iandchasse/silkscreen-pcb/docs/audit-2026-09-30/reports/04_docs_sweep_1.01.md

# Docs staleness check (rev 1.01 x3 3V3 fix)

> Run on 2026-09-30, before commit `3edd0c8` existed: **HEAD / OLD / CONTROL = `6871962`** (design and production files
> identical to `aeb5b39`, the Rev 1.0 order) and **working copy / NEW / FIX = the change later committed as `3edd0c8`** (1.01).
> Evidence paths (`A_trim/`, `C_fab/`, `layout/` ...) are under [`../evidence/`](../evidence/), a local-only pack (git-ignored).

Status: complete -- see end of file

## Findings

### A1. x3 / trimmed-build charging statements (tracked files)
- INFO: No tracked doc ever stated that a trimmed board loses charging / Q2 / R81 / CE 3V3, and no tracked doc mentions a bodge wire. The issue lived only in untracked NOTICE.md. Nothing tracked becomes false.
- README.md:375-393 "Cutting the board down for a smaller display" lists what you lose (J6, U8, CR2, CR3, F2, SW10, H1, D3/D8). Still accurate after the fix (D3/D8 loss = owner's accepted risk).
- docs/HARDWARE.md:1570 cut-line row: "y = 61.86, x 84.42 ... 104.24 -- cutting here removes J6 with its protection parts (U8, CR2, CR3, D3, D8, F2), SW10 and mounting hole H1". Still accurate. Optional wording (info): append "3V3 to the Fix 4 charge-enable gate (Q2/R81) is fed from below the line, so a shortened board still charges."
  (Note: HARDWARE.md says cut line y = 61.86 while NOTICE.md/x3 trim uses y 62.00 -- pre-existing, not changed by this commit.)

### A2. Revision naming
- WARN: README.md:456 "| **Revision** | **Rev 1.0.** The revision label on both title blocks and in the name of the release zip changes only when a new board is fabricated; until then every change is folded into Rev 1.0. The design content is current to **2026-09-21** ..."
- WARN: docs/HARDWARE.md:37 same statement: "The design content is current to **2026-09-21**".
  Rev 1.0 WAS fabricated (ordered 2026-09-21, README.md:87-88). This commit changes copper + silk after that order, but keeps the "1.0" label, the same zip name and the "current to 2026-09-21" date. After push, "design content is current to 2026-09-21" is false, and the repo files no longer match the Rev 1.0 boards that were ordered.
  Minimal wording (keeping the owner's convention, not inventing one): change the date to the commit date and add one sentence, e.g.
  "The design content is current to **2026-09-30**. Changes since the 2026-09-21 order: one added 3V3 trace below the cut line so a shortened (x3) board still charges, and one silkscreen word. Boards from the 2026-09-21 order lack that trace."
  If the owner prefers a label bump, the stated rule ("changes only when a new board is fabricated") would make this Rev 1.01 at the next order; title block and zip name would then change together.
- INFO: Existing history-like sections: docs/HARDWARE.md:1429 "## 15. What changed from de-link" (a de-link -> Silkscreen summary, explicitly "rather than a commit-level changelog"). No per-revision changelog / revision history section exists in README.md, HARDWARE.md or fabrication/*.md. There is no conventional home for a Rev 1.01 entry; the Revision row (README.md:456 / HARDWARE.md:37) is the only place revision state is described.
- INFO: zip name Silkscreen_Reader_PCB_1.0.zip referenced at README.md:141, :151, :467 (still correct - file name unchanged).

### A3. Welcome silkscreen text
- INFO (image, public): docs/images/board-top.png (README.md:20 hero render, last changed 92b3e74 2026-09-21) visibly prints "All components will be on the back of this board, maximizing cost and / simplicity for DIY." After this commit the board says "cost-savings". Cosmetic mismatch only; re-render board-top.png (and board-bottom.png for the new B.Cu trace) at the next render pass, or accept.
- INFO (dated review archive, leave as-is): docs/final-review-2026-09-19/sections/11_mechanical_enclosure_assembly.md:655 quotes "All components will be on the back of this board, maximizing cost and simplicity for DIY"; docs/final-review-2026-09-19/sections/13_docs_end_user_readability.md:95-96 quotes the same text. These are dated snapshots of the 2026-09-19 review; they describe the board as it was. No edit needed (optionally a one-line "text since changed to 'cost-savings'" note, not recommended).

### A2b. Release-record dates made stale by the regenerated zip (fabrication/README.md)
- WARN: fabrication/README.md:32 (Release records table, Gerbers/drills row): "Toolkit output, regenerated 2026-09-21 after the slot, QR code, `U14`, `F2`, `R83`, `C34`, `H6` and the `H5` move. Checked against the saved PCB the same day: identical coordinate operations on `B.Cu`, `F.Cu`, ... `F.Silkscreen` ..." -- the zip being committed was regenerated ~2026-09-30 and now carries the new 3V3 trace, the PWR_BUTTON/LED_SW reroutes, the moved GND via and the silk word. The row's date and change list become false; the "checked the same day" claim no longer covers the file in the repo.
  Minimal wording: "Toolkit output, regenerated 2026-09-30 after one added 3V3 trace below the cut line (a shortened board still charges) and a one-word silkscreen edit; before that, 2026-09-21 after the slot, QR code, ... Re-verify after any board change." Drop or re-date the "Checked against the saved PCB the same day" sentence unless the gerber comparison is repeated for this zip.
- WARN (minor): fabrication/README.md:11 "The files in `production/` were regenerated on 2026-09-21 after those changes (see the table below)". After this commit the zip and netlist.ipc are from ~2026-09-30 (positions/bom/designators/jlc_bom are byte-identical to the 2026-09-21 set). Minimal wording: "... were regenerated on 2026-09-21 after those changes, and the Gerber zip and `netlist.ipc` again on 2026-09-30 after the 3V3 trace fix (see the table below) ..."
- INFO: fabrication/README.md:20 "production/other_fabs/ (last regenerated 2026-09-21, 165 placed parts)" -- still true: other_fabs holds BOM/centroid/assembly-drawing files, and no footprint/placement changed. README.md:295-299 says other fabs "use the same Gerber zip as the JLCPCB order" -- still true.
- INFO: fabrication/README.md:10 "184 references = 165 fitted + 11 DNP + 8 bare-copper ... as of 2026-09-21" -- still true (no reference change).

### A2c. Plots / renders that this change makes non-current
- WARN: docs/HARDWARE.md:39-41 "> **Current full plots (2026-09-21):** [`silkscreen_pcb_schematic.pdf`] ... and [`silkscreen_pcb_layout.pdf`] (PCB layout: front view, then the back as you see it) are ... plotted from the current source." docs/silkscreen_pcb_layout.pdf was last committed in aeb5b39 (2026-09-21 02:42), the same commit as the last committed board, so it is current at HEAD and becomes stale with THIS commit (no new 3V3 trace/reroutes, old Welcome wording). README.md:525 links the same "PCB layout PDF". Minimal fix: re-plot docs/silkscreen_pcb_layout.pdf in this commit, or reword to "Current full plots (schematic 2026-09-21; layout 2026-09-21, before the 2026-09-30 3V3 trace below the cut line)". The schematic PDF is unaffected (no schematic change).
- INFO: docs/images/board-top.png / board-bottom.png (README.md:20) predate the change (see A3). No text claims they are current; cosmetic.
- INFO: docs/mechanical/silkscreen_pcb.step (README.md:429, HARDWARE.md:1547 "authoritative source is the 3D model") contains only the board body and components (no track or silkscreen solids; grep finds only PRODUCT 'silkscreen_pcb_PCB'). No outline/footprint change in this commit, so it stays valid.
- INFO: production/other_fabs/assembly_drawing_bottom.pdf -- assembly drawing; no footprint change, stays valid.

## Scope B -- sibling repos (report only; not changed in this commit)

### silkscreen-light-strip (tracked files, HEAD b44f225 2026-09-30)
- WARN: docs/DESIGN.md:34 "**The trim also cuts 3V3 to Q2/R81**, so the charger's enable stays low and the x3 board will not charge. ... the next silkscreen-pcb revision fixes it with one trace (see that repo's `NOTICE.md`)." -- after this push the fix exists and NOTICE.md is gone (dangling pointer).
  Minimal wording: "**On boards from the 2026-09-21 order, the trim also cuts 3V3 to Q2/R81**, so the charger's enable stays low and the x3 board will not charge. One wire from a retained 3V3 point to Q2 pad 2 / R81 pad 2 fixes a built board. silkscreen-pcb fixed it on <date/commit> with a 3V3 trace below the cut; boards made from those files charge after the trim."
- WARN: docs/DESIGN.md:331 "5. **Board issues on the x3 build** (§1): no D3/D8, and the trim cuts 3V3 to the charger enable. Both are to be fixed in the next silkscreen-pcb revision (one trace for the charger enable), and are tracked in `NOTICE.md` in the silkscreen-pcb repo. Boards already built need the bodge wire described there." -- now false on three counts: D3/D8 will NOT be fixed (owner's decision), the charge-enable fix is done, and NOTICE.md (which held the bodge-wire description) is deleted.
  Minimal wording: "5. **Board issues on the x3 build** (§1): no D3/D8 (accepted; handle the strip ESD-safe). The trim cut 3V3 to the charger enable on boards from the 2026-09-21 order; those need one wire from a retained 3V3 point to Q2 pad 2 / R81 pad 2 (e.g. bridge the two cut 3V3 stubs at the edge). silkscreen-pcb fixed it with one trace below the cut on <date>."
  Note: because NOTICE.md is being deleted, the bodge-wire instructions (bridge the stubs at x 87.53 and 100.60 at y 62, or R40 pad 2 -> R81 pad 2) will survive only if copied into light-strip / case-368 docs or the silkscreen-pcb commit message.
- WARN: enclosures/case-368/README.md:833-838 "**The trim cuts 3V3 to Q2 and R81 (charge enable).** Their only 3V3 feed ran above the cut (KiCad y 60.3-60.8). ... so **the x3 board will not charge.** ... Suggested fix: one wire ..." under heading (826) "Board notes (x3 board with the strip): flagged, not fixed". Now fixed upstream for new boards.
  Minimal wording: prefix "On boards from the 2026-09-21 order, ..." and add "Fixed in silkscreen-pcb on <date> (a 3V3 trace below the cut); boards from those files need no wire." Heading could become "flagged; charge enable fixed upstream".
- WARN: enclosures/case-368/README.md:985-986 "**The Q2/R81 3V3 feed** on the x3 board: as trimmed, the board will not charge. A bodge wire fixes built boards; the next silkscreen-pcb revision fixes it with one trace (its `NOTICE.md`)." -- dangling NOTICE.md reference; fix now done.
  Minimal wording: "... A bodge wire fixes boards from the 2026-09-21 order; silkscreen-pcb fixed it with one trace on <date>."
- INFO: docs/DESIGN.md:33 and :98 (D3/D8 removed by the trim; "the trimmed 3.68" board has neither") -- still true, consistent with the owner's decision. No change.
- INFO: enclosures/case-368/hardware/reference/board-trim.md:152 "3V3 crosses the edge twice and GND uses pours; pad membership alone is not a full connectivity or physical damage analysis." -- still true (the two 3V3 crossings of y 62 remain; the fix adds a path below the cut). Optional add: "Since <date> silkscreen-pcb also joins those two 3V3 feeds below the cut, so Q2/R81 keep 3V3 after the trim."
- INFO: enclosures/case-*/hardware/board-2026-09-21/silkscreen_pcb.kicad_pcb are dated snapshots of the pre-fix board. Correct as snapshots; any future trimmed-board check run from them will still show the two unconnected 3V3 items.

### A1b. Deleting NOTICE.md drops the only in-repo record of the fix for boards already ordered
- WARN: The boards from the 2026-09-21 order (README.md:87-88) were made from the pre-fix files, so a trimmed one still will not charge without a wire. NOTICE.md is the only place in silkscreen-pcb that says so and gives the bodge ("bridge the two cut 3V3 stubs at the edge (x 87.53 and 100.60 at y 62)" or "R40 pad 2 to R81 pad 2"), plus the post-fix check ("DRC on a copy trimmed at y 62 ... no unconnected 3V3 items"; bench "CE reads 3V3 with a correctly oriented cell"). Once it is deleted, README.md:375-393 (public "Cutting the board down" section) lists what a cut loses but never says that Rev 1.0 boards from the first order also lose charging. The light-strip docs point readers to NOTICE.md for the wire (see Scope B).
  Minimal wording, one bullet added to README.md "Cutting the board down for a smaller display": "- **Boards from the 2026-09-21 order: add one wire after cutting**, or the board will not charge. The cut removes the only 3V3 feed to the charge-enable gate (`Q2`/`R81`). Bridge the two cut 3V3 stubs at the edge, or run a wire from `R40` pad 2 to `R81` pad 2. Boards made from the files after <date> have this trace built in." (Alternatively put the same text in the commit message, but a commit message is not where a builder will look.)

### A4. Routing descriptions
- INFO: No tracked doc describes the 3V3 crossings of y 62, PWR_BUTTON routing near y 64-66, LED_SW routing near (98.65, 64.8-65.15) or the moved GND via. README.md:383 "with live copper crossing it" and the dated review FINAL_REVIEW.md:54 / FINDINGS_TABLE.md:86 ("12 live nets ... cross it") stay true: the new trace and all reroutes are below the cut, and both 3V3 crossings remain.
- INFO: D3/D8 wording is consistent with the owner's decision: README.md:385-388 ("A cut board therefore runs its frontlight without those two clamps"), docs/HARDWARE.md:1200-1202, :1570. No doc presents D3/D8 as protecting a trimmed build. (README.md:248 "Don't leave D3 off instead: it protects the light connectors (J3, J6)" is about the full-size board; still true.)

### A5. References to NOTICE.md
- INFO: No tracked file in silkscreen-pcb references NOTICE.md (checked every tracked file, .gitignore included). All tracked "NOTICE" references mean the licence file `NOTICE` (README.md:541, final-review archive DOCS-08/DOCS-15 rows), which stays. Deleting NOTICE.md leaves no dangling link inside this repo.

### A6. Other checks
- INFO: Title block unchanged in both copies: (date "2026-09-12") (rev "1.0"). README.md:456 / HARDWARE.md:37 "the title-block date (2026-09-12) is when Rev 1.0 was opened" stays true.
- INFO: DESIGN_REVIEW.md:9 "the saved manufacturing files match the current board" stays true, given that the owner regenerated the zip after the save.
- INFO (dated audit, leave as-is): docs/audit-2026-09-18/checkpoint-2/status_table.md:85 "welcome-text-missing-noun | low | OPEN | welcome text unchanged ('12-pin accessory connected on the top...')" -- this commit edits the same text box but leaves that wording ("... via 12 pin accessory connected on the top of the other side", visible in docs/images/board-top.png). Optional: while the box is open, "connected" -> "connector". Not required.

### Scope B (continued)
- WARN: silkscreen-site/silkscreen-main/public/order/Silkscreen_Reader_PCB_1.0.zip (tracked in the site repo; dist/order/ has a copy) is byte-identical to the silkscreen-pcb HEAD zip (md5 e138ff6a...). The regenerated working zip is d22ae633..., so after this push the site holds the pre-fix Gerbers under the same file name. scripts/pricing/order_files.py:23-25 copies it from ../../de-link_pcb/production ("the unchanged Gerber zip"). ORDER_FILES_OPEN is false (src/lib/config-data.ts:70), so the builder does not offer it now, but files in public/ are normally deployed as-is. Follow-up in the site repo: rerun `python scripts/pricing/order_files.py` (and rebuild) after the push.
- INFO: silkscreen-site otherwise has no text about the charge-enable island, bodge wire, trim 3V3 crossings or the Welcome wording. Its "Rev 1.0" copy (src/components/build-availability.tsx:216 "the first Rev 1.0 boards were ordered on September 21, 2026", configurator.tsx:1355/1408 "These are the Rev 1.0 files", CLAUDE.md:459 "The board is **Rev 1.0** until another board is fabricated") mirrors the pcb repo's label rule. If the owner keeps "Rev 1.0" (A2), the site's "Rev 1.0 files" will be the post-fix files while "Rev 1.0 boards" are the pre-fix ones -- same naming ambiguity as A2.
- INFO: silkscreen-enclosure-codex-x3 (not a git repo) hardware/reference/board-trim-codex-x3.md:152 "3V3 crosses the edge twice and GND uses pours; pad membership alone is not a full connectivity or physical damage analysis." -- same text as the light-strip copy; still true. Its board copies (hardware/board-2026-09-21/, hardware/frozen/, hardware/silkscreen_pcb-portable.kicad_pcb) are pre-fix snapshots. No charge-enable/bodge/NOTICE.md/Welcome text found in its md/txt/py files (.venv excluded).
- INFO: silkscreen-light-attachment design/final-audit.md:57 (untracked) mentions "untracked `NOTICE.md` (15:13; content "Charge enable loses 3V3 when the board is trimmed (x3 build)" ...)" -- a dated audit observation; no change needed.

Status: complete (22 tool calls). No blocker found.
