iandchasse/silkscreen-pcb/docs/final-review-2026-09-19/FINDINGS_TABLE.md

# All findings — final review 2026-09-19

Generated from the structured results of the 13 auditors and 12 verifiers (`findings.json`). *Severity* is the severity **after** verification; *was* shows the auditor’s original grade where the verifier changed it. 
Verdicts: `confirmed`, `confirmed-with-corrections` (the section file carries the corrected numbers), `refuted`, `unverifiable`, `added-by-verifier`, `not-verified` (section 13, documentation, had no verifier — it is editorial judgement).
Full evidence, calculations and sources for every ID are in the section file named in the last column.

## BLOCKER (1)

| ID | Finding | Verdict | Recommendation | Section |
|---|---|---|---|---|
| LED-01 | J3 (and J2/J4) signal pads have no solder-paste apertures - connectors will not be soldered in a fab-assembled build | confirmed | Add B.Paste to pads 1-N of all three HRS_FH34SRJ-* footprints (or override per-pad on the board), re-export the paste gerber, and re-verify by counting flashes on the connector rows before placing any assembly order. Costs nothing; without it the board returns with no display, no front light and no touch. | [07](sections/07_led_frontlight_driver.md) |

## HIGH (16)

| ID | Finding | Verdict | Recommendation | Section |
|---|---|---|---|---|
| BOM-01 | R14 ordering code has 12 pieces in stock; a fee-free Basic alternative the docs say does not exist *(was BLOCKER)* | confirmed-with-corrections | Change R14's LCSC field to C22939. It is in stock, it is JLC Basic (saves a ~$1.50 Extended loading fee) and it is half the price. The only spec difference is tempco, +/-400 ppm/C vs Yageo's +/-200 ppm/C, which over a 60 C rise is 2.4 % on a current-sense value and immaterial here. Keep Yageo RC0603FR-072R2L as the DigiKey-prim… | [12](sections/12_bom_function_and_cost.md) |
| DOCS-01 | No firmware exists or is linked, and no document says so | not-verified | Add a Software section to the README stating plainly what exists today, where it lives, and the literal first-power-up command. If no firmware is released, say so in the first 20 lines — it changes who should attempt this build. | [13](sections/13_docs_end_user_readability.md) |
| DOCS-02 | The README's recommended ordering route is a configurator that does not exist | not-verified | Demote to a one-line "a configurator is planned at silkscreenreader.com" note and make the manual path in steps 1-7 the primary, unqualified instruction. Remove or re-source the $29.55 figure. Do not describe an unavailable tool as the recommended route. | [13](sections/13_docs_end_user_readability.md) |
| DOCS-03 | Three BOM files offered as interchangeable; two contain duplicate LCSC codes that break the JLCPCB match | not-verified | Name exactly one file in the ordering step: "Upload production/bom_JLC_upload_v4_optimized.csv." Move bom.csv and v3 to a reference note, and state the duplicate-code failure mode in the README where the reader meets it, not only in the NextPCB notes. | [13](sections/13_docs_end_user_readability.md) |
| DOCS-04 | No shopping list for anything that is not on the PCB | not-verified | Add a "What else you must buy" table to the README: panel variant mapped to which optional blocks to fit, with vendor link and price; battery (single-cell 4.2 V, capacity, JST-PH 2.0 connector, pin 1 = B-); microSD; USB-C cable; M2 screws and standoffs; case. | [13](sections/13_docs_end_user_readability.md) |
| DOCS-05 | No safety warning of any kind on a board that charges a lithium cell | not-verified | Add a boxed safety block near the top of the README: LiPo pigtail polarity is not standardised; J5 pin 1 (marked -) is battery negative; meter the cell's leads before plugging in; use a cell with its own protection board; do not charge unattended; do not use a puffed cell. Repeat it in the first-power-up section. | [13](sections/13_docs_end_user_readability.md) |
| DOCS-06 | README's first instruction sends a newcomer into a 100 KB engineering review | not-verified | Re-order the README per the outline in the section file. Keep the DESIGN_REVIEW pointer but place it under "For engineers / before you modify this design", not as step 0 for a builder. | [13](sections/13_docs_end_user_readability.md) |
| DOCS-07 | "Case agnostic" means no enclosure files and no published mechanics | not-verified | Either publish the reference enclosure, even roughly, or add a Mechanical section: outline 60.05 x 111.30 x 1.6 mm, the five M2 hole coordinates, connector and button edge positions, the battery cut-out, and an exported board STEP. State explicitly that no case is supplied. | [13](sections/13_docs_end_user_readability.md) |
| DOCS-08 | Public URL on the board, in NOTICE and in both title blocks lands on a different project | not-verified | Before any board is handed to anyone: merge 06_2026 into master or change the repository's default branch, add a description and topics, and confirm the README renders on the landing page. No other documentation fix matters until a reader can reach the files. | [13](sections/13_docs_end_user_readability.md) |
| DOCS-09 | README says choose JLCPCB "Standard" without preparing the reader for Standard's size, edge-rail and fiducial requirements | not-verified | Explain why Standard is mandatory (the module is Standard-only), and warn that JLCPCB will add edge rails to reach the Standard minimum — expect a rail on each long edge, a small extra cost, and rails to snap or file off. Ask the reader to confirm in the DFM preview that the rails do not cross the four 0.5 mm perforation slots … | [13](sections/13_docs_end_user_readability.md) |
| HMI-01 | Raw LiPo P+ exposed on J6 pin 12 with no fuse, PTC or any series element | confirmed | Fit a 0.5-1 A PPTC (1206) in series with J6 pin 12 and add a BAT+ warning to the silkscreen. About ten cents, and it turns a smoke failure into a click-off failure. Not called a BLOCKER because the DW01A is present and the owner assembles the boards himself. | [08](sections/08_buttons_rtc_touch_expansion.md) |
| LAY-01 | Four tongue-neck routed slots are 0.50 mm wide, below every common fab's minimum slot width | confirmed | Widen all four neck slots to >= 1.0 mm and redraw all five slot polygons at 0.05 mm line width to match the rest of the outline. Get an explicit DFM answer from the fab before ordering; treat this as a blocker if they cannot cut 0.5 mm, because the likely silent outcomes are that the slots are widened (changing the cut line) or… | [10](sections/10_layout_area_walk.md) |
| MEC-01 | Flex slot is 1.30 mm wide — narrower than the 1.60 mm board — and is the only path for all three display flexes *(was BLOCKER)* | confirmed-with-corrections | Widen the slot to >= 2.5 mm, ideally 3.0 mm, and radius or chamfer both lips. A 3 mm slot still leaves 4.05 mm of the 5.75 mm bezel strip below it. Also confirm the fab will route a 47 mm slot that close to the edge. | [11](sections/11_mechanical_enclosure_assembly.md) |
| MEC-02 | The 'cut for smaller displays' line severs raw battery positive 0.15–0.20 mm from ground pour on both layers | confirmed | Add a bold silkscreen warning 'DISCONNECT BATTERY BEFORE CUTTING' next to the existing note. Better: add a 2 mm-wide copper keep-out band centred on y = 61.86 so no copper at all crosses the cut face, or route P+ to J6 by a path that does not cross the line. | [11](sections/11_mechanical_enclosure_assembly.md) |
| MEC-23 | Top face is not flat: 58 soldered through-hole leads protrude inside the panel's footprint | confirmed-with-corrections | Decide and document the panel seating plane. Preferred: clip and file every through-hole lead flush on the panel side during assembly (add it as an explicit build step, with a straightedge check) so the panel can sit flush and the flex slack is preserved. Alternative: design the case to hold the panel on a >= 1.5 mm standoff, a… | [11](sections/11_mechanical_enclosure_assembly.md) |
| SD-V01 | The microSD card-insertion corridor runs straight through the battery cut-out | added-by-verifier | Settle this before the enclosure and ideally before ordering, since one of the three answers is a respin. (a) Confine the cell to the upper-left of the cut-out so a channel at least ~17.5 mm wide and ~20 mm deep stays clear in front of J7, and record the resulting maximum cell dimensions in HARDWARE.md section 5 and in the encl… | [05](sections/05_sdmmc_microsd.md) |

## MEDIUM (70)

| ID | Finding | Verdict | Recommendation | Section |
|---|---|---|---|---|
| BAT-02 | DW01A reference-design R1 (100 ohm from cell to VCC) is not fitted | confirmed | Insert a 100 ohm 0603 between P+ and U5 pin 5, keeping C7 on the U5 side. Sense error is only 0.6 mV at the DW01A's 6 uA supply current. It also current-limits the reverse-polarity fault into U5 (helps BAT-03). HARDWARE.md section 3.3 already notes the omission, but the board as released still does not have it. | [02](sections/02_battery_charger_protection.md) |
| BAT-03 | With a reversed pack the DW01A's VCC sits below its GND, outside absolute maximums | confirmed-with-corrections | Fit BAT-02's 100 ohm (limits fault current into U5), and/or add a small Schottky from U5 VCC to U5 GND with the cathode on GND to clamp the excursion to -0.3 V. HARDWARE.md section 3.3 already describes this fault path; the datasheet citation and the clamp are the additions. | [02](sections/02_battery_charger_protection.md) |
| BAT-V04 | J5 is wired circuit 1 = B-, circuit 2 = B+; SparkFun's published JST-PH convention is pin 1 = +VBATT - possible mismatch with common hobby packs (unverified) | added-by-verifier | Before ordering, hold the intended pack against a 1:1 print or the 3D view and confirm. Write the convention into README in physical terms and name a known-good pack. If the board turns out opposite to the packs most replicators will buy, swapping the two nets at J5 before fab is a five-minute edit (silk must follow); after fab… | [02](sections/02_battery_charger_protection.md) |
| BOM-02 | C4/C6/C32 DigiKey MPN is obsolete with zero stock, and DigiKey's own suggested substitute is also at zero *(was HIGH)* | confirmed-with-corrections | Change the MPN to Murata GRM21BR61E226ME44L: 22 uF 25 V X5R +/-20 % 0805, 1.45 mm max thickness, 1,751,511 in stock at DigiKey, $0.36/1, $0.216/10, $0.1405/100 (verified live 2026-09-20). Same case size and thickness as the Samsung part, so no footprint or height change. One edit unblocks the hand-build, PCBWay and NextPCB BOMs. | [12](sections/12_bom_function_and_cost.md) |
| BOM-03 | JLC stock on three coded lines has fallen sharply since the 2026-09-18 crawl; two cannot cover a 10-board run *(was HIGH)* | confirmed | Re-crawl every LCSC code immediately before placing the order - the figures in BOM.md are two days old and already wrong by four orders of magnitude on one line. Order U10 spares from DigiKey or consign them. For C4/C6/C32 consider C45783 (= CL21A226MAQNNNE, JLC Basic, 1,734,789 in stock, $0.1185, verified live): about $0.25/bo… | [12](sections/12_bom_function_and_cost.md) |
| BOM-05 | production/bom.csv still regenerates the duplicate-LCSC bug that was fixed by hand in the v4 upload file | confirmed | Normalise the schematic Value fields: set C24 and C31 to '0.1u' (or all six to '100n') and C20 to '1u'. Then every generated BOM merges correctly by itself, production/bom.csv stops disagreeing with the v4 upload file, and a known, already-experienced JLC matching failure cannot recur. | [12](sections/12_bom_function_and_cost.md) |
| BOM-06 | D8 PESD2IVN-UX is Not For New Designs at DigiKey and no project document says so | confirmed | Buy now for the prototype - stock is adequate and the part is right for the job. Before any volume build, qualify an in-production dual bidirectional array with V_RWM >= 26 V and low capacitance, and add an 'NRND' note against D8 in fabrication/BOM.md so it is not forgotten at the next respin. | [12](sections/12_bom_function_and_cost.md) |
| BOM-07 | DS3231MZ RTC is 25 % of the DigiKey BOM cost and is beaten on price, accuracy and standby current at once | confirmed | For the next revision move U13 to RV-3028-C7: 5x better accuracy, ~50x lower standby current (which directly extends shelf life on a reader that spends most of its life asleep), and $11.44/board cheaper. If ppm-level accuracy is not actually needed, NXP PCF85063ATL is ~$0.60. Both need a schematic/footprint change, so this is a… | [12](sections/12_bom_function_and_cost.md) |
| BOM-09 | The lithium charge-and-protect subsystem is entirely untraceable clone-market silicon with no Western distributor source | confirmed | Two options, not mutually exclusive. (a) State explicitly in BOM.md that U11/U5/Q1 are LCSC/Asia-only clone parts with no traceable source, and that the LiPo pack must carry its own protection PCM so this board's protection is a second layer rather than the only one. (b) For a future revision move to traceable silicon: the char… | [12](sections/12_bom_function_and_cost.md) |
| BOM-V01 | The five TPD4E1U06 ESD arrays are the 4th-largest cost line and were never critiqued for necessity | added-by-verifier | Decide per array whether the port is genuinely user-exposed and record the decision. Dropping the two or three internal-only arrays saves roughly $1.76/board at DigiKey with no functional cost on a prototype; keeping all five is also defensible as cheap insurance and is the right answer if FCC/EMC work is planned later. Either … | [12](sections/12_bom_function_and_cost.md) |
| DOCS-10 | No cost or lead-time expectation anywhere in the README | not-verified | Put a two-line expectation at the top of the ordering section: about $260-305 for five assembled boards including shipping, about 2-3 weeks from upload to parcel, panel/battery/case extra. | [13](sections/13_docs_end_user_readability.md) |
| DOCS-11 | Undefined jargon throughout the ordering path | not-verified | Add a short glossary box immediately before the ordering steps defining Gerber, BOM, CPL/centroid, PCBA, DNP, THT/SMD, LCSC and Basic/Extended in one line each. Replace "Fix 4" with what it is (the reverse-battery protection change). | [13](sections/13_docs_end_user_readability.md) |
| DOCS-12 | No first-power-up checklist, no troubleshooting, and no route to get help | not-verified | Add a "First power-up" section (inspect, USB-C only with no battery, check the red LED and USB enumeration, then battery) and an "It doesn't work" section with the five likeliest causes ranked, plus one "Where to get help" line with a real URL. | [13](sections/13_docs_end_user_readability.md) |
| DOCS-13 | The assembly drawing, the one artefact that lets a novice audit the placement preview, is filed under the wrong fab | not-verified | Reference the drawing in the JLCPCB step too: "open production/other_fabs/assembly_drawing_bottom.pdf beside the preview and compare part by part." Consider moving it out of other_fabs/, since it is fab-independent. | [13](sections/13_docs_end_user_readability.md) |
| DOCS-14 | The through-hole decision is presented as a checkbox rather than a costed choice | not-verified | State both options with their numbers: (a) let the factory solder them, adding a one-off hand-soldering fee and about a day; (b) decline and hand-solder 13 parts / 74 joints per board including a 20-pad USB-C. Recommend (a) for a first board. | [13](sections/13_docs_end_user_readability.md) |
| DOCS-15 | Licence section does not answer whether a reader may build or sell one | not-verified | Add three plain sentences: you may build it, use it and sell it; if you modify the design and distribute or sell the result you must publish your modified source under CERN-OHL-S v2; keep the NOTICE with it. Link THIRD_PARTY.md for the vendored symbol/footprint caveat. | [13](sections/13_docs_end_user_readability.md) |
| DOCS-16 | "Minimum quantity is 5" conflates the bare-board MOQ with the assembly quantity | not-verified | Reword: "You must buy at least 5 bare boards, but you can choose to have only 2 of them assembled — the cheapest way to get a working prototype, with three spares for later." | [13](sections/13_docs_end_user_readability.md) |
| DOCS-17 | README never says KiCad is not required, and opens with kicad-cli commands that imply it is | not-verified | Open the ordering section with "You do not need KiCad — everything you upload is already in the production/ folder; download the repository as a ZIP and you are ready." Move the kicad-cli blocks to a maintainers' "Regenerating the files" section near the end. | [13](sections/13_docs_end_user_readability.md) |
| DOCS-18 | The four 0.5 mm perforation slots are raised as a manufacturing risk and left unresolved | not-verified | Resolve it once and document the outcome: either "accepted on two previous orders — proceed and accept the DFM notice", or the exact reply to give if the factory queries them. A nervous reader stops at an unresolved warning. | [13](sections/13_docs_end_user_readability.md) |
| DOCS-24 | README gives the wrong polarity rule for D2 and contradicts the repository's own BOM | not-verified | Correct both README occurrences to "pad 1 is the cathode". The consequence is cosmetic rather than damaging — D2 is only the USB-present indicator, so a reversed part simply never lights — but it is the single concrete polarity rule given to a novice and it is inverted. | [13](sections/13_docs_end_user_readability.md) |
| FAB-01 | Smallest annular ring on the board is 0.150 mm, below JLCPCB's stated absolute minimum of 0.18 mm; J1's pad hole-to-hole is exactly at JLC's 0.45 mm limit | confirmed | Accept knowingly. Growing J1's pads to reach 0.18 mm would cut the pad-to-pad copper gap from 0.15 mm to 0.09 mm, trading one marginal number for a worse one. For a JLCPCB order expect a DFM query on J1 and be ready to approve as drawn; PCBWay meets 0.15 mm exactly and NextPCB has 60% margin. | [09](sections/09_erc_drc_fab_outputs.md) |
| FAB-02 | Silkscreen lettering is about half the minimum legible size at every fab, and both DRC checks that would catch it are switched off | confirmed | Either raise all reference designators to >=0.8 mm height / >=0.15 mm stroke and accept some new silk-over-pad overlap, or knowingly treat the printed legend as decorative and rely on assembly_drawing_bottom.pdf plus InteractiveHtmlBom. Either way re-enable text_height and text_thickness so the decision is recorded rather than … | [09](sections/09_erc_drc_fab_outputs.md) |
| FAB-03 | No solder-mask dam between the 0.5 mm-pitch FPC pads of J2/J3/J4; the DRC check that reports it is switched off | confirmed | Set the local solder-mask expansion on J2, J3 and J4 to 0.000 mm, which restores the full 0.200 mm dam (2x JLC's minimum), then re-enable solder_mask_bridge and re-run DRC. | [09](sections/09_erc_drc_fab_outputs.md) |
| FAB-06 | 25 starved thermal reliefs, two of which connect only to an isolated island of the ground pour | confirmed | Add a stitching via immediately beside U11 pad 1, J7 pads 6 and 9, U2 pad 1 and the two isolated-island button pads (SW4, SW9), or set those specific pads to solid zone connection. | [09](sections/09_erc_drc_fab_outputs.md) |
| FAB-10 | bom_JLC_upload_v3.csv is offered as a live alternative but still carries the duplicate-part-number defect that v4 was created to fix | confirmed | Either fix v3's duplicate lines the way v4's were fixed, or retire the file to production/backups/. A documented alternative that is known to mis-match three capacitors is worse than no alternative; at minimum the README should say so. | [09](sections/09_erc_drc_fab_outputs.md) |
| FAB-14 | Two opposite bottom-side rotation conventions in the repo's centroid files, undocumented in the files themselves | confirmed | Put one header line in each centroid file stating the convention (bottom-side angle measured from the top view), and require the assembler to confirm against other_fabs/assembly_drawing_bottom.pdf and the online placement preview before the run. Never mix a JLC CPL with a NextPCB BOM. | [09](sections/09_erc_drc_fab_outputs.md) |
| FAB-16 | No fiducials anywhere on the board, on either side | confirmed | Add two or three 1 mm copper / 2 mm mask-opening fiducials on B.Cu, diagonally opposite, in the free space near H1 and H3 — or explicitly order breakaway rails with fiducials. All three fabs panelise a 60 x 111 mm board with rails and add their own, so this will not stop the order, but board-level fiducials cost nothing and rem… | [09](sections/09_erc_drc_fab_outputs.md) |
| FAB-21 | JLC rotation-correction database has no entry for U2 (SOT-583), U10 (SOT-563), D8 (SOT-323) or any of the diode/LED packages | confirmed | Before confirming a JLC order, set 'Confirm Parts Placement' to Yes and check pin 1 of U2, U10, U11, U13, D8, D2, D3, CR1, CR2, CR3 and D4-D6 against the datasheets in the preview. Add U10 to the documented preview checklist. | [09](sections/09_erc_drc_fab_outputs.md) |
| FAB-22 | production/bom.csv splits two LCSC codes across two lines each — the exact fault that left parts unmatched at JLC before | confirmed | Make the Value strings consistent in the schematic (C24/C31 to '0.1u', C20 to '1u') so every generated BOM merges them automatically; or upload bom_JLC_upload_v4_optimized.csv, which already merges them. | [09](sections/09_erc_drc_fab_outputs.md) |
| FAB-23 | Four interior routed slots are 0.716 mm wide, below JLCPCB's and PCBWay's minimum non-plated slot width | confirmed-with-corrections | If the snap-off feature these slots create must work, widen them to >=1.0 mm before a JLCPCB order. Otherwise expect them to be queried, silently widened to the bit size, or dropped — and correct the '0.5 mm' figure in both READMEs. | [09](sections/09_erc_drc_fab_outputs.md) |
| HMI-02 | Three ESP32-S3 strapping pins on the expansion header behind only 33 ohm resistors *(was HIGH)* | confirmed-with-corrections | Add 4.7-10 kohm pull-downs to GND on GPIO45 and GPIO46 close to U4 so they are robust against a 10 kohm external pull-up. Add a loud 'GPIO45/46 must be low at reset' warning to the header documentation and silkscreen. Longer term, prefer non-strapping pins on the header. | [08](sections/08_buttons_rtc_touch_expansion.md) |
| HMI-03 | DS3231MZ has no backup cell, so the clock does not survive power loss | confirmed | Either (a) accept and document clearly that the RTC gives accuracy while powered only, or (b) next spin move 3V3 to VCC and put a CR1225 or supercap on VBAT, which is what the part is designed for. Firmware must in any case check the oscillator-stop flag rather than assume valid time at first power-up. | [08](sections/08_buttons_rtc_touch_expansion.md) |
| HMI-04 | RTC INT/SQW is unrouted, so the DS3231's alarms cannot wake the MCU | confirmed | Route INT/SQW to a free RTC-capable GPIO (IO0-IO21) with a 10-100 kohm pull-up to 3V3, or state plainly in the firmware-interface docs that RTC alarms are unavailable. | [08](sections/08_buttons_rtc_touch_expansion.md) |
| HMI-07 | Mutually exclusive 0 ohm option pairs are unmarked; R73+R74 both fitted shorts 3V3 to GND | confirmed-with-corrections | Make R74 100 ohm instead of 0 ohm: a both-fitted mistake then draws 33 mA instead of shorting the rail, and the power-button divider still reads 2.99 V. For the touch pairs make the TP_INT-side jumpers R43 and R44 100 ohm - NOT R42/R66, which carry the panel's VDD and must stay 0 ohm (100 ohm against a ~20 mA touch controller w… | [08](sections/08_buttons_rtc_touch_expansion.md) |
| HMI-10 | Bottom-edge buttons sit ~1.0 mm closer to the board edge than the side buttons | confirmed | Confirm against a physical MJTP1117 before cutting an enclosure. If the difference is not deliberate, move the bottom row about 0.96 mm inboard (pads y 146.45 -> 145.49) so all eight actuators share one standoff and the case can use a single bezel depth. | [08](sections/08_buttons_rtc_touch_expansion.md) |
| HMI-V01 | R72/R74 are flagged dnp but not exclude_from_bom, so the rail-shorting jumper survives into BOM exports | added-by-verifier | Set exclude_from_bom on R72 and R74 so all six DNP jumpers are handled identically and no exporter can leak them. That moves the mitigation out of one fab's hand-edited BOM and into the schematic itself. Combine with HMI-07's suggestion to make R74 100 ohm rather than 0 ohm, so that even a both-fitted board draws 33 mA instead … | [08](sections/08_buttons_rtc_touch_expansion.md) |
| HMI-V02 | The silkscreened "cut the long end" option has a ~1.9 mm cut window bounded by the battery connector, and no cut line is drawn | added-by-verifier | Draw a dashed cut line on the silkscreen at y = 62.0 mm with a 'cut here' label - it costs nothing before ordering and turns a guess into an instruction. Add a note that the cut also removes mounting hole H1, so the enclosure must not depend on it. The existing R36/R73-out, R72/R74-in electrical instruction is correct and needs… | [08](sections/08_buttons_rtc_touch_expansion.md) |
| HMI-V03 | MJTP1117 is APEM's grounding variant, yet every switch cover is left floating - and the I2C bus passes 0.151 mm from two of those floating rings | added-by-verifier | Net pads 3 and 4 to GND on the four side switches (SW1, SW4, SW5, SW7) - they carry no front-mount tabs, so nothing breaks and finger ESD gets a drain path. Leave the bottom four netless for the front-mount option, but move I2C_SCL and I2C_SDA further from SW1's and SW4's rings on the next spin. This is a damage-in-normal-use i… | [08](sections/08_buttons_rtc_touch_expansion.md) |
| LAY-02 | The documented tongue cut line leaves 12.3 mm of solid 1.6 mm FR-4 and cannot be snapped by hand | confirmed | Either commit to a real break-away (a mouse-bite drill row on ~1 mm pitch, or a V-score) or relabel the dashed line as 'cut with a saw'. Add a printable warning that the cut severs P+, 3V3 and GND and must be deburred, and note that the power button SW10 at (101.8,54.8) goes with the tongue. | [10](sections/10_layout_area_walk.md) |
| LAY-04 | Essentially all silkscreen on the board is below the fab's minimum printable size, including the battery polarity mark *(was HIGH)* | confirmed-with-corrections | Raise all reference designators to >= 0.8 mm height / 0.15 mm stroke (1.0 mm / 0.15 mm to be safe) and every board note to >= 1.0 mm / 0.15 mm. Prioritise two items: the J5 polarity mark (a LiPo safety marking that currently may not print at all) and the tongue-cut instructions, which are the board's key user procedure and exis… | [10](sections/10_layout_area_walk.md) |
| LAY-05 | B.Cu ground is fragmented into 50 fill areas, 14 of them with no via to the F.Cu plane *(was HIGH)* | confirmed-with-corrections | Add GND stitching vias so every B.Cu island above ~20 mm2 has at least one tie to F.Cu -- at minimum in the bottom button strip, the SD area and around both converters. A dozen extra vias cost nothing and halve the return-path length for most of the 175 bottom-side parts. | [10](sections/10_layout_area_walk.md) |
| LED-02 | External LED strings with low forward voltage are driven uncontrolled through L2 and U10's high-side body diode *(was HIGH)* | confirmed-with-corrections | Add a minimum string voltage to the silkscreen text box and to docs/HARDWARE.md section 7 - e.g. 'at least 3 LEDs in series (Vf > 6 V)' - next to the existing 22 V maximum. No board change is needed; this is a guidance gap with a real component-damage consequence. | [07](sections/07_led_frontlight_driver.md) |
| LED-12 | J3 pin mapping to the Good Display front-light flex is unverified from any primary source | confirmed-with-corrections | Make this a bring-up gate rather than a board change: before first power-on with any new panel lot, diode-test the flex or the J3 mating pads with a meter (or probe TP3/TP4/TP5) and confirm pins 1 and 5 are the anodes. Record the FPC revision with the result. I could not verify this myself and am reporting it at low confidence. | [07](sections/07_led_frontlight_driver.md) |
| LED-14 | The on-board dimming note (10-25 kHz) cannot enable the driver: ADIM doubles as the enable and needs a >40 us first pulse | confirmed | Firmware must emit an explicit enable pulse (>=100 us HIGH for margin) before applying the dimming carrier. Add that one sentence to the schematic design-note text box, since that box is the first thing someone replicating the board reads. Symptom if missed is 'the front light never comes on', which is an expensive way to lose … | [07](sections/07_led_frontlight_driver.md) |
| LED-V02 | Open-load OVP latches after three trips - re-applying the PWM carrier will not restart the driver, and nothing on the board or in the docs says so | added-by-verifier | Make the firmware's front-light enable a fixed three-step sequence and put it in the schematic design-note text box and docs/HARDWARE.md: (1) PWM_LED LOW for >=3 ms to clear any latched OVP; (2) a single HIGH pulse >=100 us to satisfy tADIM_EN = 40 us with margin; (3) start the 10-25 kHz dimming carrier. No board change. | [07](sections/07_led_frontlight_driver.md) |
| MCU-01 | BOOT button SW6 is DNP — no fitted way into download mode when USB-Serial/JTAG is unavailable *(was HIGH)* | confirmed-with-corrections | Fit SW6 (APEM MJTP1243 or equivalent 6 x 3.5 x 4.3 mm THT tactile) on every prototype. The land is already on the board and the part costs cents. Until then, note that recovery means shorting SW6 pad 2 to GND with tweezers while pressing SW11. | [04](sections/04_esp32_core_gpio_map.md) |
| MCU-13 | Sibling firmware's DE_LINK profile and delink build env do not match this PCB at all *(was HIGH)* | confirmed-with-corrections | Do not flash the stock 'delink' build onto this board. Create a new BoardProfile with this board's pin map and a new PlatformIO env with board_build.arduino.memory_type = qio_opi (quad flash + octal PSRAM). The existing 33 ohm series resistors are what would keep a mis-flash from destroying pins — keep them. | [04](sections/04_esp32_core_gpio_map.md) |
| MCU-14 | Metal and copper within ~1 mm of the module's PCB antenna on both flanks | confirmed-with-corrections | Accept for this prototype but MEASURE RSSI and throughput before blaming firmware. If range disappoints, move SW5 a few mm toward the SD socket and R4 out of the antenna's flank in the next spin, and move L2 (a switching node) further from the antenna. | [04](sections/04_esp32_core_gpio_map.md) |
| MEC-03 | The cut line cannot be snapped: 57% of the tab width is solid FR4, 12 live nets and two pours cross it, and 0.516 mm slots are below common fab minimums *(was HIGH)* | confirmed-with-corrections | Decide which it is. If the intent is 'saw and file', say so on the silkscreen so nobody tries to snap it. If the intent is a break-off, add a genuine V-score or a mouse-bite line leaving 20–30% web and keep copper off it. Either way confirm with the fab that 0.516 mm internal slots are acceptable before paying. | [11](sections/11_mechanical_enclosure_assembly.md) |
| MEC-04 | J5's mouth faces +x, away from the battery bay — the cell leads must U-turn 180° and run ~18 mm back across the tab | confirmed | Rotate J5 180° so the mouth faces −x, into the bay. If that cannot be done this spin, the case must mould a wire channel that carries the 180° loop around the plug and past SW4, plus a strain-relief post near (84, 65) — J5 is a friction fit with no lock — and a chamfer over the diagonal board edge the leads cross. Document the … | [11](sections/11_mechanical_enclosure_assembly.md) |
| MEC-05 | Touch-flex connector spacing is 0.79 mm wider on the board than on the panel | confirmed-with-corrections | Measure a physical panel before ordering. If the 0.79 mm is real, shift J4 about 0.8 mm toward J2 — there is room, since J4's courtyard ends at x 96.005 and the nearest part, R52, is at x 97.00. | [11](sections/11_mechanical_enclosure_assembly.md) |
| MEC-06 | Flex bend radius at the slot lips is effectively a crease, against a ~1.8 mm guideline | confirmed | Radius or chamfer the slot lips in the board (this pairs naturally with widening the slot per MEC-01), and mould a radiused flex saddle into the case along the full 47 mm of slot so the tails wrap rather than fold. | [11](sections/11_mechanical_enclosure_assembly.md) |
| MEC-07 | Only about +/-0.25 mm of plan-view daylight between the panel's side edges and the side-button plungers | confirmed-with-corrections | Use a two-part case: a front bezel that laps over the panel from above, and a back shell whose side walls sit outside the plunger tips with the button apertures in them. Inner wall >= x 105.6 on the right, <= x 43.1 on the left. | [11](sections/11_mechanical_enclosure_assembly.md) |
| MEC-09 | SW11 (RESET) stops 3.54 mm short of the board edge and D2 sits in its plunger path | confirmed | Move SW11 out to x ≈ 101.4 to match SW1/SW4 and relocate D2, or accept RESET as an internal-only, case-open control and write that down alongside the existing BOOT rationale in README.md. | [11](sections/11_mechanical_enclosure_assembly.md) |
| MEC-V01 | J4's footprint origin sits 0.730 mm away from its own pad centroid, so every position-derived document mislocates it | added-by-verifier | Re-anchor J4 to its pads next spin (select the footprint, set the anchor to pad 1 or the body centre). Before ordering: regenerate the pick-and-place file and check J4's row against x 93.23 before sending it to any assembly service, and correct board_extract.json-derived figures anywhere they are quoted. Hand-soldering directly… | [11](sections/11_mechanical_enclosure_assembly.md) |
| MEC-V02 | Cutting the board on the "cut for smaller displays" line also amputates the PWR button (SW10), not just the expansion header | added-by-verifier | State on the B.Silkscreen next to the existing cut note, and in README.md, that the cut removes the expansion header AND the PWR button. Note the firmware consequence too: SW10 sits on the resistor-ladder branch through R62, so after the cut that branch is left dangling and the ADC codes the firmware matches against will shift.… | [11](sections/11_mechanical_enclosure_assembly.md) |
| PWR-01 | LDO is thermally limited to ~240-280 mA continuous on USB, not its rated 500 mA | confirmed-with-corrections | Document the real ceiling (~250 mA continuous on USB). Pour copper onto U3's IN, OUT and GND pads - the leads are the only heat path on a DBV. Fix PWR-05 (single GND thermal spoke) at the same time. Keep U3 away from the enclosure's hottest corner: the TP4056 next door is dissipating (5 - Vbat) x 255 mA simultaneously. Have fir… | [03](sections/03_ldo_power_tree_sleep_budget.md) |
| PWR-07 | Touch panel and e-paper panel are permanently powered from 3V3 with no load switch and no measured standby current | confirmed | Measure both on the first prototype: cut/lift R42 and measure the touch branch, and measure the J2 3V3 branch with the panel attached and asleep. If either exceeds ~20 uA, add a P-FET load switch modelled on Q7/R40/R78 (the touch one is trivial - R42 is already a jumper position). | [03](sections/03_ldo_power_tree_sleep_budget.md) |
| SD-01 | SD_VDD is back-fed to 3.24 V through the five 10k pull-ups whenever the bus is driven high with the gate off | confirmed | Keep the schematic note but make it exact and testable: before raising SD_ACTIVATE, drive GPIO5/6/7/15/16/17 LOW as outputs - including CLK, which has no external pull-up but still injects current into the unpowered card's input clamp - and explicitly disable the internal pull-ups; hold >= 20 ms. Add the same rule to docs/HARDW… | [05](sections/05_sdmmc_microsd.md) |
| SD-02 | ESD clamps are 11-23 mm from the socket contacts they protect | confirmed-with-corrections | Accept for the prototype - the 33 Ohm series resistors still protect the MCU itself, and a microSD socket is not a certification item yet. On any respin move U1 (and ideally a second array for DAT0/DAT1) to within ~3 mm of J7's contact row, on the socket side of R21-R26, and tighten J7's shield-to-ground connection (SD-09), sin… | [05](sections/05_sdmmc_microsd.md) |
| SD-04 | The J7 BOM row names three different manufacturers' parts | confirmed | Pick one primary: put the GCT MPN plus its DigiKey part number in the primary fields and move C393941 into an explicit "Alt MPN / LCSC" field with a note that the land accepts both. Replace the Wuerth datasheet URL with the GCT MEM2075 drawing. An amateur replicating this board from the BOM as it stands will order the wrong soc… | [05](sections/05_sdmmc_microsd.md) |
| SD-05 | Socket mouth sits 1.78 mm inside the board edge; an ejected card may not protrude enough to grip through an enclosure wall | confirmed-with-corrections | Measure the actual pop-out stroke on a real socket before cutting an enclosure. If it is <= 4 mm, put a finger notch or a flared slot in the enclosure wall at that edge. On a respin, shifting J7 ~1.8 mm toward y = 67.5 makes the mouth flush; the pegs (y = 73.4) and C36/C37 would move with it and nothing collides. Remember the s… | [05](sections/05_sdmmc_microsd.md) |
| USB-01 | "Charger idle" window (> 3.10 V) is outside the ESP32-S3 ADC's specified range and can never be reported *(was HIGH)* | confirmed-with-corrections | Change the schematic note and the firmware threshold from "> 3.10 V" to "> 2.6 V". Nothing physically sits between 2.07 V (top of the battery state including ADC error) and 3.27 V, so there is a 1.2 V gap to land in. No board change needed. HARDWARE.md §3.7 already carries this caution; only the schematic was not updated (USB-1… | [01](sections/01_usb_input_power_path.md) |
| USB-02 | Three different physical states collapse into the single 0.50-0.70 V "fully charged" window | confirmed | Re-plan the windows with explicit guard bands (proposed table in the section file), or change R17 from 150k to 1 MΩ so the ST states stop colliding with the charger states (ST-low states then become 2.91 / 1.16 / 0.59 V). Decide whether this pin reports charge state or power source and measure one of them well. HARDWARE.md §3.7… | [01](sections/01_usb_input_power_path.md) |
| USB-03 | TPS2116 PR1 comparator has no hysteresis, allowing switchover chatter on a weak supply | confirmed-with-corrections | Add a ~1 MΩ resistor from ST (open drain) to /PR1. When ST pulls low, the PR1 divider becomes 300k against 100k||1M = 90.9 kΩ, so the VBUS needed to bring PR1 back to 1.00 V rises from 4.00 V to 1.00 x (300+90.9)/90.9 = 4.30 V - about 300 mV of clean hysteresis. Add the footprint now even if fitted DNP. | [01](sections/01_usb_input_power_path.md) |
| USB-04 | CR1 clamp voltage is above the absolute maximum of the parts it protects | confirmed-with-corrections | Substitute a 5.0 V-class TVS such as SMF5.0A (V_RWM 5.0 V, V_BR min 6.4 V - still never conducts at USB's 5.25 V maximum, but clamps roughly 2 V lower). Identical SOD-123FL footprint, no layout change, similar price. Fit it while ordering anyway. | [01](sections/01_usb_input_power_path.md) |
| USB-05 | F1 1.00 A hold current has little margin over the ~0.86 A worst-case load and derates hard with temperature | confirmed | Either fit a 1.5 A part (0805L150, same footprint) or have firmware suspend charging while Wi-Fi TX and the front light are both active. Measure the real front-light current first - if it is near 100 mA, treat this as HIGH. | [01](sections/01_usb_input_power_path.md) |
| USB-06 | Entire USB input path is 0.25 mm wide while the battery path was widened to 0.40 mm | confirmed | Widen VBUS_PRE_FUSE and USB_VBUS to 0.5 mm, matching or exceeding P+. Copper is free and there is room in this region. | [01](sections/01_usb_input_power_path.md) |
| USB-V01 | Only 0.5 V separates the highest legal USB-C rail voltage from three downstream absolute maxima, so no TVS can protect this rail | added-by-verifier | Stop treating this as a TVS-selection problem. Keep CR1 as the fault clamp it is good at, and add a damping element for the hot-plug transient: 1-1.5 Ohm in series with C2 (the resistor is in series with the capacitor, not the load, so it costs no rail drop at 0.86 A), or an equivalent 1 Ohm + 1 uF RC snubber from USB_VBUS to G… | [01](sections/01_usb_input_power_path.md) |
| USB-V02 | "Fully charged" and the high half of the no-battery oscillation are the same USB_STAT voltage by construction, not merely overlapping | added-by-verifier | Record on the schematic, next to state 3, that 'fully charged' can only be distinguished from 'no battery fitted' by observing the reading over time: require the level to be stable for several seconds (or at least two 1-4 s windows) before declaring charge complete, and treat any alternation between the 0.59 V and 0.45 V levels… | [01](sections/01_usb_input_power_path.md) |

## LOW (150)

| ID | Finding | Verdict | Recommendation | Section |
|---|---|---|---|---|
| BAT-01 | No capacitor from DW01A CS to its GND pin - first-connection inrush can latch the protection off *(was MEDIUM)* | confirmed-with-corrections | Add a 1-10 nF 0603 from U5 pin 2 (CS) to U5 pin 6 (B-). R16 = 1 k is already fitted and forms the RC. One part, lowest-cost insurance in this block; it also stops false … | [02](sections/02_battery_charger_protection.md) |
| BAT-04 | R82 = 1 MOhm is the only default-off pull-down on CE, and CE-low is the sole barrier to reverse-charging a backwards cell *(was MEDIUM)* | confirmed-with-corrections | Lower R82 to 100-220 kOhm (costs 15-33 uA from 3V3 only while a cell is detected) and/or add 100 nF from CE to GND. Leave R81 at 1 M - it is only loaded when Q9 is on. D… | [02](sections/02_battery_charger_protection.md) |
| BAT-05 | No cell-temperature protection during charge: TP4056 TEMP grounded and J5 is a 2-pin connector *(was MEDIUM)* | confirmed | Acceptable for a prototype (it is the same posture as every TP4056 module sold), but state the limitation in the docs, specify a cell that carries its own PCM/NTC, and d… | [02](sections/02_battery_charger_protection.md) |
| BAT-06 | DW01A/FS8205A over-current trip computes to 2.0-4.6 A - a short-circuit protection, not an overload protection *(was MEDIUM)* | confirmed-with-corrections | Inherent to the DW01A + 8205A pair; the fix is cell selection, not a component value. Specify a cell of at least 1000 mAh, or one with its own protection module. If a re… | [02](sections/02_battery_charger_protection.md) |
| BAT-07 | Battery path narrows to 0.25 mm either side of R27 while the rest of it is 0.40 mm | confirmed | Widen Net-(Q3-D) and Net-(Q8-D) to 0.40 mm so the whole battery path is consistent - the traces are short and there is room. Worth doing because P+ is exposed on J6 pin … | [02](sections/02_battery_charger_protection.md) |
| BAT-08 | DW01A GND reference taps the B- run ~8 mm upstream of Q1's S1 pad, putting trace resistance inside the current-sense loop | confirmed | Harmless direction - it trips earlier, not later - but it makes the trip point depend on copper geometry. If the routing can be rearranged, Kelvin the U5 pin 6 connectio… | [02](sections/02_battery_charger_protection.md) |
| BAT-10 | On a battery-only cold start the DW01A measures the cell through Q8's body diode and reads it ~0.4 V low | confirmed-with-corrections | No hardware change needed for a prototype - the lost window is below the useful cut-off anyway. Document it: 'if a freshly connected pack does not bring the board up, pl… | [02](sections/02_battery_charger_protection.md) |
| BAT-11 | J5 polarity silkscreen is correct but sits ~7 mm from the pin row, at the far end of the connector body | confirmed-with-corrections | Keep it - the marking plus the 'CHECK' warning is better than most boards. For a respin, repeat a small '+' immediately beside pad 2. Independently, warn builders in the… | [02](sections/02_battery_charger_protection.md) |
| BAT-V01 | Fix-4 cell detector is self-latching once the charger runs: unplugging the cell with USB present leaves the charger running into an empty connector and BAT_MONIT reading a full battery | added-by-verifier | No hardware change for the prototype. Document it in HARDWARE.md s3.3/3.7; in firmware treat a toggling CHRG (USB_STAT bouncing between charging and no-battery levels) a… | [02](sections/02_battery_charger_protection.md) |
| BAT-V02 | Q3 provides no reverse-polarity blocking as oriented; Q8 alone does the job | added-by-verifier | Leave for this spin (harmless). At a respin either replace Q3 with 0 ohm and rely on Q8 + CE gate + the DW01A 100 ohm R1 (BAT-02), or use a purpose-built reverse-protect… | [02](sections/02_battery_charger_protection.md) |
| BOM-04 | C2 USB VBUS bulk capacitor is 10 V rated on a 5 V hot-pluggable rail and loses ~65 % to DC bias *(was MEDIUM)* | confirmed-with-corrections | Change C2 to a 16 V or 25 V 10 uF 0603 - the same footprint, so no layout change. Candidates to check for stock: Murata GRM188R61E106MA73D (25 V) or GRM188R61C106MA73D (… | [12](sections/12_bom_function_and_cost.md) |
| BOM-08 | The hand-build DigiKey BOM understates parts cost by about 38 %, mostly on two lines *(was MEDIUM)* | confirmed-with-corrections | Replace the 'est' prices with the live figures and restate the hand-build total as approximately $66/board at strict qty 1, or approximately $55/board when buying parts … | [12](sections/12_bom_function_and_cost.md) |
| BOM-10 | D3 SMAJ26A clamps above the TPS923610's absolute maximum, so it cannot protect the driver it sits beside *(was MEDIUM)* | confirmed | Accept for the prototype - the TVS still protects the connector and cable, and U10 has its own internal OVP - but record that U10 itself is not surge-protected. On a res… | [12](sections/12_bom_function_and_cost.md) |
| BOM-11 | R14 is a 100 mW 0603 carrying the EPD boost's switched inductor current; wattage unverified | confirmed | If R14 is being edited anyway for BOM-01, specify a >= 0.25 W part in the same land (e.g. Panasonic ERJ-PA3F2R20V, 0603 0.25 W) or widen the footprint to 0805. Otherwise… | [12](sections/12_bom_function_and_cost.md) |
| BOM-12 | R15 is a 10 k GDR pull-down where the SSD1677 reference specifies 1 M - a 100x heavier load on the panel's gate driver | confirmed | Electrically harmless - with an active push-pull GDR driver the gate edge is set by the driver, not by this resistor - but it is an undocumented deviation from a referen… | [12](sections/12_bom_function_and_cost.md) |
| BOM-13 | The three documented build routes give three different button feels spanning 2.5:1, and half the cycle life on one | confirmed | Decide which feel is the target and make that part the primary MPN rather than letting each fab's stock decide. If the APEM 1.77 N is the intent, note in BOM.md that the… | [12](sections/12_bom_function_and_cost.md) |
| BOM-14 | The L1 substitute is materially worse than the prime part and the substitutes file justifies it only on case size | confirmed | Add the Isat and DCR delta to the Reason column of nextpcb_substitutes.csv so a future reader knows what the substitution costs. Separately, re-check the Sunltech part's… | [12](sections/12_bom_function_and_cost.md) |
| BOM-15 | Four of nine capacitor part numbers are unbuyable at DigiKey today and the BOM gives no specification to substitute against | confirmed | Add a specification column to fabrication/BOM_handbuild_digikey.csv beside the preferred MPN - e.g. '10 uF +/-10 % X5R 0603 >= 16 V', '100 nF +/-10 % X7R 0603 50 V', '22… | [12](sections/12_bom_function_and_cost.md) |
| BOM-16 | The public JLC search API never reports the fee-free Preferred class, so any re-crawl over-counts Extended parts and over-states fees | confirmed | Note in fabrication/BOM.md that jlcsearch.tscircuit.com does not expose the Preferred flag and that library class must be confirmed on jlcpcb.com/partdetail/<code>. This… | [12](sections/12_bom_function_and_cost.md) |
| BOM-V02 | ESP32 module variant, Hirose FH34 connectors and the expansion socket were priced but not cost-critiqued | added-by-verifier | Check what the firmware actually needs: if 16 MB flash / 8 MB PSRAM is not used, N8R2 or N4R2 saves several dollars per board on the second-largest line. Keep the Hirose… | [12](sections/12_bom_function_and_cost.md) |
| DOCS-19 | The project is named five different ways across repo, files, title block and board | not-verified | Pick one public name ("Silkscreen"), state the relationship to de-link once, and add a one-line note that the KiCad files are named silkscreen_pcb for historical reasons. | [13](sections/13_docs_end_user_readability.md) |
| DOCS-23 | No table of contents and no quick-path / deep-dive split in the README | not-verified | Add a table of contents, and put a three-line "I just want one -> jump to Order an assembled board" signpost above it. | [13](sections/13_docs_end_user_readability.md) |
| EPD-01 | No mechanical definition of the panel or its FPC path; reach budget has only ~5 mm slack *(was MEDIUM)* | confirmed-with-corrections | Before ordering panels, lay a 12.5 x 25 mm paper mock-up of the tail over a 1:1 printout and confirm it reaches. Add a panel outline plus a 'fold here' note on User.Draw… | [06](sections/06_eink_driver_connector.md) |
| EPD-03 | Q4 sits at 20.9 V of a 30 V rating with no snubber and unmeasured switch-node ringing *(was MEDIUM)* | confirmed-with-corrections | On bring-up, scope EINK_SW at Q4's drain through a full refresh. If peaks exceed ~26 V, fit a 40 V or 60 V logic-level SOT-23 N-FET (same G/S/D pinout, drop-in) or add a… | [06](sections/06_eink_driver_connector.md) |
| EPD-04 | Panel decoupling and rail-stabilising capacitors are 13-20 mm from the pins they serve *(was MEDIUM)* | confirmed-with-corrections | Accept for this prototype - e-paper logic is slow (SPI <= 20 MHz) - but scope VCI and VDD at J2 during a refresh. On a respin move at least C22 (VDDIO/VCI) and C18 (VDD)… | [06](sections/06_eink_driver_connector.md) |
| EPD-05 | R15 = 10 kohm on GDR where the panel maker's reference circuit specifies 1 Mohm *(was MEDIUM)* | confirmed-with-corrections | If GDR is a normal push-pull CMOS output (overwhelmingly likely) this is harmless and even turns Q4 off faster. But matching the reference is free. If VGH comes up low, … | [06](sections/06_eink_driver_connector.md) |
| EPD-06 | No pull on EPD_CS (floats during ESP32 boot with the panel powered) and none on EPD_BUSY | confirmed | One line of firmware: enable the ESP32-S3 internal pull-up on IO14 (CS) and internal pull-down on IO48 (BUSY) at the very start of app_main. Optionally fit a 10k pull-up… | [06](sections/06_eink_driver_connector.md) |
| EPD-07 | The +/-20 V reservoir caps are 8-9 mm and 2 vias from their rectifiers, so the diodes have no local capacitor | confirmed | Add a 1 uF/50 V 0603 directly at D5's cathode and another at D4's anode on the next spin (two parts, negligible cost). It will work as-is; this is a ripple and radiated-… | [06](sections/06_eink_driver_connector.md) |
| EPD-08 | J2 pins 6/7 labelled TSCL/TSDA and left open; touch is assumed to be on a separate 6-pin tail | confirmed | Confirm with the vendor that the exact touch module ordered brings touch I2C out on a separate 6-pin tail and not on pins 6/7 of the 24-way. If it is on the 24-way, touc… | [06](sections/06_eink_driver_connector.md) |
| EPD-09 | D4/D5/D6 use 1N5819HW, whose reverse leakage is several times the reference MBR0530's | confirmed | Accept for a prototype - the rails are only live during a refresh, so leakage costs energy, not function. If refresh current measures higher than expected, substitute MB… | [06](sections/06_eink_driver_connector.md) |
| EPD-10 | Seven vias sit under J2's body or in the corridor the FPC lies on | confirmed-with-corrections | Confirm in the released gerbers that these vias are solder-mask tented. Zero cost if the fab default is tented; check rather than assume. | [06](sections/06_eink_driver_connector.md) |
| EPD-11 | J2 pad 17 (VSS) reaches the GND pour through a single thermal spoke | confirmed | Set J2's GND pads to a solid zone connection. Current is only a few mA, so this is about inductance in the HV return path rather than heating. | [06](sections/06_eink_driver_connector.md) |
| EPD-V01 | Panel tail flares to 31.3 mm; C17, C22 and through-hole pads TP3/TP4/TP5 sit under it - the 'clear corridor' only covers the 12.5 mm neck | added-by-verifier | No board change needed for the prototype. Allow ~1.5 mm for the flex riding over C17 (1.25 mm tall) in the rear enclosure and do not let the case clamp the tail onto it;… | [06](sections/06_eink_driver_connector.md) |
| FAB-04 | 12 live DRC clearance errors, all inside J1's own USB-C footprint | confirmed | Mark the 12 individually excluded, or add a custom DRC rule scoped to J1, so the report reaches zero errors and a genuinely new error cannot hide in the pile. | [09](sections/09_erc_drc_fab_outputs.md) |
| FAB-05 | The SW netclass imposes 0.250 mm clearance on J3, a connector whose pads are inherently 0.200 mm apart | confirmed | Keep the exclusions, but a netclass exception scoped to connector pads is cleaner than three per-item exclusions. The adjacency of the switching node to the two output p… | [09](sections/09_erc_drc_fab_outputs.md) |
| FAB-07 | Four dangling top-layer track stubs at the bottom button row | confirmed | Delete the four stubs and clear their exclusions, unless they are a deliberate alternate-footprint option. Electrically harmless either way; the cost is only that the ex… | [09](sections/09_erc_drc_fab_outputs.md) |
| FAB-08 | One empty, mirrored text box on the front silkscreen | confirmed | Delete the empty text object so the DRC report is clean. | [09](sections/09_erc_drc_fab_outputs.md) |
| FAB-09 | 49 silkscreen DRC items: 32 clipped by the board edge, 12 printed over exposed copper, 5 overlapping each other | confirmed | Nudge the reference designators of R8, R27, R77 and R78 off their pads and pull the two F.Silkscreen text boxes inside the board outline. The remaining edge-clipping on … | [09](sections/09_erc_drc_fab_outputs.md) |
| FAB-11 | production/bom.csv contains a BOM line with no part number (TP1, TP2) | confirmed | Tick 'Exclude from bill of materials' on TP1 and TP2 in the schematic and re-export, so the warning in the README becomes unnecessary. | [09](sections/09_erc_drc_fab_outputs.md) |
| FAB-12 | 25 footprints differ from their library copy, and the check that reports this is switched off | confirmed | No change needed for this spin. Record it in the build documentation so nobody runs 'Update Footprints from Library' before ordering — that would silently revert the edi… | [09](sections/09_erc_drc_fab_outputs.md) |
| FAB-13 | One wire carries two names (PIN_3 and TP_RST on J4 pin 3) | confirmed | Delete the redundant local PIN_3 label. | [09](sections/09_erc_drc_fab_outputs.md) |
| FAB-15 | The Toolkit and the NextPCB/PCBWay centroids place the 13 through-hole parts up to 6.5 mm apart, by design | confirmed | No change needed — the two files answer different questions and each is right for its fab. Just never mix a JLC CPL with a NextPCB BOM. | [09](sections/09_erc_drc_fab_outputs.md) |
| FAB-17 | Both hand-made JLC BOMs list the 10 DNP parts as rows with a blank part number | confirmed | Keep them if the explicit population tracking is wanted, but budget for the manual unselect step; make the Footprint column consistent with the rest of the file. | [09](sections/09_erc_drc_fab_outputs.md) |
| FAB-18 | placement/silkscreen_pcb-top-pos.csv is a header-only file, and the whole placement/ folder is untracked in git | confirmed | Delete the top-side file or add a '# no top-side parts' note, and decide whether placement/ belongs in git or in .gitignore — untracked ordering files are not reproducib… | [09](sections/09_erc_drc_fab_outputs.md) |
| FAB-19 | PCBWay's BOM and PCBWay's placement file do not cover the same parts (162 vs 149) | confirmed | Say it explicitly in the PCBWay order notes and attach the assembly drawing, so the quote does not stall on a missing-placement query. | [09](sections/09_erc_drc_fab_outputs.md) |
| FAB-20 | The board's minimum-track-width constraint is set to 0.000 mm, so KiCad never checks track width | confirmed | Set the minimum track width to 0.15 mm in Board Setup so the check does something on the next edit. | [09](sections/09_erc_drc_fab_outputs.md) |
| FAB-V01 | 18 unfilled via-in-pad holes inside the exposed thermal pads of U4 and U11, with no plugged-via request anywhere in the ordering files | added-by-verifier | Accept for this prototype spin - the far-side tenting is the standard mitigation and neither part (ESP32-S3 module ground/thermal pad, TP4056 charger EP) depends on a pe… | [09](sections/09_erc_drc_fab_outputs.md) |
| HMI-05 | Two-button chords on ladder 1 are only 24-41 mV apart worst case | confirmed | Keep the single-press rule and make it explicit in the firmware-interface docs. Oversample at least 16 reads and use the eFuse ADC calibration. Only if chords are ever w… | [08](sections/08_buttons_rtc_touch_expansion.md) |
| HMI-06 | Only two of eight buttons produce a valid logic level for deep-sleep wake *(was MEDIUM)* | confirmed-with-corrections | Document that the ext1 deep-sleep wake list can only be IO1/IO4 low = RIGHT/DWN1, with SW10 on IO18 as the intended wake source. Configure IO1/IO4 as analogue (or apply … | [08](sections/08_buttons_rtc_touch_expansion.md) |
| HMI-08 | ESD/TVS ground pads connect to the pour through a single thermal spoke, two to isolated islands *(was MEDIUM)* | confirmed-with-corrections | Set the GND pads of U7/U8/U9/CR2/CR3/D3/D8 to solid zone connection (no thermal relief) and drop a stitching via within about 1 mm of each. Investigate the two 'isolated… | [08](sections/08_buttons_rtc_touch_expansion.md) |
| HMI-09 | GPIO46's ESD clamp is 25 mm away at the SD card, behind 93 mm of routed track *(was MEDIUM)* | confirmed-with-corrections | Accept for a prototype and note it. Next spin, put GPIO46's channel in a protector next to J6 - U9 pin 4 is already an unused channel, so a second small array near the h… | [08](sections/08_buttons_rtc_touch_expansion.md) |
| HMI-11 | D8 uses a project-local D_TVS_Dual_ACA whose pin 3 is common, unlike the stock KiCad symbol | confirmed | Rename the local symbol (e.g. to PESD2IVN-UX) so it can never be updated onto the wrong stock part, or switch D8 to Device:D_TVS_Dual_AAC which already has pin 3 = commo… | [08](sections/08_buttons_rtc_touch_expansion.md) |
| HMI-12 | J4 pin 2 has neither an ESD clamp nor any local decoupling capacitor | confirmed | Add 0.1 uF (and ideally 1 uF) from J4 pin 2 to GND within a few mm of the connector, and add a fifth ESD channel - a TPD1E10B06-class single would do - on pin 2. | [08](sections/08_buttons_rtc_touch_expansion.md) |
| HMI-13 | Front-mount solder-bridge tabs clear their rings by 0.152-0.195 mm against a 0.15 mm rule *(was MEDIUM)* | confirmed-with-corrections | Widen the gap to at least 0.25 mm and raise the tab-tip mask windows to 0.8 mm diameter so the dam stays at or above 0.2 mm; ask the fab to confirm it can hold a 0.26 mm… | [08](sections/08_buttons_rtc_touch_expansion.md) |
| HMI-14 | Front silkscreen names the wrong switches for the front-mount tabs *(was MEDIUM)* | confirmed-with-corrections | Reword to 'the four bottom-edge switches SW2, SW3, SW8 and SW9' and say what the tabs are actually for (bridging for a front-mounted APEM MJTP1243), since the present wo… | [08](sections/08_buttons_rtc_touch_expansion.md) |
| HMI-15 | Released-state ladder voltage saturates the ADC, so it cannot be used as a rail reference | confirmed | Accept for a prototype, but size the firmware's decision windows for +/-3% of full scale rather than for the nominal gaps, and do not attempt ratiometric self-calibratio… | [08](sections/08_buttons_rtc_touch_expansion.md) |
| HMI-16 | D3's clamping voltage exceeds the TPS923610's VOUT absolute maximum | confirmed | Accept for a prototype - for slow overvoltage the TVS holds 29-32 V, which is at the limit, and only a multi-amp strike reaches 42 V. For belt-and-braces, an SMAJ26CA-cl… | [08](sections/08_buttons_rtc_touch_expansion.md) |
| HMI-17 | MJTP1117 BOM rows pair an APEM MPN with a SHOU HAN LCSC code without saying so | confirmed | Add a Substitute/Notes BOM column naming TS365ZJ and SKHLLAA010 and marking them as alternates, so the row is self-explanatory without the prose. Confirm the TS365ZJ's a… | [08](sections/08_buttons_rtc_touch_expansion.md) |
| HMI-19 | DS3231M powers up with EN32KHZ set, above the quoted timekeeping current | confirmed | One line in the driver init: clear bit 3 of register 0x0F. Worth stating in the firmware-interface documentation since the sleep budget assumes 2-3 uA. | [08](sections/08_buttons_rtc_touch_expansion.md) |
| HMI-21 | J6 is a right-angle socket overhanging the top edge, with pin labels only on the opposite face | confirmed-with-corrections | Mirror a compact copy of the label onto B.Silkscreen, at minimum BAT+ at pin 12 plus the pin-1 marker, since that is the face you look at while plugging in. Tell the enc… | [08](sections/08_buttons_rtc_touch_expansion.md) |
| HMI-22 | README's optional expansion-header block omits the protection parts that exist only for J6 | confirmed-with-corrections | Change the row to 'J6, U8, CR2, CR3, D3, D8 (keep U9 - it also protects the SD card)' so a build-one configurator does not leave five orphan parts fitted. | [08](sections/08_buttons_rtc_touch_expansion.md) |
| HMI-23 | NextPCB substitute for J6 may be a male wafer, not a female socket | unverifiable | Verify the CJT part's gender before ordering from NextPCB. If it is male, either drop J6 from that build and hand-fit the Sullins part, or choose a right-angle 2x6 femal… | [08](sections/08_buttons_rtc_touch_expansion.md) |
| HMI-24 | DS3231MZ is the most expensive IC here but is wired to deliver only accuracy | confirmed | If +/-5 ppm is genuinely wanted, keep it and fix HMI-03/HMI-04 so the part earns its price. If the clock only has to be good between syncs, an RV-3028-C7 is cheaper, far… | [08](sections/08_buttons_rtc_touch_expansion.md) |
| HMI-V04 | J6 exposes 3V3 and the I2C bus with no series resistance or current limit, unlike the three GPIOs | added-by-verifier | Accept for this prototype. If the area is ever revised, put 33 ohm in series with SDA and SCL at the header to match what the GPIOs already get - it costs two 0603 parts… | [08](sections/08_buttons_rtc_touch_expansion.md) |
| HMI-V05 | The top three ladder-2 codes sit above 2.5 V, in the ESP32-S3 SAR's compressed region | added-by-verifier | Use the eFuse ADC calibration (esp_adc_cal / adc_cali on ESP-IDF) rather than raw codes, and oversample at least 16 reads, which HMI-05 already recommends for a differen… | [08](sections/08_buttons_rtc_touch_expansion.md) |
| HMI-V06 | The front silkscreen's actuator marks on the four bottom switches sit outside the switch body | added-by-verifier | Put the '^' on the actuator centreline (midway between the two contact pads) on all eight switches, or drop it and keep only the 'G' ground-pin marker, which is correctl… | [08](sections/08_buttons_rtc_touch_expansion.md) |
| LAY-03 | Metal screw/washer at H1 or H5 can short the LiPo rail to the GND mounting annulus *(was HIGH)* | confirmed-with-corrections | Move P+ away from H1 and B+ away from H5 to >= 3.5 mm, or place a 3.5 mm-radius copper keepout around every mounting hole. Until that is done, HARDWARE.md must state M2 … | [10](sections/10_layout_area_walk.md) |
| LAY-06 | 25 GND pads are starved thermals, including the USB-C ground pad, the charger, the LDO and the power-path mux *(was MEDIUM)* | confirmed-with-corrections | Set the pad-to-zone connection to solid for the power and thermal cases -- U11, U2, U3, U6, J1.A1, the three J7 ground pads, J2.17 and R37 at the boost -- and leave ther… | [10](sections/10_layout_area_walk.md) |
| LAY-07 | Front-button solder-bridge tabs sit 0.151-0.188 mm from their rings, not the documented 0.3 mm *(was MEDIUM)* | confirmed-with-corrections | Open the gaps to >= 0.30 mm of copper as the documentation already claims, keeping >= 0.25 mm of mask dam. Until then, inspect all eight tab gaps under magnification on … | [10](sections/10_layout_area_walk.md) |
| LAY-08 | LDO_IN reaches the front-light boost through 125.5 mOhm of 0.25 mm track, 56 mm of it on the top layer *(was MEDIUM)* | confirmed-with-corrections | Confirm with the LED reviewer that C12 (4.7 uF) is genuinely adjacent to U10 pin 1 rather than just nearby. Widening LDO_IN to 0.40 mm costs nothing and halves the drop … | [10](sections/10_layout_area_walk.md) |
| LAY-09 | One via on the board has no net assigned *(was MEDIUM)* | confirmed | Delete it, or assign it to GND if it was meant as a stitching via. It sits inside the pour so it is electrically harmless, but it is unexplained copper in an otherwise c… | [10](sections/10_layout_area_walk.md) |
| LAY-10 | Power rails are 0.25 mm where a 1 A charge current gives a 13.5 C rise; P+ has a 0.25 mm neck and B- has no vias *(was MEDIUM)* | confirmed-with-corrections | Widen VBUS_PRE_FUSE and USB_VBUS between J1, F1, U2 and U11 to 0.50 mm and the 3V3 trunk out of U3 to 0.40 mm. Remove the 0.78 mm 0.25 mm neck in P+. Add two vias on B- … | [10](sections/10_layout_area_walk.md) |
| LAY-11 | The small GND pour at the front-light boost has zero vias to the F.Cu plane *(was MEDIUM)* | confirmed | Put 2-3 GND vias inside that pour, immediately beside U10's GND pad and C9's ground pad, and make those two pad connections solid rather than thermal relief. | [10](sections/10_layout_area_walk.md) |
| LAY-12 | Silkscreen collisions: references printed over each other and over exposed pads, which mask-clipping will erase | confirmed | Nudge the R8/R27/R77/R78 references off their pads and separate R77 from C21. Combined with LAY-04 this is what decides whether an amateur can hand-populate 175 bottom-s… | [10](sections/10_layout_area_walk.md) |
| LAY-13 | The dashed cut-line textbox is mirrored on the front silk layer and overhangs the board edge by 3 mm | confirmed | Un-mirror the front-layer box and clip it and the J6 label table to the board outline. Purely cosmetic, but 32 of 94 DRC items are this class and they bury real warnings. | [10](sections/10_layout_area_walk.md) |
| LAY-14 | J6 pin-label table uses a 2.77 mm column pitch against the header's 2.54 mm pitch | confirmed | Re-space the table to 2.54 mm columns so each label centres over its own hole. Also consider a mirrored copy on B.Silkscreen, since J6 is a bottom-side socket and the on… | [10](sections/10_layout_area_walk.md) |
| LAY-15 | Eighteen footprint thermal vias use a 0.20 mm drill, the smallest holes on the board | confirmed | Confirm with the fab that 0.20 mm drills are included in the quoted price; if not, enlarge them to 0.30 mm -- there is room in both pads. | [10](sections/10_layout_area_walk.md) |
| LAY-16 | All 15 DRC clearance errors are inside the fixed USB-C footprint and are netclass noise | confirmed | Add a custom DRC rule scoped to J1 so the report goes to zero errors. With these removed the board has no clearance errors at all, which makes the next review far easier. | [10](sections/10_layout_area_walk.md) |
| LAY-17 | Four mechanical overhangs and one recess the enclosure must accommodate | confirmed | Check all four against the enclosure CAD before cutting a case. The U4 overhang in particular needs a pocket in any wall that follows the board outline, and the recessed… | [10](sections/10_layout_area_walk.md) |
| LAY-V01 | The tongue's 120.2 mm2 B.Cu ground island has zero stitching vias - it is the worst case, not the button strip | added-by-verifier | When adding the LAY-05 stitching vias, put one or two on the tongue as well - e.g. beside J6 pins 1 and 4 - and one in the 21 mm2 island near SW10. If the tongue is ever… | [10](sections/10_layout_area_walk.md) |
| LAY-V02 | The charger is programmed for about 255 mA, not the 1 A the layout analysis assumed throughout | added-by-verifier | Confirm 255 mA is intentional - it is a sensible choice for a small cell and keeps TP4056 self-heating low - and note it in HARDWARE.md, because it also sets the charge … | [10](sections/10_layout_area_walk.md) |
| LED-03 | LED+ on expansion header J6 is a low-impedance path to the battery rail; a short to ground destroys L2 *(was MEDIUM)* | confirmed-with-corrections | Accept for the prototype but document that LED+ is not a safe-to-probe logic pin (it reads ~3-4.5 V when the light is off, which invites exactly that mistake). On a resp… | [07](sections/07_led_frontlight_driver.md) |
| LED-04 | 24.5 V driver leaves only ~2 V of OVP headroom for the 22 V string the silkscreen invites *(was MEDIUM)* | confirmed-with-corrections | Lower the silkscreen and documentation ceiling to 20 V, which still covers a 7-die white string with margin. Note that fitting the pin-identical TPS923611DRLR (30 V, sam… | [07](sections/07_led_frontlight_driver.md) |
| LED-05 | C9 effective capacitance at operating bias sits close to TI's 1 uF minimum for loop stability | confirmed | Pull the Samsung DC-bias curve for CL21A475KBQNNNE, or measure C9 in circuit at operating bias. If it comes out below ~1.2 uF, move to a 1206 4.7 uF/50 V or add a second… | [07](sections/07_led_frontlight_driver.md) |
| LED-06 | LED_MONIT presents 107 kOhm to the ESP32 SAR ADC, ~10x the recommended source impedance | confirmed | It works as drawn. Firmware must wait >=50 ms after any brightness or colour change before trusting a LED_MONIT reading, and should expect a small DC offset. If monitor … | [07](sections/07_led_frontlight_driver.md) |
| LED-08 | Three KiCad DRC clearance errors at J3 are netclass artefacts, not real spacing problems | confirmed | Add a DRC rule exception for the connector's own pads, or take J3's pads out of the 'SW' netclass, so the released design has a genuinely empty error list. No copper cha… | [07](sections/07_led_frontlight_driver.md) |
| LED-09 | lib_symbol_mismatch ERC warnings on U10 and J3 - cached schematic symbols differ from their libraries | confirmed | Re-sync or update the library symbols so the cached and library copies match, before anyone runs an update-from-library on this schematic. | [07](sections/07_led_frontlight_driver.md) |
| LED-10 | Starved thermal relief on the GND pads of R37, R41 and R50 (one spoke instead of two) | confirmed | Negligible electrically; fix on R37 alone if you touch the layout, purely for mechanical and thermal robustness of the sense return. Leave R41/R50 as-is. | [07](sections/07_led_frontlight_driver.md) |
| LED-13 | TP3 puts up to 25 V on an exposed top-side pad in the visible decorative area | confirmed | 25 V is harmless to touch (SELV), so this is only about accidental shorts. Confirm that nothing conductive in the display stack-up or the enclosure lands on TP3. If in d… | [07](sections/07_led_frontlight_driver.md) |
| LED-V01 | D3 (SMAJ26A) clamps at 42.1 V, above U10's 32 V VOUT absolute maximum - the TVS guarding the exposed LED+ pin cannot keep the driver inside its ratings during a real surge | added-by-verifier | Accept for the prototype - the series trace resistance is doing real work here. If J6 is ever exposed in a finished product, put a few ohms or a ferrite in the LED+ tap … | [07](sections/07_led_frontlight_driver.md) |
| LED-V03 | The 13.33 mA set point holds only at 100 % duty - reference tolerance widens to -28 %/+26 % at 10 % duty, so dim settings are far less accurate than the headline number | added-by-verifier | Write the current as '13.3 mA at 100 % duty' wherever it appears. Expect a non-linear, unit-to-unit-varying brightness curve at the bottom of the dimming range and calib… | [07](sections/07_led_frontlight_driver.md) |
| LED-V04 | COLOR_SEL and PWM_LED occupy two of the four ESP32-S3 JTAG pins, so an external JTAG probe and a working front light are mutually exclusive | added-by-verifier | Document 'no external JTAG probe while the front light is connected - use the built-in USB-Serial-JTAG' in docs/HARDWARE.md. Nothing to change on the board. | [07](sections/07_led_frontlight_driver.md) |
| LED-V05 | The two most likely accidental shorts on J6 destroy R37 (the current-sense resistor), not L2 - and both fault pins are nearest neighbours of LED+ | added-by-verifier | Same control as LED-03: document J6 as unfused and not probe-safe, and note specifically that LED+ sits next to both cathode pins. On a respin, a few ohms in series with… | [07](sections/07_led_frontlight_driver.md) |
| MCU-03 | DS3231 INT/SQW is a no-connect — the external RTC cannot wake the MCU | confirmed | Accept — the designer has documented this as a knowing trade-off. If a scheduled wake from the precision RTC is ever wanted, route INT/SQW to a free RTC-capable GPIO (GP… | [04](sections/04_esp32_core_gpio_map.md) |
| MCU-04 | All three spare GPIOs on the expansion header are strapping pins; GPIO3 has no pull at all *(was MEDIUM)* | confirmed-with-corrections | Fit a 100 kOhm pull-down on GPIO3 (or enable an internal pull-down in firmware at start-up), and label J6 pins 2/3/9 as strapping pins in the documentation — 'must be lo… | [04](sections/04_esp32_core_gpio_map.md) |
| MCU-05 | Touch interrupt is on GPIO41, which is not RTC-capable, so touch cannot wake from deep sleep | confirmed | Accept — the power button on GPIO18 is the wake source and it is correctly RTC-capable. A future spin could swap TP_INT (GPIO41) and TP_RST (GPIO11) at zero cost, since … | [04](sections/04_esp32_core_gpio_map.md) |
| MCU-06 | SD power gate gets a 60 us on-pulse at power-up, and the net name implies the wrong polarity | confirmed-with-corrections | Accept the glitch — 60 us is far too short for a card to start, and inrush is limited by C36 0.1 uF / C37 1 uF. Consider renaming the net SD_PWR_N so nobody drives it th… | [04](sections/04_esp32_core_gpio_map.md) |
| MCU-07 | All four JTAG pins reused for board functions — no hardware JTAG probe possible | confirmed | Accept. The USB-Serial/JTAG controller on GPIO19/20 gives JTAG debugging over the USB-C connector instead, which is why the datasheet calls GPIO19/20 the way to 'free th… | [04](sections/04_esp32_core_gpio_map.md) |
| MCU-08 | Front-light enable/PWM line is held off only by the driver's 600 kOhm internal pull-down while the MCU is in reset | confirmed | Optional robustness add: a 100 kOhm 0603 pull-down on PWM_LED placed near U10 gives a hard-defined off state at negligible cost in drive current. | [04](sections/04_esp32_core_gpio_map.md) |
| MCU-09 | I2C bus is 184 mm / 179 mm of 0.2 mm track with 5-6 vias each | confirmed | Keep for this spin — it works electrically. Treat as CERT-LATER if EMC certification is later pursued. | [04](sections/04_esp32_core_gpio_map.md) |
| MCU-10 | UART test points TP1/TP2 have no ground pad next to them | confirmed | Add a third 1 mm GND pad beside TP1/TP2 in a future spin so a 3-wire USB-serial lead can be clipped on in one go. | [04](sections/04_esp32_core_gpio_map.md) |
| MCU-11 | U4 silkscreen outline is clipped by the antenna notch | confirmed | Cosmetic. Trim U4's silkscreen rectangle to the board outline so the fab does not clip it arbitrarily. | [04](sections/04_esp32_core_gpio_map.md) |
| MCU-15 | No ground stitching vias anywhere near the antenna cut-out or around the module *(was MEDIUM)* | confirmed-with-corrections | Add a row of GND stitching vias at roughly 2-3 mm pitch along the notch edge at x ~51-52 mm (y 93-112), plus a ring around the module's three pad rows. It costs nothing … | [04](sections/04_esp32_core_gpio_map.md) |
| MCU-16 | The 0.1 uF decoupling cap is farther from the module supply pin than the 22 uF bulk cap | confirmed | Swap the C32 and C33 positions in a future spin. Low impact: the WROOM-1 carries its own on-module decoupling, and 6.3 mm of 0.25 mm track is only a few nH. | [04](sections/04_esp32_core_gpio_map.md) |
| MCU-17 | 3V3 feed to the module is 0.25 mm wide, well under Espressif's 25 mil guidance | confirmed-with-corrections | Accept for the prototype — the numbers say it is fine. Widen to 0.5 mm or more in a future spin, which also helps EMC. | [04](sections/04_esp32_core_gpio_map.md) |
| MCU-18 | Unused octal-PSRAM pads sit directly between GPIO0 and I2C_SDA on the same pad row | confirmed | Inspect those five joints under magnification after reflow or hand-soldering. Worth one line in the assembly notes. (Note also that docs/HARDWARE.md's phrasing 'IO35-37 … | [04](sections/04_esp32_core_gpio_map.md) |
| MCU-V01 | Nothing tells a hand-assembler that the module's centre ground pad (EPAD, pin 41) is optional to solder | added-by-verifier | Add one line to the assembly notes: U4 centre pad is optional - edge pads only is fine for hand assembly; if pasting it, use a sparse paste pattern. No board change. | [04](sections/04_esp32_core_gpio_map.md) |
| MEC-08 | Button plunger protrusion is inconsistent between groups — bottom row +1.95 mm, side buttons +0.95 to +1.21 mm *(was MEDIUM)* | confirmed | Re-centre the four bottom switches about 0.95 mm inboard so all ten MJTP1117s protrude by the same amount; also level SW10 with SW1/SW4. Otherwise the case needs two or … | [11](sections/11_mechanical_enclosure_assembly.md) |
| MEC-10 | The bottom bezel is a 5.75 mm wide, 47 mm long bridge carrying four through-hole buttons *(was MEDIUM)* | confirmed-with-corrections | Keep H3/H4 where they are — they brace both ends and are symmetric about the board centre to 0.000 mm. Add a build-guide warning not to flex this strip. If the slot is w… | [11](sections/11_mechanical_enclosure_assembly.md) |
| MEC-11 | Optional front-mounted MJTP1243 buttons overlap the panel's footprint by 0.30 mm and need 4.3 mm of front cavity *(was MEDIUM)* | confirmed-with-corrections | Add the 0.30 mm interference and the 4.3 mm front-cavity requirement to HARDWARE.md §9.1.1. A 0.5 mm relief in the case's bottom bezel edge, or shifting the panel 0.5 mm… | [11](sections/11_mechanical_enclosure_assembly.md) |
| MEC-12 | J6 is a right-angle socket whose mouth faces out of the top edge and whose body overhangs it by 1.69 mm — undocumented | confirmed | State the orientation and the 1.69 mm overhang in HARDWARE.md §11 and in the enclosure section. The case needs an aperture in its top wall, roughly x 87.2…103.0, or the … | [11](sections/11_mechanical_enclosure_assembly.md) |
| MEC-13 | No mechanical bootloader entry and no reachable reset with the case closed; only the BOOT half is documented | confirmed | Either fix MEC-09 so RESET is reachable, or add one sentence to README.md applying the same USB-Serial-JTAG argument to reset, so a user who bricks firmware knows what t… | [11](sections/11_mechanical_enclosure_assembly.md) |
| MEC-14 | The right board edge is unsupported for 73.25 mm between H5 and H4 while carrying four buttons, the USB port and the status LED | confirmed | Add a sixth M2 hole near (x 101, y 96–100) if a clear spot exists, or have the case press a rib on the board's top face there. At minimum, make the case's USB aperture b… | [11](sections/11_mechanical_enclosure_assembly.md) |
| MEC-15 | microSD card exits toward the left wall from a mouth 11.89 mm inside the edge; socket fit is still an open item | confirmed | Settle the TF-PUSH vs MEM2075 question first, then dimension the case aperture and a finger relief at x = 44.24, y ≈ 84.6 from whichever part is chosen. Do not freeze th… | [11](sections/11_mechanical_enclosure_assembly.md) |
| MEC-16 | The spare front-light output pads TP3/TP4/TP5 are through-holes sitting under the display panel *(was MEDIUM)* | confirmed | Move these three pads into the 5.75 mm bezel strip (y > 142.5) or onto the back face next spin, since their whole purpose is post-cut rework. For this build, document th… | [11](sections/11_mechanical_enclosure_assembly.md) |
| MEC-17 | Flex tail slack is only 2.5–4.1 mm and the panel tail length could not be verified from a printed dimension | unverifiable | Measure a physical panel's tail before the case's slot position is frozen, and record the measurement in HARDWARE.md. State explicitly that the panel's glass edge must s… | [11](sections/11_mechanical_enclosure_assembly.md) |
| MEC-18 | Four different corner radii on the outline | confirmed-with-corrections | Harmonise to a single radius, 1.5 mm or 2.0 mm, next spin. Purely cosmetic and ergonomic; no electrical effect. | [11](sections/11_mechanical_enclosure_assembly.md) |
| MEC-19 | Status LED D2 is on the back face 0.59 mm from the right edge — it lights the inside of the case and will glow through the seam | confirmed | Provide a light pipe or window at (102.80, 118.34) in the back wall plus a light-block skirt around it. If MEC-09 is fixed by moving SW11 outward, move D2 at the same ti… | [11](sections/11_mechanical_enclosure_assembly.md) |
| MEC-20 | H2 and H5 are 1.500 mm out of level, so the upper boss pair is skewed | confirmed | Level H2 and H5 to a common y next spin. It costs nothing in layout and makes a moulded or 3D-printed boss pattern simpler and easier to get square. | [11](sections/11_mechanical_enclosure_assembly.md) |
| PWR-02 | Coincident Wi-Fi TX + SD write + e-paper refresh (~515 mA) sits only ~8% under the LDO's 560 mA minimum, foldback current limit *(was MEDIUM)* | confirmed-with-corrections | Serialise in firmware: never transmit during an SD write or an e-paper refresh; stagger them. Write that as an explicit hardware constraint into HARDWARE.md section 3.5 … | [03](sections/03_ldo_power_tree_sleep_budget.md) |
| PWR-03 | Deep-sleep budget is ~73 uA typical; ~21 uA is recoverable with four resistor value changes *(was MEDIUM)* | confirmed-with-corrections | Scale R70/R17 by x10 (1M/1.5M, same ratio and same ADC reading, 13.2 -> 1.3 uA) and raise C23 from 2.2 nF to ~22 nF to keep the node stiff for the ADC sampling cap; scal… | [03](sections/03_ldo_power_tree_sleep_budget.md) |
| PWR-04 | Wi-Fi TX drops 3V3 below the ESP32-S3's 3.0 V minimum at ~3.2-3.3 V of cell; the default brown-out detector can never fire *(was MEDIUM)* | confirmed-with-corrections | Raise CONFIG_ESP_BROWNOUT_DET_LVL_SEL to level 3 (2.98 V) or level 4 (2.84 V) so the chip shuts down cleanly instead of being cut off abruptly. Gate Wi-Fi on BAT_MONIT >… | [03](sections/03_ldo_power_tree_sleep_budget.md) |
| PWR-05 | U3's GND pad (and C21's) reaches the ground pour through a single thermal spoke *(was MEDIUM)* | confirmed-with-corrections | Set the pad-to-zone connection for U3 pin 2 and C21 pin 2 to solid fill, or move the neighbouring tracks so the pour can form all four spokes. Costs nothing and fixes an… | [03](sections/03_ldo_power_tree_sleep_budget.md) |
| PWR-06 | USB_VBUS has no bleeder and can be floated up by leakage into the unpowered TP4056 status pins, and it drives the mux's MODE pin *(was MEDIUM)* | confirmed-with-corrections | Add a 100 kOhm bleeder from USB_VBUS to GND - a fraction of a cent removes the whole question. On the prototype, measure USB_VBUS and USB_STAT on battery with no cable a… | [03](sections/03_ldo_power_tree_sleep_budget.md) |
| PWR-09 | The 0.1 uF module decoupling cap is further from the ESP32's 3V3 pad than the 22 uF bulk cap | confirmed | Swap the positions of C32 and C33 in the next revision so C33 (0.1 uF) is nearest U4 pin 2. No effect on this prototype's function - fix it opportunistically. | [03](sections/03_ldo_power_tree_sleep_budget.md) |
| PWR-10 | 3V3 is 0.25 mm everywhere including the long trunk from the LDO to the module, costing ~40 mV at peak load | confirmed | Widen the U3 -> module segment of 3V3 to 0.5 mm in the next revision. Purely a voltage-drop improvement, worth ~20 mV of extra battery window at high load. I estimated t… | [03](sections/03_ldo_power_tree_sleep_budget.md) |
| PWR-11 | USB_VBUS is narrower (0.25 mm) than the battery path it parallels (0.4 mm) despite carrying charger plus system current | confirmed | Widen USB_VBUS and VBUS_PRE_FUSE to 0.4 mm to match the battery path. Not a functional problem for the prototype. | [03](sections/03_ldo_power_tree_sleep_budget.md) |
| PWR-18 | HARDWARE.md's USB_STAT ladder assumes the TP4056 status pins are true high-Z with VCC at 0 V - unverified *(was DOC)* | unverifiable | Before fixing the firmware's ADC thresholds, measure USB_STAT and USB_VBUS on battery with no cable attached. Adding the 100 kOhm bleeder of PWR-06 makes the documented … | [03](sections/03_ldo_power_tree_sleep_budget.md) |
| PWR-V01 | The Q3 -> R27 -> Q8 link in the battery path was left at 0.25 mm when the rest of the path was widened to 0.4 mm | added-by-verifier | Widen both nets to >=0.4 mm (they are 3-7 mm long, 0.6-0.8 mm costs nothing) next time the board is open. Not worth a re-spin on its own. | [03](sections/03_ldo_power_tree_sleep_budget.md) |
| PWR-V02 | TP4056 CE pin is driven hard to 3V3 (no series resistor) while the charger's VCC is 0 V on battery - the stiff, unexamined back-feed path in the sleep budget | added-by-verifier | Bring-up check, battery only, no cable: USB_VBUS must read ~0 V and D2 must be dark; then measure total cell current in deep sleep against the ~73 uA budget. This single… | [03](sections/03_ldo_power_tree_sleep_budget.md) |
| SD-03 | Dual-source footprint leaves four unused shell ground lands with solder-paste apertures whichever socket is fitted *(was MEDIUM)* | confirmed-with-corrections | For reflow assembly, have the stencil house delete the paste apertures belonging to the socket you are NOT fitting, or hand-solder J7 after reflow. At minimum add an ass… | [05](sections/05_sdmmc_microsd.md) |
| SD-06 | Card-detect is discarded: the socket's detect terminal is tied to GND with the shell *(was MEDIUM)* | confirmed-with-corrections | Accept for the prototype and poll by attempting to mount. On a respin, use a 10-pin socket symbol, route the Cd land to a spare GPIO with a 10k pull-up to 3V3 (not to SD… | [05](sections/05_sdmmc_microsd.md) |
| SD-07 | The tight locating slot is only 0.05 mm wider than the TF PUSH's recommended peg hole and sits at the minimum routed-slot width | confirmed | Widen slot B to about 1.25 x 1.6 mm and push slot A's high-x edge out by 0.1 mm. Costs nothing, keeps both parts seating, and removes the fab-tolerance risk. Nothing ele… | [05](sections/05_sdmmc_microsd.md) |
| SD-08 | The GCT body keep-out is drawn as a rule area on the F.SilkS layer, so it enforces nothing | confirmed | Redraw the rule area on B.Cu (or both copper layers) if you want DRC to police it. As routed today nothing violates it, so this is cleanup rather than a risk - but it al… | [05](sections/05_sdmmc_microsd.md) |
| SD-09 | J7's ground and shield pads reach the GND zone through a single thermal spoke | confirmed-with-corrections | Set the zone connection for J7's GND/shield pads and C37.1 to solid fill. Cheap, silences four DRC warnings, and lowers the inductance of the shield's ESD return path, w… | [05](sections/05_sdmmc_microsd.md) |
| SD-10 | A clean SD power-cycle needs about 0.4 s if the bus is left high-impedance | confirmed-with-corrections | Document the required off-time: >= 500 ms if the pins are parked high-impedance, or >= 20 ms using the drive-low approach the schematic already mandates. If you want har… | [05](sections/05_sdmmc_microsd.md) |
| SD-11 | Local SD_VDD bulk is 1.1 uF, below the ~10 uF typically shown in SD host reference designs | confirmed | Leave as is. If card writes prove flaky on the prototype, change C37 from 1 uF to 10 uF - same 0603 land, zero layout change. Listed only so the option is on record with… | [05](sections/05_sdmmc_microsd.md) |
| SD-12 | Q7's symbol, description and datasheet field are the IRLML6402's, not the AO3401A's | confirmed-with-corrections | Correct the Description and Datasheet fields to the AO3401A. Both parts would work in this circuit, so nothing is at risk now - but the wrong abs-max numbers will mislea… | [05](sections/05_sdmmc_microsd.md) |
| SD-13 | The SDMMC schematic block shows ESD protection for only four of the six bus lines | confirmed | Add a text note in the SDMMC block along the lines of "DAT0/DAT1 clamped by U9, see <block name>", or move U9's two SD channels onto this sheet. Purely a readability fix. | [05](sections/05_sdmmc_microsd.md) |
| SD-15 | IO10 has a documented 60 us low-level power-up glitch that briefly switches the card on at every cold boot, contradicting HARDWARE.md | confirmed-with-corrections | Harmless in itself, but firmware must not assume the card was continuously unpowered after a cold boot: perform one deliberate power-cycle with the off-time from SD-10 b… | [05](sections/05_sdmmc_microsd.md) |
| SD-16 | SD_CMD and SD_DAT3 occupy GPIO15/GPIO16, the ESP32-S3's only 32.768 kHz crystal pins | confirmed | Informational - the board already has an I2C RTC, so this is probably a non-issue. But record it: this board can never gain an external 32 kHz crystal for accurate deep-… | [05](sections/05_sdmmc_microsd.md) |
| SD-V04 | U9's ground pad reaches the GND zone through a single thermal spoke - the ESD array's own discharge return | added-by-verifier | Set the zone connection for U9 pad 2 (and J7 pads 6/9 and C37 pad 1) to solid fill rather than thermal relief. Costs nothing, silences five DRC warnings, and is the chea… | [05](sections/05_sdmmc_microsd.md) |
| USB-07 | U6 ESD array hangs off a ~9.6 mm stub from the connector instead of sitting on the data line | confirmed | Move U6 so D+/D- pass through it on the way from J1 to the ESP32. Purely an ESD-robustness improvement - it cannot affect USB full-speed signalling. | [01](sections/01_usb_input_power_path.md) |
| USB-08 | Status ladder draws 13.2 uA continuously from 3V3 on battery, comparable to the MCU's whole deep-sleep budget | confirmed-with-corrections | Scale the whole network up 4x (R70 470k, R17 680k, R67 240k, R71 100k) for about 3 uA, keeping all the ratios and therefore all the state voltages identical. Pair this w… | [01](sections/01_usb_input_power_path.md) |
| USB-09 | CR1 sits on the cable side of F1, so a shorted TVS is not current-limited by the fuse | confirmed | Move CR1 to the USB_VBUS side of F1 if the layout is touched anyway. Cleanup only - a shorted TVS would simply trip the host port. | [01](sections/01_usb_input_power_path.md) |
| USB-10 | Sixteen J1 DRC clearance errors are footprint-inherent 0.15 mm pad gaps flagged against a 0.20 mm netclass rule | confirmed | Add a DRC exclusion or a custom rule scoped to J1 so that the real DRC output stays readable. The board is manufacturable exactly as released. | [01](sections/01_usb_input_power_path.md) |
| USB-11 | J1 silkscreen is clipped by the board edge and the connector body overhangs the outline by 1.72 mm | confirmed | The silk clipping is cosmetic. The 1.72 mm overhang is correct for an edge-mount receptacle but the enclosure aperture must be dimensioned for it - pass to whoever does … | [01](sections/01_usb_input_power_path.md) |
| USB-20 | C23 is 2.2 nF but the ESP32-S3's published ADC accuracy is specified with 100 nF on the input *(was MEDIUM)* | confirmed-with-corrections | Change C23 from 2.2 nF to 100 nF. Same 0603 footprint, same placement, about one cent. RC rises from 132 us to 6 ms, which is irrelevant for a status read. This is the p… | [01](sections/01_usb_input_power_path.md) |
| USB-V03 | F1's MPN and LCSC fields name two different manufacturers' parts | added-by-verifier | Decide which part is actually being ordered and make the two fields agree. Per this repo's convention the DigiKey/MPN side is primary, so correct the LCSC field to C8027… | [01](sections/01_usb_input_power_path.md) |
| USB-V04 | TPS2116 recommends ~100 uF on VOUT where reverse-current blocking is expected; the board has 26.7 uF and enters RCB on every unplug | added-by-verifier | No change for the prototype - the quantitative margin is large. Add it to the first-article scope list: watch LDO_IN at U2's VOUT pin during unplug and on the USB->batte… | [01](sections/01_usb_input_power_path.md) |

## DOC (37)

| ID | Finding | Verdict | Recommendation | Section |
|---|---|---|---|---|
| BAT-12 | Schematic note on D2 contradicts its own arithmetic, and D2 is a USB indicator inside a block titled 'Battery Charger' | confirmed | Change the note to '~1.6 mA, USB-present indicator'. Consider moving D2/R59 into the USB block or silkscreening it 'PWR' so nobody expects it to blink while charging. | [02](sections/02_battery_charger_protection.md) |
| BAT-13 | HARDWARE.md documents a 'No battery fitted (blinks)' USB_STAT state that the Fix-4 CE gate makes unreachable | confirmed-with-corrections | Delete or re-label that ladder row: with Fix 4, 'no battery' is indistinguishable from 'idle' on USB_STAT. Firmware must detect a missing cell from BAT_MONIT instead (it… | [02](sections/02_battery_charger_protection.md) |
| BAT-14 | HARDWARE.md says over-current opens both protection FETs; the DW01A opens only the discharge FET | confirmed | Correct the row to 'over-current -> discharge FET only (OD)' and add a separate row for the short-circuit threshold with its own delay. | [02](sections/02_battery_charger_protection.md) |
| BAT-15 | HARDWARE.md understates the residual drain that survives an over-discharge cutoff (~4 uA quoted, ~8 uA of resistors actual) | confirmed | Update the figure to '~8 uA of divider current, ~10 uA total, from R56/R57 and R79/R80' so the storage-life claim rests on the right number. | [02](sections/02_battery_charger_protection.md) |
| BAT-V03 | Manufacturer/datasheet fields for U5 and Q1 do not match the parts their LCSC codes deliver | added-by-verifier | Make Manufacturer and Datasheet fields agree with the LCSC code actually ordered (or change the code). Keep the TECH PUBLIC datasheet as the pinout reference for Q1 - Fo… | [02](sections/02_battery_charger_protection.md) |
| DOCS-20 | The board silkscreen documents a board-shortening modification that no document mentions and that contradicts the BOM's DNP guidance | not-verified | Either document the short-board variant properly in the configurations table (cut line, which displays it suits, the full population delta), or remove the instruction fr… | [13](sections/13_docs_end_user_readability.md) |
| DOCS-21 | The display part number is written three different ways across the repo and the board | not-verified | Normalise every occurrence to GDEQ0426T82 and to the exact suffixes -T01C / -FL01C / -FT01C. A reader searching the wrong string finds no product page. | [13](sections/13_docs_end_user_readability.md) |
| DOCS-22 | fabrication/README.md's release-record table cites dates and a file that do not match the repository | not-verified | Refresh the dates to the current commit, and mark the .xls row "local only, not in the repository" to match README.md:125. | [13](sections/13_docs_end_user_readability.md) |
| EPD-12 | Silkscreen clipped on J2's outline, and the key build warning sits where the FPC will cover it | confirmed | Cosmetic only. If the silk is revised, move the warning text outside the FPC corridor (x < 60 or x > 82) so it stays readable after assembly, and trim the J2 outline seg… | [06](sections/06_eink_driver_connector.md) |
| EPD-V02 | Q4 and D4-D6 still carry the library symbols' Description/Datasheet fields, which describe different parts (BSS138 50 V; MBR0520 30 V/0.5 A) | added-by-verifier | Overwrite the Description and Datasheet fields on Q4, D4, D5, D6 with the fitted parts' data (schematic-only field edit, no netlist change). | [06](sections/06_eink_driver_connector.md) |
| LAY-D1 | HARDWARE.md 9.1.1 states the front-button solder tabs stop 0.3 mm short; the real gap is 0.151-0.188 mm | confirmed | Either open the gaps to 0.30 mm so the design matches the documentation, or correct the figure in HARDWARE.md and add the pre-power-up inspection step. | [10](sections/10_layout_area_walk.md) |
| LAY-D2 | HARDWARE.md 6.2 claims the EPD boost loop is ~33 mm2; every measurement I can make gives 24-27 mm2 | confirmed | I could not verify the 33 mm2 figure and do not know which pads it uses. Either the doc is stale or it measures a polygon I have not guessed -- worth reconciling, since … | [10](sections/10_layout_area_walk.md) |
| LAY-D3 | HARDWARE.md 16 warns about a conductive case bridging HV nets but not about a screw shorting the battery at H1/H5 | confirmed-with-corrections | Add a named screw and washer specification (M2, no washer, nylon preferred) to 16, alongside fixing the layout per LAY-03. | [10](sections/10_layout_area_walk.md) |
| LAY-D4 | HARDWARE.md calls the bottom-centre button CONFIRM; the board silk prints OK | confirmed | Pick one name and use it in both the documentation and the silkscreen. | [10](sections/10_layout_area_walk.md) |
| LAY-D5 | HARDWARE.md never states the board dimensions, stackup or any of the outline features | confirmed | Add a short mechanical section: 60.05 x 111.30 mm, 2 layers, 1.6 mm, 1 oz, 0.15 mm min clearance / 0.20 mm min track, and a dimensioned sketch of the four outline featur… | [10](sections/10_layout_area_walk.md) |
| LAY-D6 | The tongue-removal procedure exists only on unprintable silkscreen, not in HARDWARE.md | confirmed | Move this procedure into HARDWARE.md (a new subsection under 9.2 or 11) and enlarge the silk note to a printable size. | [10](sections/10_layout_area_walk.md) |
| LED-07 | Three different LED currents stated in three places; only docs/HARDWARE.md is correct | confirmed-with-corrections | Change the schematic note and the silkscreen to 13.3 mA. If the silk's '15 mA' was meant as 'your LEDs must be rated for at least 15 mA', say that explicitly - as curren… | [07](sections/07_led_frontlight_driver.md) |
| LED-15 | The LTspice file in simulations/led_driver models a superseded discrete boost, not the TPS923610 as built | confirmed-with-corrections | Either retire the file or add a header comment stating that it models a superseded discrete concept, so nobody validates the shipped driver against it. (Its 'N=7' LED st… | [07](sections/07_led_frontlight_driver.md) |
| MCU-19 | Documentation states three times that IO46 is input-only; on the ESP32-S3 it is a full bidirectional I/O | confirmed | Correct the claim in all three places. It matters practically: a user building an add-on for J6 is being told they cannot drive pin 2 as an output, when they can (subjec… | [04](sections/04_esp32_core_gpio_map.md) |
| MCU-20 | Documentation calls R72 a 0 ohm jumper; it is 10 kOhm | confirmed | Reword to 'R73/R74 are 0 ohm jumpers; R72 is a 10 kOhm link'. | [04](sections/04_esp32_core_gpio_map.md) |
| MCU-21 | Neither document mentions the PCB antenna, the outline notch that serves it, or the keep-out an enclosure must respect | confirmed | Add a short subsection to HARDWARE.md: where the antenna is, that the 6.35 x 18.7 mm notch must stay empty, and Espressif's 15 mm enclosure-clearance recommendation. Thi… | [04](sections/04_esp32_core_gpio_map.md) |
| MCU-22 | README calls SW10 a power switch; HARDWARE.md correctly calls it a wake input | confirmed | Use 'power/wake button' consistently. A reader who believes SW10 is a power switch will expect zero draw when the device is 'off', and will misdiagnose the deep-sleep cu… | [04](sections/04_esp32_core_gpio_map.md) |
| MEC-21 | The enclosure section of HARDWARE.md contains none of the dimensions a case designer needs | confirmed | Paste the 'Enclosure designer's cheat-sheet' table from this section into HARDWARE.md §16, and soften the two overstated claims. A board whose selling point is being cas… | [11](sections/11_mechanical_enclosure_assembly.md) |
| MEC-22 | Nearly all front silkscreen is under the panel, and the J6 pinout label also runs 5.46 mm off the board | confirmed | Move anything meant to be read to the back face or into the 5.75 mm bezel strip. Pull the J6 pinout label fully on-board and put it on B.Silkscreen where it can actually… | [11](sections/11_mechanical_enclosure_assembly.md) |
| PWR-14 | README calls C12 the 'LDO-input capacitor'; it is the LED boost's input capacitor | confirmed-with-corrections | Change the README Core row to 'C4 (LDO-input capacitor)' and either move C12 into the Frontlight group or relabel it 'C12 (LED-boost input capacitor, also bulk on LDO_IN… | [03](sections/03_ldo_power_tree_sleep_budget.md) |
| PWR-15 | HARDWARE.md points the thermal qualification at the battery case; the worst case is USB | confirmed | Re-point that blockquote and the thermocouple plan at the USB case, and state the ~250 mA continuous USB ceiling explicitly next to the part's '500 mA' headline. | [03](sections/03_ldo_power_tree_sleep_budget.md) |
| PWR-16 | HARDWARE.md claims bulk capacitance can ride out a Wi-Fi TX pulse; it holds for microseconds | confirmed | Delete that clause. The other half of the same blockquote - that firmware treats voltages near 3.3 V as 0% and shuts down before this region - is the argument that actua… | [03](sections/03_ldo_power_tree_sleep_budget.md) |
| PWR-17 | HARDWARE.md understates the battery-gauge load offset by roughly 2x | confirmed-with-corrections | Restate as ~140-200 mV at 500 mA, or measure it on the prototype by comparing the ADC reading at idle against the same cell under a known load. The accompanying advice (… | [03](sections/03_ldo_power_tree_sleep_budget.md) |
| PWR-19 | HARDWARE.md's SD rule covers the power-off transition only and does not mention light sleep | confirmed-with-corrections | Extend the rule in section 5 to: 'for the whole time SD_ACTIVATE is de-asserted, SD_CLK/CMD/DAT0-3 must be input-with-no-pull or driven low - and therefore light sleep m… | [03](sections/03_ldo_power_tree_sleep_budget.md) |
| SD-V03 | Neither HARDWARE.md nor README.md connects the battery cut-out to the card slot | added-by-verifier | Add one paragraph to HARDWARE.md section 5 stating the socket's mouth faces the battery cut-out, giving the clear-channel dimensions a cell must respect (x 56.15-73.45 k… | [05](sections/05_sdmmc_microsd.md) |
| USB-14 | Schematic still declares the "> 3.10 V" idle window that HARDWARE.md §3.7 explicitly warns against | confirmed | Update the schematic note to "> 2.6 V" so schematic, documentation and firmware agree. Documentation half of USB-01. | [01](sections/01_usb_input_power_path.md) |
| USB-15 | HARDWARE.md calls J1 a 14-pin receptacle; the ordered GCT USB4085-GF-A has 16 contacts | confirmed | Reword as "16-position connector, 14 nets used (SBU1/SBU2 unconnected)" so nobody counting holes on the fab drawing thinks a part was substituted. | [01](sections/01_usb_input_power_path.md) |
| USB-16 | HARDWARE.md attributes hot-plug damping advice to "TI's own TP4056 datasheet"; the TP4056 is not a TI part | confirmed-with-corrections | Re-attribute the citation. The advice itself is sound and worth acting on; only the source is wrong. | [01](sections/01_usb_input_power_path.md) |
| USB-17 | HARDWARE.md's "~1 nA" TPS2116 reverse leakage is the 25 C figure only | confirmed | Add the temperature qualifier. The conclusion that removing D1 was safe is unaffected: even 0.15 uA is swallowed by the 400 kΩ PR1 divider and the 2 kΩ LED leg on USB_VB… | [01](sections/01_usb_input_power_path.md) |
| USB-18 | HARDWARE.md's "No battery fitted | CHRG + STDBY | ~0.45-0.53 V" row merges two unrelated states | confirmed-with-corrections | Split the row into "no battery / oscillating = 0.45 V alternating with 0.59 V" and a separate labelled entry for ST+STDBY at 0.53 V. | [01](sections/01_usb_input_power_path.md) |
| USB-19 | HARDWARE.md's USB_STAT state table has no named row for ST+STDBY (0.531 V) or all-three-low (0.404 V) | confirmed | Add the two rows and label the 0.53 V reading explicitly as "USB attached, pack full, but the mux has handed over to the battery" - it is the state most likely to be sil… | [01](sections/01_usb_input_power_path.md) |
| USB-V05 | CR1's schematic symbol is out of sync with its library and is named for a different part than the one fitted | added-by-verifier | Give CR1 a symbol named for the part actually fitted and re-sync it with the library, which also clears three of the four ERC warnings on this block. Do this before anyo… | [01](sections/01_usb_input_power_path.md) |

## CERT-LATER (17)

| ID | Finding | Verdict | Recommendation | Section |
|---|---|---|---|---|
| EPD-13 | Minimum 0.201 mm copper gaps between the +/-20 V nets and their neighbours | confirmed-with-corrections | Fine for a prototype. If this ever goes for EMC/safety certification, or if the enclosure will see humidity or condensation, widen the +/-20 V nets' clearance to 0.35-0.… | [06](sections/06_eink_driver_connector.md) |
| EPD-14 | The boost pulls pulsed current from the shared 3V3 rail that also feeds the panel's VCI | confirmed | Measure 3V3 ripple at J2 pins 15/16 during a full refresh. If it exceeds roughly 50 mV, add a small ferrite plus 1 uF between 3V3 and J2 pins 15/16 on a respin. | [06](sections/06_eink_driver_connector.md) |
| HMI-18 | U7 sits 8.3 mm from J4, and open ladder legs leave floating stubs up to 64 mm long | confirmed | Ignore for the prototype, exactly as the owner's standard says. If EMC certification is ever pursued: move U7 to within 2-3 mm of J4, and move each ladder leg resistor n… | [08](sections/08_buttons_rtc_touch_expansion.md) |
| LAY-C1 | Front-light taps to J6 form a ~170 mm out-and-back loop on PWM-switched nets, mostly on the ground-plane layer | confirmed | Ignore for the prototype. For EMC work later, either drop the J6 LED taps or run each go/return pair adjacent. These three nets are also the main reason F.Cu is cut into… | [10](sections/10_layout_area_walk.md) |
| LAY-C2 | I2C runs 179/184 mm with ~110 mm of each on the top-layer ground plane | confirmed | No action now. For EMC, the two long F.Cu runs slot the plane under other signals and radiate the 400 kHz clock and its harmonics. | [10](sections/10_layout_area_walk.md) |
| LAY-C3 | 68 GND stitching vias and no edge via fence on a 60 x 111 mm 2-layer board | confirmed | Ignore for the prototype. A via fence along the board edges and a denser stitch grid are normally needed to pass radiated-emissions limits on a 2-layer design. | [10](sections/10_layout_area_walk.md) |
| LAY-C4 | USB differential pair has asymmetric via counts (DP 3 vias, DN 1 via) | confirmed | Irrelevant at USB Full-Speed (12 Mbit/s, which is what the ESP32-S3 native USB runs). Equalise if the design ever moves to High-Speed. | [10](sections/10_layout_area_walk.md) |
| LAY-C5 | Narrow single-point-connected GND slivers on F.Cu act as resonant stubs | confirmed | Ignore for the prototype. Add a via to each, or let the zone filler drop them, before any emissions testing. | [10](sections/10_layout_area_walk.md) |
| LAY-C6 | The ESP32 antenna sits in a recess with ground pour ~0.5 mm away on three sides | confirmed | Ignore for the prototype -- WiFi will work. If RF certification or range matters, deepen and heighten the recess so the pour is further from the antenna. | [10](sections/10_layout_area_walk.md) |
| LAY-C7 | SD bus length skew of 23.6 mm between SD_CLK and SD_DAT1 | confirmed | No action. Worth remembering only if the SD bus is ever pushed faster. | [10](sections/10_layout_area_walk.md) |
| LED-11 | 25 V, 1.1 MHz-rippled LED nets routed ~180 mm across the board on the outer layer | confirmed | Nothing to do for a prototype - the owner has explicitly deprioritised EMI. For any future EMC work: shrink the LED loop area, add a series ferrite or an RC snubber at L… | [07](sections/07_led_frontlight_driver.md) |
| MCU-12 | No series resistor on U0TXD | confirmed | Ignore for the prototype — the trace is 5.6 mm long and goes to a bare pad. Add a 33 ohm series resistor if EMC certification is later pursued. | [04](sections/04_esp32_core_gpio_map.md) |
| PWR-13 | LDO input/output loops and ground returns are routed for convenience, not for loop area | confirmed | Ignore for this spin. If EMC/FCC work is ever pursued, tighten the C4 -> U3 pin1 -> pin2 and U3 pin5 -> C21 -> pin2 loops onto one layer and give both capacitors solid g… | [03](sections/03_ldo_power_tree_sleep_budget.md) |
| SD-14 | 33 Ohm series resistors are well below the ~138 Ohm trace impedance, so the bus is under-damped - and HARDWARE.md states the opposite | confirmed | Leave the resistors alone for the prototype: the MCU-to-card runs are only 5.95-7.94 mm, so reflections settle in well under a nanosecond and this cannot cause a functio… | [05](sections/05_sdmmc_microsd.md) |
| SD-V02 | The F.Cu ground pour under the socket and the SD bus is cut by several signal traces (the original review's 'continuous return path' is wrong) | added-by-verifier | Accept for the prototype. The crossings are near-perpendicular (minimal crosstalk into the analog BUTTON_ADC_2 net), the MCU-to-card runs are only 6-8 mm, and the extra … | [05](sections/05_sdmmc_microsd.md) |
| USB-12 | D+/D- are not impedance-controlled, via-asymmetric and 46 mm long; U6's CC channels have only 5.5 V standoff | confirmed | Nothing to do for a prototype: USB full speed is 12 Mbps with 4-20 ns edges and is entirely insensitive to this, and the ESP32-S3's native USB bootloader will enumerate.… | [01](sections/01_usb_input_power_path.md) |
| USB-13 | Shield RC network is 20.4 mm of thin trace from the shell pad and the shell is DC-isolated by 1 MΩ | confirmed | Fine for a plastic-enclosure prototype. For ESD/EMC work, place C1 within a few millimetres of the shell pad and consider a direct shell-to-ground tie or a second C1 nex… | [01](sections/01_usb_input_power_path.md) |

## Refuted by verification (6)

| ID | Finding | Verdict | Recommendation | Section |
|---|---|---|---|---|
| BAT-09 | TP4056 exposed pad connects to the GND pour through thermal relief rather than a solid connection *(was LOW)* | refuted | The zone default is indeed thermal relief (pad_connection 1), but pcbnew GetLocalZoneConnection() on the scratch copy returns 2 (FULL/solid) for both U11 EPAD copper pads (2.41x3.3 mm on B.Cu and 1.9x2.9 mm on F.Cu); only the six 0.5 mm via pads inherit. A both_copper_xray crop (scratch: battery_verify/u11_xray.png) shows the F… | [02](sections/02_battery_charger_protection.md) |
| EPD-02 | Pin-1 orientation of the panel tail is unprovable from the design data; a reversed tail back-powers the driver IC *(was MEDIUM)* | refuted | The auditor's key premise is factually wrong: the p.5 drawing DOES carry a view convention ('3rd Angle Projection' symbol in the title block, visible bottom-left of the page). I viewed the front-view tip crop: the view with TFT AA/Border dims and the '4.26" EPD' caption has contacts drawn solid (visible) with '1' at page-top an… | [06](sections/06_eink_driver_connector.md) |
| HMI-20 | Silkscreen recipe for the alternate touch pinout omits R66 - panel VDD left floating *(was HIGH)* | refuted | REFUTED. The B.Silkscreen text actually reads 'some displays are different / they swap INT/VDD and SCL/SDA / if so, unpopulate R42,44,46,52 / then, populate R43,45,58,66' - R66 IS listed. Verified twice and independently: (1) by pcbnew text dump of the scratch copy, and (2) by reading the gr_text at '(at 95.9 137.4 0)', layer B… | [08](sections/08_buttons_rtc_touch_expansion.md) |
| MCU-02 | DS3231MZ VCC tied to GND / VBAT tied to 3V3 — documented as deliberate, but I could not verify the datasheet claim *(was MEDIUM)* | refuted | DS3231M datasheet (Maxim 19-5312 Rev 5, text in scratch) re-read: VCC pin description ends 'Connect to ground if not used'; 'Figure 5 illustrates a single-supply configuration using VBAT only, with the VCC input grounded'; 'the oscillator does not start up until VCC exceeds VPF or until a valid I2C address is written'. Netlist … | [04](sections/04_esp32_core_gpio_map.md) |
| PWR-08 | Light sleep silently back-powers the gated-off microSD card through its pull-ups *(was HIGH)* | refuted | Re-read ESP32-S3-WROOM-1 DS v1.8 Table 6-7 as text: the Light-sleep row itself says 'VDD_SPI and Wi-Fi are powered down, and all GPIOs are high-impedance'; footnote 1 ('all related SPI pins are pulled up', followed by the PSRAM adders) describes the module's internal flash/PSRAM SPI pins under the measurement condition, not use… | [03](sections/03_ldo_power_tree_sleep_budget.md) |
| PWR-12 | DS3231MZ is wired VBAT-as-primary with VCC grounded: legal, but there is no timekeeping backup and the oscillator needs a firmware kick *(was DOC)* | refuted | Wiring is as stated (U13.2 VCC -> GND, U13.6 VBAT -> 3V3, RST/INT/32KHZ unconnected) and is datasheet-legal. But it is NOT a documentation gap: HARDWARE.md section 10 (lines 1002-1013) states VBAT->3V3 / VCC->GND, names it the datasheet's single-supply VBAT-only configuration, and lists the consequences (oscillator does not sta… | [03](sections/03_ldo_power_tree_sleep_budget.md) |

## Recovered from the earlier audits (22)

Items the earlier audit work had raised, that the blind audit did not cover, and that were re-checked and found still true of the current design (commit `c0eccde`). REC-A-02 and REC-B-01 are the same issue found from two corpora.

| ID | Severity | Finding | Recommendation | Earlier source | Comparison report |
|---|---|---|---|---|---|
| REC-A-01 | MEDIUM | No VBUS-sense input: a self-powered USB device with nothing to monitor | Keep the owner's acceptance but state it explicitly in the final report rather than letting it disappear: the board cannot tell firmware, digitally and unambiguously, whether USB is present. For the prototype this is a firmware constraint (tear down USB on a … | DESIGN_REVIEW.md 3, 'Self-powered USB needs a disconnect policy' - raised, then Decision (2026-09-17): accept… | [A](comparison/A_vs_DESIGN_REVIEW.md) |
| REC-A-02 | MEDIUM | Fix 4 cannot start charging a 0 V / protection-latched pack | Worth one sentence in the user-facing docs, because a dead-pack-in / nothing-happens board is indistinguishable from a broken board. The prior review already names the cheap fix: a two-pad manual-override jumper from /DET_NODE to GND. Note the interaction wit… | DESIGN_REVIEW.md 4, 'Known, accepted limitation - not treated as a defect... Judged an unrealistic/insubstant… | [A](comparison/A_vs_DESIGN_REVIEW.md) |
| REC-B-01 | MEDIUM | Fix-4 CE gate cannot revive a 0 V or protection-latched pack | Keep it as an owner-accepted limitation, but carry it into the final report: it is the single most likely 'my board is broken' support question, and it is a behaviour change from the pre-Fix-4 board where CE was tied to VBUS and the charger always tried. The … | all_findings.json key fix4-dead-pack-no-recovery (high); status_table.md WON'T-FIX ('owner accepted 0V pack n… | [B](comparison/B_vs_audit_2026-09-18.md) |
| REC-B-02 | MEDIUM | U11's exposed pad has 4 of 6 via-in-pad vias directly under solder-paste windows; U4's 12 are correctly windowpaned | Publish the per-part split in the final report. For U11 either request JLC's via-in-pad plugging service (it covers 0.15-0.55 mm holes, extra cost) or move the six vias into the paste-window gaps exactly as U4's twelve already sit. State explicitly that U4 ne… | all_findings.json keys tp4056-epad-vias-under-paste (high, verifier downgraded to medium) and esp32-epad-vias… | [B](comparison/B_vs_audit_2026-09-18.md) |
| REC-B-03 | MEDIUM | After any DW01A protection trip the board cannot restart from the cell alone, and nothing documents it | One paragraph in HARDWARE.md section 3: 'after any protection trip - over-discharge, over-current or short - the board will not restart from the battery; plug in USB to re-arm the DW01A.' No hardware change. Worth pairing with REC-B-01 in the same doc edit, s… | all_findings.json keys dw01a-lockout-q8-gate-gnd (low) and dw01a-trip-needs-usb-release (info); status_table.… | [B](comparison/B_vs_audit_2026-09-18.md) |
| REC-A-03 | LOW | U10's current limit and the C9 hot-plug inrush both exceed L2's saturation rating | Fold into the first-article scope check that already exists (DESIGN_REVIEW 13 step 12c). Brief saturation of a 2520 shielded inductor on a hot-plug transient is normally survivable; the point is that it has never been checked against a number, and the applied… | DESIGN_REVIEW.md 8, 'Inductor, protection and layout' plus the C9 output-cap sizing note (applied 2026-09-18). | [A](comparison/A_vs_DESIGN_REVIEW.md) |
| REC-A-04 | LOW | Q7 switches SD_VDD on in microseconds - far faster than the SD spec's suggested VDD ramp | Keep as a conditional, not a change. The prior already names the optional fix (47-100 nF gate-to-3V3, tau 50-100 us with R78) and correctly gates it on first-article card-init behaviour. | DESIGN_REVIEW.md 6, 'Electrical checks' - Q7 (SD VDD switch) has no gate slow-down (added 2026-09-18). | [A](comparison/A_vs_DESIGN_REVIEW.md) |
| REC-B-06 | LOW | Several 0603 passives sit 0.24-0.60 mm from the routed board edge | Accept for a prototype spin - JLC routes rather than V-scores this outline, so the stress is modest. Note it for the next revision so routing vibration and edge chipping do not land on populated pads. | all_findings.json key near-edge-passive-components (medium); status_table.md OPEN | [B](comparison/B_vs_audit_2026-09-18.md) |
| REC-B-07 | LOW | 0.14 mm dangling copper tail on the PREVGH (15-22 V) net | Delete the stubs in the next PCB pass. Cosmetic, but they are on the highest-voltage net on the board, so they are the worst place to leave unterminated copper. | all_findings.json key dangling-stub-prevgh (low); status_table.md OPEN ('PREVGH stubs 0.14 mm @ (82.7,127.2),… | [B](comparison/B_vs_audit_2026-09-18.md) |
| REC-B-08 | LOW | J2's shield/mount pads are 1.5 x 1.5 mm where Hirose's land is 0.4 x 0.9 mm, so pasted copper runs under the housing | Leave it if the prototype boards assembled cleanly; otherwise trim the shield pads to Hirose's land or shrink the paste aperture to the outer 0.5 mm. Worth reviewing in the same pass as LED-01, since both are paste-aperture decisions on the same three connect… | all_findings.json key j2-mount-pads-oversize-vs-hirose (low); status_table.md OPEN ('J2 unchanged (prototype … | [B](comparison/B_vs_audit_2026-09-18.md) |
| REC-B-09 | LOW | U10's custom DRL0006A footprint uses 0.229 mm-wide pads against TI's 0.30 mm example land pattern | Accept for a prototype - the narrower pad also reduces bridging risk on a 0.5 mm pitch. If a joint looks starved on the first article, widen to TI's pattern on the next spin. Worth checking on the first board together with LED-01's FPC pads, since both are so… | all_findings.json key u10-custom-footprint-narrower-than-ti-pattern (info); not tracked in status_table | [B](comparison/B_vs_audit_2026-09-18.md) |
| REC-B-10 | LOW | EPD rail capacitors C11/C13-C17 retain only about 0.7-1.1 uF of their 4.7 uF at 15-22 V | State the effective value in HARDWARE.md next to the nameplate so nobody sizes the rails or estimates refresh droop from 4.7 uF. No change needed for a prototype. | all_findings.json key epd-rail-caps-effective-capacitance (info); not tracked in status_table | [B](comparison/B_vs_audit_2026-09-18.md) |
| REC-B-11 | LOW | L2's saturation current is below the TPS923610's cycle-by-cycle current limit | Scope L2's current at battery hot-plug on the first article, or accept brief saturation - it is self-limiting and the driver recovers. Worth one line in HARDWARE.md because the C9 increase made this worse, not better. | all_findings.json key l2-isat-below-tps923610-ilim (low); status_table.md OPEN; CHECKPOINT_2.md section 3 (ho… | [B](comparison/B_vs_audit_2026-09-18.md) |
| REC-B-12 | LOW | Silkscreen and mechanical cosmetics the new audit dropped | Batch all five into the same silkscreen pass as FAB-09 and LAY-12. The QR module sizing and the BAT+/P+ naming are the two worth actually fixing; the rest are proofreading. | all_findings.json keys welcome-text-missing-noun, credits-orphan-punctuation-near-sw11, qr-module-size-incons… | [B](comparison/B_vs_audit_2026-09-18.md) |
| REC-C-01 | LOW | Q5/Q6 colour-select pair has no guaranteed non-overlap, and nobody has measured it | Bring-up item, not a board change. Scope Net-(Q5-S) across R37 and the boost output through a colour change at several PWM duties and confirm the transition does not trip OVP. If it does, gate colour changes to happen only while ADIM is low, or add a small RC… | docs/audit-2026-09-16/component-review.csv, rows U12 ('Static complementary logic does not guarantee nonoverl… | [C](comparison/C_vs_audit_2026-09-16_and_nextpcb.md) |
| REC-C-02 | LOW | SW6 carries flags=dnp without exclude_from_bom - a third DNP leak that HMI-V01 does not list | Set exclude_from_bom on SW6 in the same edit as R72/R74, so every DNP part is handled one way and no importer can leak any of them. | docs/audit-2026-09-16/bom-verification.json, dnp_flag_disagreements: ['SW6','U13']; and fabrication/NEXTPCB_R… | [C](comparison/C_vs_audit_2026-09-16_and_nextpcb.md) |
| REC-C-03 | LOW | The deep-sleep budget assumes TI's LDO quiescent current, and fabs substitute the brand | One line in the BOM notes and in HARDWARE.md's sleep section: 'U3 must be the genuine TI part - the sleep budget depends on its ~25 uA Iq; reject brand substitutions on this line.' It turns a footnote in a fab-order log into a design constraint. | fabrication/NEXTPCB_REV0_NOTES.md section 2, matched-BOM check: "Third-party brands attached to generic parts… | [C](comparison/C_vs_audit_2026-09-16_and_nextpcb.md) |
| REC-C-04 | LOW | CR2/CR3 cannot hold the 3V3 or battery rails inside the absolute maximum of what they protect on J6 | Treat it as the new audit treats USB-04: document, do not respin. A line in HARDWARE.md's protection section saying the header TVS diodes are surge clamps and not rail limiters, plus a note that J6 is not hot-plug-rated. If a revision happens, a lower-standof… | docs/audit-2026-09-16/component-review.csv, rows CR2 ('5V TVS on 3.3V rail: no normal-DC stress; surge clamp … | [C](comparison/C_vs_audit_2026-09-16_and_nextpcb.md) |
| REC-C-05 | LOW | The documented button mechanics do not hold for the NextPCB build route | Add the depth delta to the Reason column of nextpcb_substitutes.csv (BOM-14 already asks for exactly this treatment on L1), and add one sentence to the enclosure section: the MEC-07/MEC-08 protrusion figures apply to the MJTP1117 build only; re-derive them if… | fabrication/NEXTPCB_REV0_NOTES.md section 2: "ALPS drawing No. 3 gives the same land as the MJTP1117/TS365ZJ … | [C](comparison/C_vs_audit_2026-09-16_and_nextpcb.md) |
| REC-B-04 | DOC | DESIGN_REVIEW.md still analyses Q3/Q8 and the Fix-4 pass FET as AO3419 | Global replace in DESIGN_REVIEW.md, or one banner at the head of the reverse-battery section stating that every AO3419 reference means the fitted AO3401A and that the quoted ratings should be re-read from the AO3401A datasheet. Related and also understated by… | all_findings.json keys docs-ao3419-vs-ao3401a (low, PARTLY) and stale-symbol-metadata-docs (low, PARTLY); sta… | [B](comparison/B_vs_audit_2026-09-18.md) |
| REC-B-05 | DOC | U12 is inconsistent across the two BOMs and has no JLC footprint model | Pick one prime MPN for U12 and use it in both BOM files. Add U12 to the JLC placement-preview check list alongside U2/U10/D8, since it is the one part whose rotation cannot be checked any other way. | all_findings.json keys u12-prime-mpn-mismatch-handbuild-bom (low) and u12-no-jlc-footprint-model (low); statu… | [B](comparison/B_vs_audit_2026-09-18.md) |
| REC-A-05 | CERT-LATER | No USB D+/D- series-damping footprints, contrary to Espressif's schematic checklist | CERT-LATER by the owner's standard. At 12 Mbps Full Speed this is a signal-quality nicety; if a revision happens, two 0 Ohm 0402 footprints in series cost nothing and buy an option. | DESIGN_REVIEW.md 11, 'USB: small real skew, imperfect return path'. | [A](comparison/A_vs_DESIGN_REVIEW.md) |
