iandchasse/silkscreen-pcb/docs/final-review-2026-09-19/FINDINGS_TABLE_author_refute.md

# All findings — final review 2026-09-19

Generated from the structured results of the 13 auditors and 12 verifiers (`findings.json`). *Severity* is the severity **after** verification; *was* shows the auditor’s original grade where the verifier changed it. 
Verdicts: `confirmed`, `confirmed-with-corrections` (the section file carries the corrected numbers), `refuted`, `unverifiable`, `added-by-verifier`, `not-verified` (section 13, documentation, had no verifier — it is editorial judgement).
Full evidence, calculations and sources for every ID are in the section file named in the last column.

> **Author response added (column "Author refute", drafted 2026-09-20).** Blank means the author has not disputed the finding; it does not mean the finding was accepted. Entries are tagged **REFUTED** (the claim is factually wrong), **BY DESIGN** (a documented choice), **PARTLY DISPUTED** (the point is valid in part, or the numbers differ) or **ACCEPTED RISK**. Paths are relative to the repository root. Please re-verify each tagged item against the evidence given, then revise its severity and verdict and the dependent text in `FINAL_REVIEW.md`.
>
> **Method note.** LED-01 shows that pad layer sets and aperture-flash counts cannot see paste (or mask) that a footprint draws as filled regions or graphic polygons. Please re-check any other finding whose evidence relies on those methods (for example SD-03, FAB-V01 and the pad counts quoted in the LED-01 verifier notes) by reading the gerber regions as well as the flashes.

## BLOCKER (1)

| ID | Finding | Verdict | Recommendation | Author refute | Section |
|---|---|---|---| --- |---|
| LED-01 | J3 (and J2/J4) signal pads have no solder-paste apertures - connectors will not be soldered in a fab-assembled build | confirmed | Add B.Paste to pads 1-N of all three HRS_FH34SRJ-* footprints (or override per-pad on the board), re-export the paste gerber, and re-verify by counting flashes on the connector rows before placing any assembly order. Costs nothing; without it the board returns with no display, no front light and no touch. | **REFUTED.** Paste is present on all 36 signal pads of J2 (24), J3 (6) and J4 (6). In `production/Silkscreen_Reader_PCB_1.0.zip`, `silkscreen_pcb-B_Paste.gbp` (and your own `evidence/gerber_fresh/silkscreen_pcb-B_Paste.gbp`) holds 36 unique filled regions (G36/G37 polygons), each 0.25 x 0.65 mm, lying inside a 0.30 x 1.15 mm pad (about 47 % of the pad area, 0.35 mm from one pad end and 0.15 mm from the other). The vendor footprint draws paste as graphic polygons on F.Paste (mirrored to B.Paste on this bottom-mounted part), not as a pad layer: see `KiCad/9.0/3rdparty/FH34SRJ_6pin/HRS_FH34SRJ-6S-0.5SH_50_.kicad_mod` (the paste polygons after the pad list); pcbnew reports 24 / 6 / 6 filled B.Paste shapes on J2 / J3 / J4. The finding's method (pad layer sets, and counting aperture flashes) cannot see region-drawn paste, so 0 flashes and no B.Paste pad layer do not mean no paste. The recommended fix would put a full-pad window on top of the existing polygons (about 100 % coverage at 0.5 mm pitch), which invites bridging: do not apply it. Please withdraw the BLOCKER and the dependent text (FINAL_REVIEW.md fix #1, the section 06 remark, the first bullet of section 9.1, and the '41 SMD pads carry no paste layer' count in the verifier notes). | [07](sections/07_led_frontlight_driver.md) |

## HIGH (16)

| ID | Finding | Verdict | Recommendation | Author refute | Section |
| --- | --- | --- | --- | --- | --- |
| BOM-01  | R14 ordering code has 12 pieces in stock; a fee-free Basic alternative the docs say does not exist *(was BLOCKER)* | confirmed-with-corrections | Change R14's LCSC field to C22939. It is in stock, it is JLC Basic (saves a ~$1.50 Extended loading fee) and it is half the price. The only spec difference is tempco, +/-400 ppm/C vs Yageo's +/-200 ppm/C, which over a 60 C rise is 2.4 % on a current-sense value and immaterial here. Keep Yageo RC0603FR-072R2L as the DigiKey-prim… | Valid - should be addressed | [12](sections/12_bom_function_and_cost.md) |
| DOCS-01 | No firmware exists or is linked, and no document says so | not-verified | Add a Software section to the README stating plainly what exists today, where it lives, and the literal first-power-up command. If no firmware is released, say so in the first 20 lines — it changes who should attempt this build. | FreeInk SDK will be ported, maintaining crosspoint-reader, crossink reader, other XTEink X4 firmwares. This is all future planned, not present work | [13](sections/13_docs_end_user_readability.md) |
| DOCS-02 | The README's recommended ordering route is a configurator that does not exist | not-verified | Demote to a one-line "a configurator is planned at silkscreenreader.com" note and make the manual path in steps 1-7 the primary, unqualified instruction. Remove or re-source the $29.55 figure. Do not describe an unavailable tool as the recommended route. | It does exist, just guarded behind site preview. Not live yet, but will be when people read it | [13](sections/13_docs_end_user_readability.md) |
| DOCS-03 | Three BOM files offered as interchangeable; two contain duplicate LCSC codes that break the JLCPCB match | not-verified | Name exactly one file in the ordering step: "Upload production/bom_JLC_upload_v4_optimized.csv." Move bom.csv and v3 to a reference note, and state the duplicate-code failure mode in the README where the reader meets it, not only in the NextPCB notes. | One file will be provided, the cheapest (the V4) | [13](sections/13_docs_end_user_readability.md) |
| DOCS-04 | No shopping list for anything that is not on the PCB | not-verified | Add a "What else you must buy" table to the README: panel variant mapped to which optional blocks to fit, with vendor link and price; battery (single-cell 4.2 V, capacity, JST-PH 2.0 connector, pin 1 = B-); microSD; USB-C cable; M2 screws and standoffs; case. | This is a good point. Battery with lead order on JST-PH should be indicated to reader. microSD card, usb-c cable are also important. M2 screws, case, etc. are separate and would be part of an individual case design. | [13](sections/13_docs_end_user_readability.md) |
| DOCS-05 | No safety warning of any kind on a board that charges a lithium cell | not-verified | Add a boxed safety block near the top of the README: LiPo pigtail polarity is not standardised; J5 pin 1 (marked -) is battery negative; meter the cell's leads before plugging in; use a cell with its own protection board; do not charge unattended; do not use a puffed cell. Repeat it in the first-power-up section. | I have +/- labeled on the connector with "CHECK" on the board, unaware if there is any other standard warning. Would think puffed cell/etc would be obvious. | [13](sections/13_docs_end_user_readability.md) |
| DOCS-06 | README's first instruction sends a newcomer into a 100 KB engineering review | not-verified | Re-order the README per the outline in the section file. Keep the DESIGN_REVIEW pointer but place it under "For engineers / before you modify this design", not as step 0 for a builder. | Good point, valid | [13](sections/13_docs_end_user_readability.md) |
| DOCS-07 | "Case agnostic" means no enclosure files and no published mechanics | not-verified | Either publish the reference enclosure, even roughly, or add a Mechanical section: outline 60.05 x 111.30 x 1.6 mm, the five M2 hole coordinates, connector and button edge positions, the battery cut-out, and an exported board STEP. State explicitly that no case is supplied. | Good point. "Case agnostic" implies any case, but rather I'd want to imply that it could hypothetically work with multiple case designs of any aesthetic preference, which is dependent on the board's 3D model etc being available. The board's STEP file should be available to everyone, and the wording should be revised. Valid | [13](sections/13_docs_end_user_readability.md) |
| DOCS-08 | Public URL on the board, in NOTICE and in both title blocks lands on a different project | not-verified | Before any board is handed to anyone: merge 06_2026 into master or change the repository's default branch, add a description and topics, and confirm the README renders on the landing page. No other documentation fix matters until a reader can reach the files. | I should probably change the github link, valid. | [13](sections/13_docs_end_user_readability.md) |
| DOCS-09 | README says choose JLCPCB "Standard" without preparing the reader for Standard's size, edge-rail and fiducial requirements | not-verified | Explain why Standard is mandatory (the module is Standard-only), and warn that JLCPCB will add edge rails to reach the Standard minimum — expect a rail on each long edge, a small extra cost, and rails to snap or file off. Ask the reader to confirm in the DFM preview that the rails do not cross the four 0.5 mm perforation slots … | I don't really understand this. You could maybe say that standard PCBA is required for including ESP32-S3 module, and that excluding it to hand-solder it could save money potentially. The rails.... unsure what that has to do with anything? | [13](sections/13_docs_end_user_readability.md) |
| HMI-01  | Raw LiPo P+ exposed on J6 pin 12 with no fuse, PTC or any series element | confirmed | Fit a 0.5-1 A PPTC (1206) in series with J6 pin 12 and add a BAT+ warning to the silkscreen. About ten cents, and it turns a smoke failure into a click-off failure. Not called a BLOCKER because the DW01A is present and the owner assembles the boards himself. | I can add this if it's cheap and convenient. But I don't know what this does for the use-case of the header? Would this enable hot plugging for header devices that make use of P+? | [08](sections/08_buttons_rtc_touch_expansion.md) |
| LAY-01  | Four tongue-neck routed slots are 0.50 mm wide, below every common fab's minimum slot width | confirmed | Widen all four neck slots to >= 1.0 mm and redraw all five slot polygons at 0.05 mm line width to match the rest of the outline. Get an explicit DFM answer from the fab before ordering; treat this as a blocker if they cannot cut 0.5 mm, because the likely silent outcomes are that the slots are widened (changing the cut line) or… | I will remove these slots in favor of one wide slot | [10](sections/10_layout_area_walk.md) |
| MEC-01  | Flex slot is 1.30 mm wide — narrower than the 1.60 mm board — and is the only path for all three display flexes *(was BLOCKER)* | confirmed-with-corrections | Widen the slot to >= 2.5 mm, ideally 3.0 mm, and radius or chamfer both lips. A 3 mm slot still leaves 4.05 mm of the 5.75 mm bezel strip below it. Also confirm the fab will route a 47 mm slot that close to the edge. | This is fine, seems to fabricate fine. | [11](sections/11_mechanical_enclosure_assembly.md) |
| MEC-02  | The 'cut for smaller displays' line severs raw battery positive 0.15–0.20 mm from ground pour on both layers | confirmed | Add a bold silkscreen warning 'DISCONNECT BATTERY BEFORE CUTTING' next to the existing note. Better: add a 2 mm-wide copper keep-out band centred on y = 61.86 so no copper at all crosses the cut face, or route P+ to J6 by a path that does not cross the line. | I will add disclaimer. No keepout. | [11](sections/11_mechanical_enclosure_assembly.md) |
| MEC-23  | Top face is not flat: 58 soldered through-hole leads protrude inside the panel's footprint | confirmed-with-corrections | Decide and document the panel seating plane. Preferred: clip and file every through-hole lead flush on the panel side during assembly (add it as an explicit build step, with a straightedge check) so the panel can sit flush and the flex slack is preserved. Alternative: design the case to hold the panel on a >= 1.5 mm standoff, a… | Doesn't have to be flat. screen will be buffered in most designs. | [11](sections/11_mechanical_enclosure_assembly.md) |
| SD-V01  | The microSD card-insertion corridor runs straight through the battery cut-out | added-by-verifier | Settle this before the enclosure and ideally before ordering, since one of the three answers is a respin. (a) Confine the cell to the upper-left of the cut-out so a channel at least ~17.5 mm wide and ~20 mm deep stays clear in front of J7, and record the resulting maximum cell dimensions in HARDWARE.md section 5 and in the encl… | The battery must move before ejecting sd card. This is fine. | [05](sections/05_sdmmc_microsd.md) |

## MEDIUM (70)

| ID | Finding | Verdict | Recommendation | Author refute | Section | | |
| --- | --- | --- | --- | --- | --- | --- | --- |
| BAT-02  | DW01A reference-design R1 (100 ohm from cell to VCC) is not fitted | confirmed | Insert a 100 ohm 0603 between P+ and U5 pin 5, keeping C7 on the U5 side. Sense error is only 0.6 mV at the DW01A's 6 uA supply current. It also current-limits the reverse-polarity fault into U5 (helps BAT-03). HARDWARE.md section 3.3 already notes the omission, but the board as released still does not have it. | in previous design, 100ohm resistor between Q8 and Pin 5 produced voltage drop to P+. Replaced with solder bridge and it works fine. Unsure what this gains. | [02](sections/02_battery_charger_protection.md) | | |
| BAT-03  | With a reversed pack the DW01A's VCC sits below its GND, outside absolute maximums | confirmed-with-corrections | Fit BAT-02's 100 ohm (limits fault current into U5), and/or add a small Schottky from U5 VCC to U5 GND with the cathode on GND to clamp the excursion to -0.3 V. HARDWARE.md section 3.3 already describes this fault path; the datasheet citation and the clamp are the additions. | Reversed pack voltage should not pass through to DW01A due to Q3 reverse polarity protection | [02](sections/02_battery_charger_protection.md) | | |
| BAT-V04 | J5 is wired circuit 1 = B-, circuit 2 = B+; SparkFun's published JST-PH convention is pin 1 = +VBATT - possible mismatch with common hobby packs (unverified) | added-by-verifier | Before ordering, hold the intended pack against a 1:1 print or the 3D view and confirm. Write the convention into README in physical terms and name a known-good pack. If the board turns out opposite to the packs most replicators will buy, swapping the two nets at J5 before fab is a five-minute edit (silk must follow); after fab… | Known good pack off Amazon will be included in shopping list to viewer of project. There is no standard for these batteries. | [02](sections/02_battery_charger_protection.md) | | |
| BOM-02  | C4/C6/C32 DigiKey MPN is obsolete with zero stock, and DigiKey's own suggested substitute is also at zero *(was HIGH)* | confirmed-with-corrections | Change the MPN to Murata GRM21BR61E226ME44L: 22 uF 25 V X5R +/-20 % 0805, 1.45 mm max thickness, 1,751,511 in stock at DigiKey, $0.36/1, $0.216/10, $0.1405/100 (verified live 2026-09-20). Same case size and thickness as the Samsung part, so no footprint or height change. One edit unblocks the hand-build, PCBWay and NextPCB BOMs. | Valid, will subsitute if needed. | [12](sections/12_bom_function_and_cost.md) | | |
| BOM-03  | JLC stock on three coded lines has fallen sharply since the 2026-09-18 crawl; two cannot cover a 10-board run *(was HIGH)* | confirmed | Re-crawl every LCSC code immediately before placing the order - the figures in BOM.md are two days old and already wrong by four orders of magnitude on one line. Order U10 spares from DigiKey or consign them. For C4/C6/C32 consider C45783 (= CL21A226MAQNNNE, JLC Basic, 1,734,789 in stock, $0.1185, verified live): about $0.25/bo… | Yes, always double check stock. Valid. | [12](sections/12_bom_function_and_cost.md) | | |
| BOM-05  | production/bom.csv still regenerates the duplicate-LCSC bug that was fixed by hand in the v4 upload file | confirmed | Normalise the schematic Value fields: set C24 and C31 to '0.1u' (or all six to '100n') and C20 to '1u'. Then every generated BOM merges correctly by itself, production/bom.csv stops disagreeing with the v4 upload file, and a known, already-experienced JLC matching failure cannot recur. | bom.csv will likely not be used from fabrication kit, but will revise. Valid. | [12](sections/12_bom_function_and_cost.md) | | |
| BOM-06  | D8 PESD2IVN-UX is Not For New Designs at DigiKey and no project document says so | confirmed | Buy now for the prototype - stock is adequate and the part is right for the job. Before any volume build, qualify an in-production dual bidirectional array with V_RWM >= 26 V and low capacitance, and add an 'NRND' note against D8 in fabrication/BOM.md so it is not forgotten at the next respin. | Ugh, will look into alternatives. I think this is a common part. Valid. | [12](sections/12_bom_function_and_cost.md) | | |
| BOM-07  | DS3231MZ RTC is 25 % of the DigiKey BOM cost and is beaten on price, accuracy and standby current at once | confirmed | For the next revision move U13 to RV-3028-C7: 5x better accuracy, ~50x lower standby current (which directly extends shelf life on a reader that spends most of its life asleep), and $11.44/board cheaper. If ppm-level accuracy is not actually needed, NXP PCF85063ATL is ~$0.60. Both need a schematic/footprint change, so this is a… | Replacements are not the same in functionality, either are not well stocked, or need an external crystal (another part that needs stable sourcing). Look into alternatives, I'm open to them. I've just spent too long doing so unsucessfully. | [12](sections/12_bom_function_and_cost.md) | | |
| BOM-09  | The lithium charge-and-protect subsystem is entirely untraceable clone-market silicon with no Western distributor source | confirmed | Two options, not mutually exclusive. (a) State explicitly in BOM.md that U11/U5/Q1 are LCSC/Asia-only clone parts with no traceable source, and that the LiPo pack must carry its own protection PCM so this board's protection is a second layer rather than the only one. (b) For a future revision move to traceable silicon: the char… | Parts are sold on digikey, good enough for me | [12](sections/12_bom_function_and_cost.md) | | |
| BOM-V01 | The five TPD4E1U06 ESD arrays are the 4th-largest cost line and were never critiqued for necessity | added-by-verifier | Decide per array whether the port is genuinely user-exposed and record the decision. Dropping the two or three internal-only arrays saves roughly $1.76/board at DigiKey with no functional cost on a prototype; keeping all five is also defensible as cheap insurance and is the right answer if FCC/EMC work is planned later. Either … | They are all user exposed. I'm open to cost effective alts, but not confident. | [12](sections/12_bom_function_and_cost.md) | | |
| DOCS-10 | No cost or lead-time expectation anywhere in the README | not-verified | Put a two-line expectation at the top of the ordering section: about $260-305 for five assembled boards including shipping, about 2-3 weeks from upload to parcel, panel/battery/case extra. | sure, valid. | [13](sections/13_docs_end_user_readability.md) | | |
| DOCS-11 | Undefined jargon throughout the ordering path | not-verified | Add a short glossary box immediately before the ordering steps defining Gerber, BOM, CPL/centroid, PCBA, DNP, THT/SMD, LCSC and Basic/Extended in one line each. Replace "Fix 4" with what it is (the reverse-battery protection change). | Yes, valid. Define all and remove "fix 4" because it's irrelevant to user. | [13](sections/13_docs_end_user_readability.md) | | |
| DOCS-12 | No first-power-up checklist, no troubleshooting, and no route to get help | not-verified | Add a "First power-up" section (inspect, USB-C only with no battery, check the red LED and USB enumeration, then battery) and an "It doesn't work" section with the five likeliest causes ranked, plus one "Where to get help" line with a real URL. | First power up instructions will be provided later after firmware work is done. | [13](sections/13_docs_end_user_readability.md) | | |
| DOCS-13 | The assembly drawing, the one artefact that lets a novice audit the placement preview, is filed under the wrong fab | not-verified | Reference the drawing in the JLCPCB step too: "open production/other_fabs/assembly_drawing_bottom.pdf beside the preview and compare part by part." Consider moving it out of other_fabs/, since it is fab-independent. | other_fabs folder will be deleted, as the other fabs suck. | [13](sections/13_docs_end_user_readability.md) | | |
| DOCS-14 | The through-hole decision is presented as a checkbox rather than a costed choice | not-verified | State both options with their numbers: (a) let the factory solder them, adding a one-off hand-soldering fee and about a day; (b) decline and hand-solder 13 parts / 74 joints per board including a 20-pad USB-C. Recommend (a) for a first board. | Yes, valid. | [13](sections/13_docs_end_user_readability.md) | | |
| DOCS-15 | Licence section does not answer whether a reader may build or sell one | not-verified | Add three plain sentences: you may build it, use it and sell it; if you modify the design and distribute or sell the result you must publish your modified source under CERN-OHL-S v2; keep the NOTICE with it. Link THIRD_PARTY.md for the vendored symbol/footprint caveat. | Yes, valid. | [13](sections/13_docs_end_user_readability.md) | | |
| DOCS-16 | "Minimum quantity is 5" conflates the bare-board MOQ with the assembly quantity | not-verified | Reword: "You must buy at least 5 bare boards, but you can choose to have only 2 of them assembled — the cheapest way to get a working prototype, with three spares for later." | Yes, valid. Greatly reduces intro cost to buyer. | [13](sections/13_docs_end_user_readability.md) | | |
| DOCS-17 | README never says KiCad is not required, and opens with kicad-cli commands that imply it is | not-verified | Open the ordering section with "You do not need KiCad — everything you upload is already in the production/ folder; download the repository as a ZIP and you are ready." Move the kicad-cli blocks to a maintainers' "Regenerating the files" section near the end. | Sure. Was built with ki-cad, no plans to port over. | [13](sections/13_docs_end_user_readability.md) | | |
| DOCS-18 | The four 0.5 mm perforation slots are raised as a manufacturing risk and left unresolved | not-verified | Resolve it once and document the outcome: either "accepted on two previous orders — proceed and accept the DFM notice", or the exact reply to give if the factory queries them. A nervous reader stops at an unresolved warning. | These will be removed and replaced with 1 larger slot instead of 4 little ones | [13](sections/13_docs_end_user_readability.md) | | |
| DOCS-24 | README gives the wrong polarity rule for D2 and contradicts the repository's own BOM | not-verified | Correct both README occurrences to "pad 1 is the cathode". The consequence is cosmetic rather than damaging — D2 is only the USB-present indicator, so a reversed part simply never lights — but it is the single concrete polarity rule given to a novice and it is inverted. | Unfamiliar with what the README says or why it talks about the USB LED. Fix if it needs to be. | [13](sections/13_docs_end_user_readability.md) | | |
| FAB-01  | Smallest annular ring on the board is 0.150 mm, below JLCPCB's stated absolute minimum of 0.18 mm; J1's pad hole-to-hole is exactly at JLC's 0.45 mm limit | confirmed | Accept knowingly. Growing J1's pads to reach 0.18 mm would cut the pad-to-pad copper gap from 0.15 mm to 0.09 mm, trading one marginal number for a worse one. For a JLCPCB order expect a DFM query on J1 and be ready to approve as drawn; PCBWay meets 0.15 mm exactly and NextPCB has 60% margin. | **ACCEPTED RISK (reviewer agrees).** J1's pad pitch and hole spacing are the connector maker's land pattern (GCT USB4085-GF-A). The first ordered commit (b277809) shows the same J1 pad-clearance errors. | [09](sections/09_erc_drc_fab_outputs.md) | | |
| FAB-02  | Silkscreen lettering is about half the minimum legible size at every fab, and both DRC checks that would catch it are switched off | confirmed | Either raise all reference designators to >=0.8 mm height / >=0.15 mm stroke and accept some new silk-over-pad overlap, or knowingly treat the printed legend as decorative and rely on assembly_drawing_bottom.pdf plus InteractiveHtmlBom. Either way re-enable text_height and text_thickness so the decision is recorded rather than … | Haven't been told no... so ignore. | [09](sections/09_erc_drc_fab_outputs.md) | | |
| FAB-03  | No solder-mask dam between the 0.5 mm-pitch FPC pads of J2/J3/J4; the DRC check that reports it is switched off | confirmed | Set the local solder-mask expansion on J2, J3 and J4 to 0.000 mm, which restores the full 0.200 mm dam (2x JLC's minimum), then re-enable solder_mask_bridge and re-run DRC. | Doesn't seem to be an issue. The footprint came that way, already manufactured fine once. Explain benefit, if any. | [09](sections/09_erc_drc_fab_outputs.md) | | |
| FAB-06  | 25 starved thermal reliefs, two of which connect only to an isolated island of the ground pour | confirmed | Add a stitching via immediately beside U11 pad 1, J7 pads 6 and 9, U2 pad 1 and the two isolated-island button pads (SW4, SW9), or set those specific pads to solid zone connection. | Thermal relief unnecessary. Ignore. | [09](sections/09_erc_drc_fab_outputs.md) | | |
| FAB-10  | bom_JLC_upload_v3.csv is offered as a live alternative but still carries the duplicate-part-number defect that v4 was created to fix | confirmed | Either fix v3's duplicate lines the way v4's were fixed, or retire the file to production/backups/. A documented alternative that is known to mis-match three capacitors is worse than no alternative; at minimum the README should say so. | v3 irrelevant. There should be 1 BOM | [09](sections/09_erc_drc_fab_outputs.md) | | |
| FAB-14  | Two opposite bottom-side rotation conventions in the repo's centroid files, undocumented in the files themselves | confirmed | Put one header line in each centroid file stating the convention (bottom-side angle measured from the top view), and require the assembler to confirm against other_fabs/assembly_drawing_bottom.pdf and the online placement preview before the run. Never mix a JLC CPL with a NextPCB BOM. | **BY DESIGN.** The JLC files come from the Fabrication Toolkit, which applies JLC's bottom-side rotation convention (about 180 minus the KiCad angle, plus per-part corrections). The PCBWay and NextPCB files in `production/other_fabs/` use raw KiCad angles. The difference is deliberate and documented in `README.md`; extra header lines were not added because NextPCB's Rev0 sample defines a fixed header row. | [09](sections/09_erc_drc_fab_outputs.md) | | |
| FAB-16  | No fiducials anywhere on the board, on either side | confirmed | Add two or three 1 mm copper / 2 mm mask-opening fiducials on B.Cu, diagonally opposite, in the free space near H1 and H3 — or explicitly order breakaway rails with fiducials. All three fabs panelise a 60 x 111 mm board with rails and add their own, so this will not stop the order, but board-level fiducials cost nothing and rem… | Do not know what fiducials are. Explain. | [09](sections/09_erc_drc_fab_outputs.md) | | |
| FAB-21  | JLC rotation-correction database has no entry for U2 (SOT-583), U10 (SOT-563), D8 (SOT-323) or any of the diode/LED packages | confirmed | Before confirming a JLC order, set 'Confirm Parts Placement' to Yes and check pin 1 of U2, U10, U11, U13, D8, D2, D3, CR1, CR2, CR3 and D4-D6 against the datasheets in the preview. Add U10 to the documented preview checklist. | Valid. Fine fix. | [09](sections/09_erc_drc_fab_outputs.md) | | |
| FAB-22  | production/bom.csv splits two LCSC codes across two lines each — the exact fault that left parts unmatched at JLC before | confirmed | Make the Value strings consistent in the schematic (C24/C31 to '0.1u', C20 to '1u') so every generated BOM merges them automatically; or upload bom_JLC_upload_v4_optimized.csv, which already merges them. | Valid. Fix. | [09](sections/09_erc_drc_fab_outputs.md) | | |
| FAB-23  | Four interior routed slots are 0.716 mm wide, below JLCPCB's and PCBWay's minimum non-plated slot width | confirmed-with-corrections | If the snap-off feature these slots create must work, widen them to >=1.0 mm before a JLCPCB order. Otherwise expect them to be queried, silently widened to the bit size, or dropped — and correct the '0.5 mm' figure in both READMEs. | **REFUTED as a separate finding.** FINAL_REVIEW.md section 9.3 itself says the 0.716 mm figure wrongly adds the line width and that 0.516 mm is the correct centre-line value. These are the same four slots as LAY-01 and MEC-03; please withdraw or merge. JLCPCB accepted these slots on both earlier orders (25 and 30 boards), per `fabrication/README.md`.<br>Either way, holes will be revised. | [09](sections/09_erc_drc_fab_outputs.md) | | |
| HMI-02  | Three ESP32-S3 strapping pins on the expansion header behind only 33 ohm resistors *(was HIGH)* | confirmed-with-corrections | Add 4.7-10 kohm pull-downs to GND on GPIO45 and GPIO46 close to U4 so they are robust against a 10 kohm external pull-up. Add a loud 'GPIO45/46 must be low at reset' warning to the header documentation and silkscreen. Longer term, prefer non-strapping pins on the header. | I don't want to have any more interference for potential signals that make use of GPIO45/46/3. If you think they'll help avoid strapping conditions while also not affecting potential I2S signals, then good for me. Valid, but still explain. | [08](sections/08_buttons_rtc_touch_expansion.md) | | |
| HMI-03  | DS3231MZ has no backup cell, so the clock does not survive power loss | confirmed | Either (a) accept and document clearly that the RTC gives accuracy while powered only, or (b) next spin move 3V3 to VCC and put a CR1225 or supercap on VBAT, which is what the part is designed for. Firmware must in any case check the oscillator-stop flag rather than assume valid time at first power-up. | Intentional. Battery runs out -> time lost. Big whoop. I'm not putting a coin cell in. | [08](sections/08_buttons_rtc_touch_expansion.md) | | |
| HMI-04  | RTC INT/SQW is unrouted, so the DS3231's alarms cannot wake the MCU | confirmed | Route INT/SQW to a free RTC-capable GPIO (IO0-IO21) with a 10-100 kohm pull-up to 3V3, or state plainly in the firmware-interface docs that RTC alarms are unavailable. | Doesn't need to. I'm not making an alarm clock. | [08](sections/08_buttons_rtc_touch_expansion.md) | | |
| HMI-07  | Mutually exclusive 0 ohm option pairs are unmarked; R73+R74 both fitted shorts 3V3 to GND | confirmed-with-corrections | Make R74 100 ohm instead of 0 ohm: a both-fitted mistake then draws 33 mA instead of shorting the rail, and the power-button divider still reads 2.99 V. For the touch pairs make the TP_INT-side jumpers R43 and R44 100 ohm - NOT R42/R66, which carry the panel's VDD and must stay 0 ohm (100 ohm against a ~20 mA touch controller w… | **PARTLY DISPUTED.** R72 and R74 are DNP and are not placed, so the R73 + R74 short cannot occur in the standard build. Making R74 100 ohm is reasonable hardening for a later revision, not a current defect. The importer-merge case behind it was seen only at NextPCB and is handled by omitting DNP lines there. | [08](sections/08_buttons_rtc_touch_expansion.md) | | |
| HMI-10  | Bottom-edge buttons sit ~1.0 mm closer to the board edge than the side buttons | confirmed | Confirm against a physical MJTP1117 before cutting an enclosure. If the difference is not deliberate, move the bottom row about 0.96 mm inboard (pads y 146.45 -> 145.49) so all eight actuators share one standoff and the case can use a single bezel depth. | Bottom edge buttons not going to be actuated the same as the side edge. Intention of bottom edge buttons is for case to have mechanism to accept vertical presses, translating the force horizontal. | [08](sections/08_buttons_rtc_touch_expansion.md) | | |
| HMI-V01 | R72/R74 are flagged dnp but not exclude_from_bom, so the rail-shorting jumper survives into BOM exports | added-by-verifier | Set exclude_from_bom on R72 and R74 so all six DNP jumpers are handled identically and no exporter can leak them. That moves the mitigation out of one fab's hand-edited BOM and into the schematic itself. Combine with HMI-07's suggestion to make R74 100 ohm rather than 0 ohm, so that even a both-fitted board draws 33 mA instead … | **PARTLY DISPUTED.** Valid hardening (set exclude-from-BOM on R72, R74 and SW6 for the next revision), but there is no exposure in the JLC upload: in `bom_JLC_upload_v4_optimized.csv` these parts have their own lines with an empty part-number cell and are absent from `positions.csv`. See FAB-17. | [08](sections/08_buttons_rtc_touch_expansion.md) | | |
| HMI-V02 | The silkscreened "cut the long end" option has a ~1.9 mm cut window bounded by the battery connector, and no cut line is drawn | added-by-verifier | Draw a dashed cut line on the silkscreen at y = 62.0 mm with a 'cut here' label - it costs nothing before ordering and turns a guess into an instruction. Add a note that the cut also removes mounting hole H1, so the enclosure must not depend on it. The existing R36/R73-out, R72/R74-in electrical instruction is correct and needs… | Silkscreen line is drawn. And instructions for battery ejection will be documented. | [08](sections/08_buttons_rtc_touch_expansion.md) | | |
| HMI-V03 | MJTP1117 is APEM's grounding variant, yet every switch cover is left floating - and the I2C bus passes 0.151 mm from two of those floating rings | added-by-verifier | Net pads 3 and 4 to GND on the four side switches (SW1, SW4, SW5, SW7) - they carry no front-mount tabs, so nothing breaks and finger ESD gets a drain path. Leave the bottom four netless for the front-mount option, but move I2C_SCL and I2C_SDA further from SW1's and SW4's rings on the next spin. This is a damage-in-normal-use i… | Footprint came this way. Can adjust if recommended. But don't know the benefit. Weigh. | [08](sections/08_buttons_rtc_touch_expansion.md) | | |
| LAY-02  | The documented tongue cut line leaves 12.3 mm of solid 1.6 mm FR-4 and cannot be snapped by hand | confirmed | Either commit to a real break-away (a mouse-bite drill row on ~1 mm pitch, or a V-score) or relabel the dashed line as 'cut with a saw'. Add a printable warning that the cut severs P+, 3V3 and GND and must be deburred, and note that the power button SW10 at (101.8,54.8) goes with the tongue. | Not meant to be hand cut. dremel or other crude method. | [10](sections/10_layout_area_walk.md) | | |
| LAY-04  | Essentially all silkscreen on the board is below the fab's minimum printable size, including the battery polarity mark *(was HIGH)* | confirmed-with-corrections | Raise all reference designators to >= 0.8 mm height / 0.15 mm stroke (1.0 mm / 0.15 mm to be safe) and every board note to >= 1.0 mm / 0.15 mm. Prioritise two items: the J5 polarity mark (a LiPo safety marking that currently may not print at all) and the tongue-cut instructions, which are the board's key user procedure and exis… | Haven't been told no... ignore for now. | [10](sections/10_layout_area_walk.md) | | |
| LAY-05  | B.Cu ground is fragmented into 50 fill areas, 14 of them with no via to the F.Cu plane *(was HIGH)* | confirmed-with-corrections | Add GND stitching vias so every B.Cu island above ~20 mm2 has at least one tie to F.Cu -- at minimum in the bottom button strip, the SD area and around both converters. A dozen extra vias cost nothing and halve the return-path length for most of the 175 bottom-side parts. | false positive, all ground pours are stitched. | [10](sections/10_layout_area_walk.md) | | |
| LED-02  | External LED strings with low forward voltage are driven uncontrolled through L2 and U10's high-side body diode *(was HIGH)* | confirmed-with-corrections | Add a minimum string voltage to the silkscreen text box and to docs/HARDWARE.md section 7 - e.g. 'at least 3 LEDs in series (Vf > 6 V)' - next to the existing 22 V maximum. No board change is needed; this is a guidance gap with a real component-damage consequence. | Valid, yes. | [07](sections/07_led_frontlight_driver.md) | | |
| LED-12  | J3 pin mapping to the Good Display front-light flex is unverified from any primary source | confirmed-with-corrections | Make this a bring-up gate rather than a board change: before first power-on with any new panel lot, diode-test the flex or the J3 mating pads with a meter (or probe TP3/TP4/TP5) and confirm pins 1 and 5 are the anodes. Record the FPC revision with the result. I could not verify this myself and am reporting it at low confidence.  | **PARTLY DISPUTED.** Your own section 9.3 notes that the earlier audit holds a measured physical sample of the front-light flex. Agree that no primary document confirms the pin map and that a bring-up diode test is sensible. | [07](sections/07_led_frontlight_driver.md) | | |
| LED-14  | The on-board dimming note (10-25 kHz) cannot enable the driver: ADIM doubles as the enable and needs a >40 us first pulse | confirmed | Firmware must emit an explicit enable pulse (>=100 us HIGH for margin) before applying the dimming carrier. Add that one sentence to the schematic design-note text box, since that box is the first thing someone replicating the board reads. Symptom if missed is 'the front light never comes on', which is an expensive way to lose … | Confirm with datasheet. Can put in for instruction in firmware. | [07](sections/07_led_frontlight_driver.md) | | |
| LED-V02 | Open-load OVP latches after three trips - re-applying the PWM carrier will not restart the driver, and nothing on the board or in the docs says so | added-by-verifier | Make the firmware's front-light enable a fixed three-step sequence and put it in the schematic design-note text box and docs/HARDWARE.md: (1) PWM_LED LOW for >=3 ms to clear any latched OVP; (2) a single HIGH pulse >=100 us to satisfy tADIM_EN = 40 us with margin; (3) start the 10-25 kHz dimming carrier. No board change. | OVP should not trip at all if software effectively monitors via LED_MONIT. OVP case is worst case, but you're right should be documented. | [07](sections/07_led_frontlight_driver.md) | | |
| MCU-01  | BOOT button SW6 is DNP — no fitted way into download mode when USB-Serial/JTAG is unavailable *(was HIGH)* | confirmed-with-corrections | Fit SW6 (APEM MJTP1243 or equivalent 6 x 3.5 x 4.3 mm THT tactile) on every prototype. The land is already on the board and the part costs cents. Until then, note that recovery means shorting SW6 pad 2 to GND with tweezers while pressing SW11. | DNP for cost reasons, tweezers recommended. | [04](sections/04_esp32_core_gpio_map.md) | | |
| MCU-13  | Sibling firmware's DE_LINK profile and delink build env do not match this PCB at all *(was HIGH)* | confirmed-with-corrections | Do not flash the stock 'delink' build onto this board. Create a new BoardProfile with this board's pin map and a new PlatformIO env with board_build.arduino.memory_type = qio_opi (quad flash + octal PSRAM). The existing 33 ohm series resistors are what would keep a mis-flash from destroying pins — keep them. | de-link firmware will not relate entirely to this prototype. ignore. | [04](sections/04_esp32_core_gpio_map.md) | | |
| MCU-14  | Metal and copper within ~1 mm of the module's PCB antenna on both flanks | confirmed-with-corrections | Accept for this prototype but MEASURE RSSI and throughput before blaming firmware. If range disappoints, move SW5 a few mm toward the SD socket and R4 out of the antenna's flank in the next spin, and move L2 (a switching node) further from the antenna. | Not able to completely satisfy this while keeping low profile. We've done what we can. Accept this as potential risk for low speeds. | [04](sections/04_esp32_core_gpio_map.md) | | |
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
