iandchasse/silkscreen-pcb/docs/final-review-2026-09-19/REMAINING_PRUNED.md

# Remaining findings, pruned against the author's answers

Scope: the 204 LOW / DOC / CERT-LATER findings and the 22 recovered ones — everything you have **not** yet answered in `FINDINGS_TABLE_author_refute.md`.
Each was read against the answers you gave to the HIGH and MEDIUM rows. **Only the first table needs you.**

## Still open — a one-line answer closes each (17)
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
