iandchasse/silkscreen-pcb/docs/audit-2026-09-16/eink-loop.png

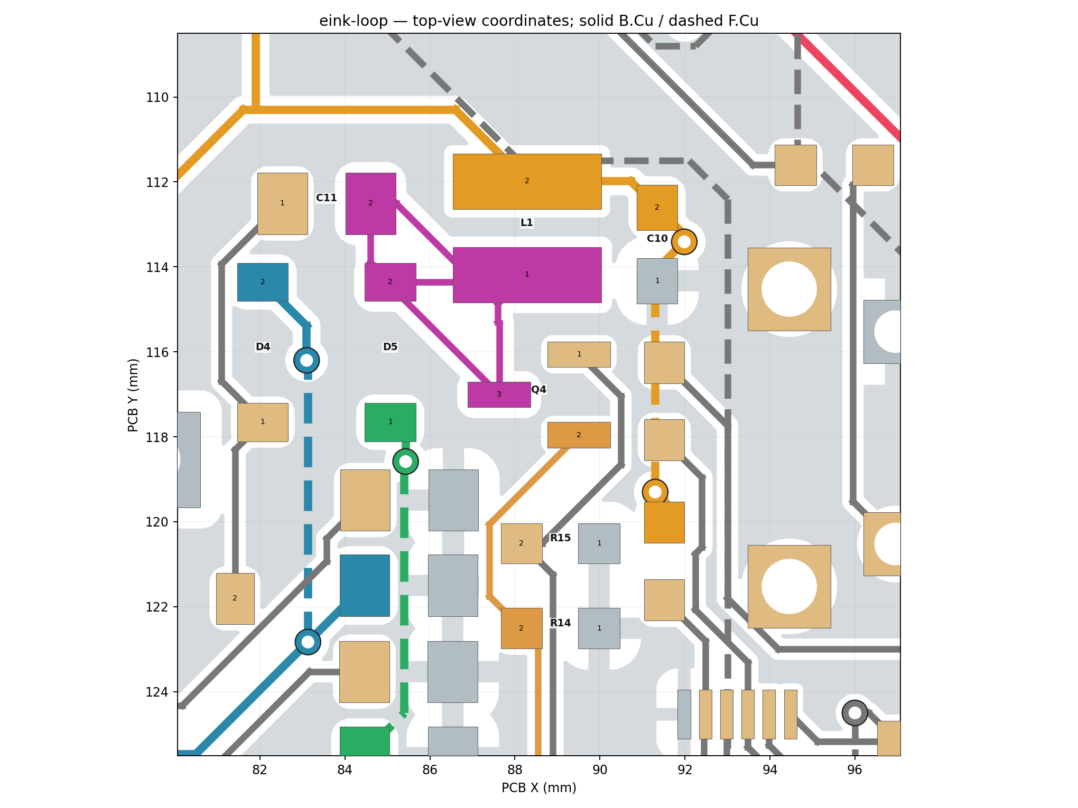
docs/audit-2026-09-16/eink-loop.png
