iandchasse/silkscreen-pcb/docs/audit-2026-09-16/led-loop.png

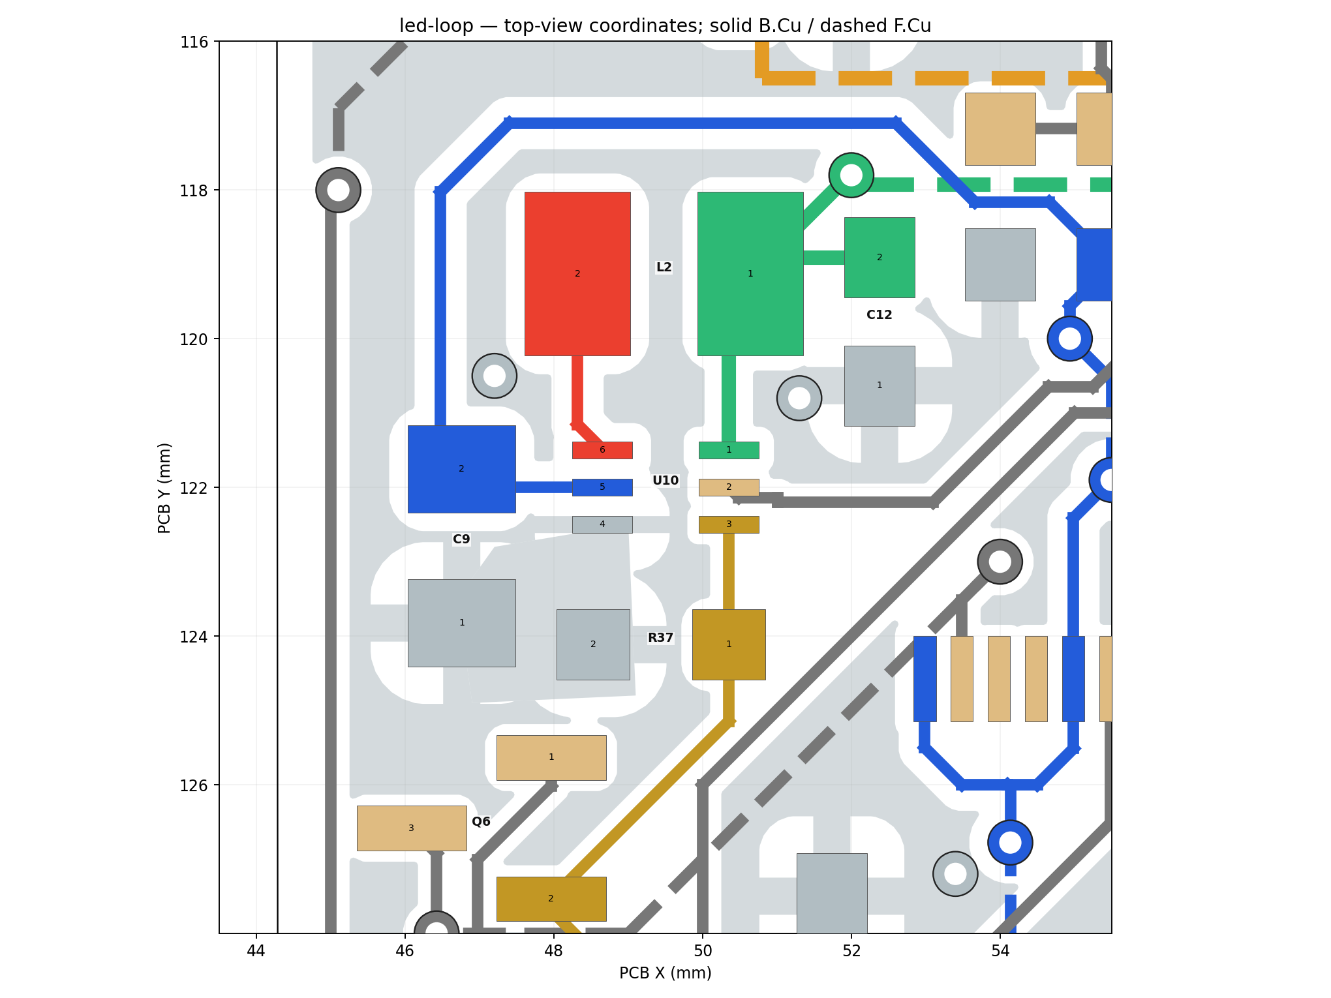
docs/audit-2026-09-16/led-loop.png
