iandchasse/silkscreen-pcb/docs/audit-2026-09-16/power-path.png

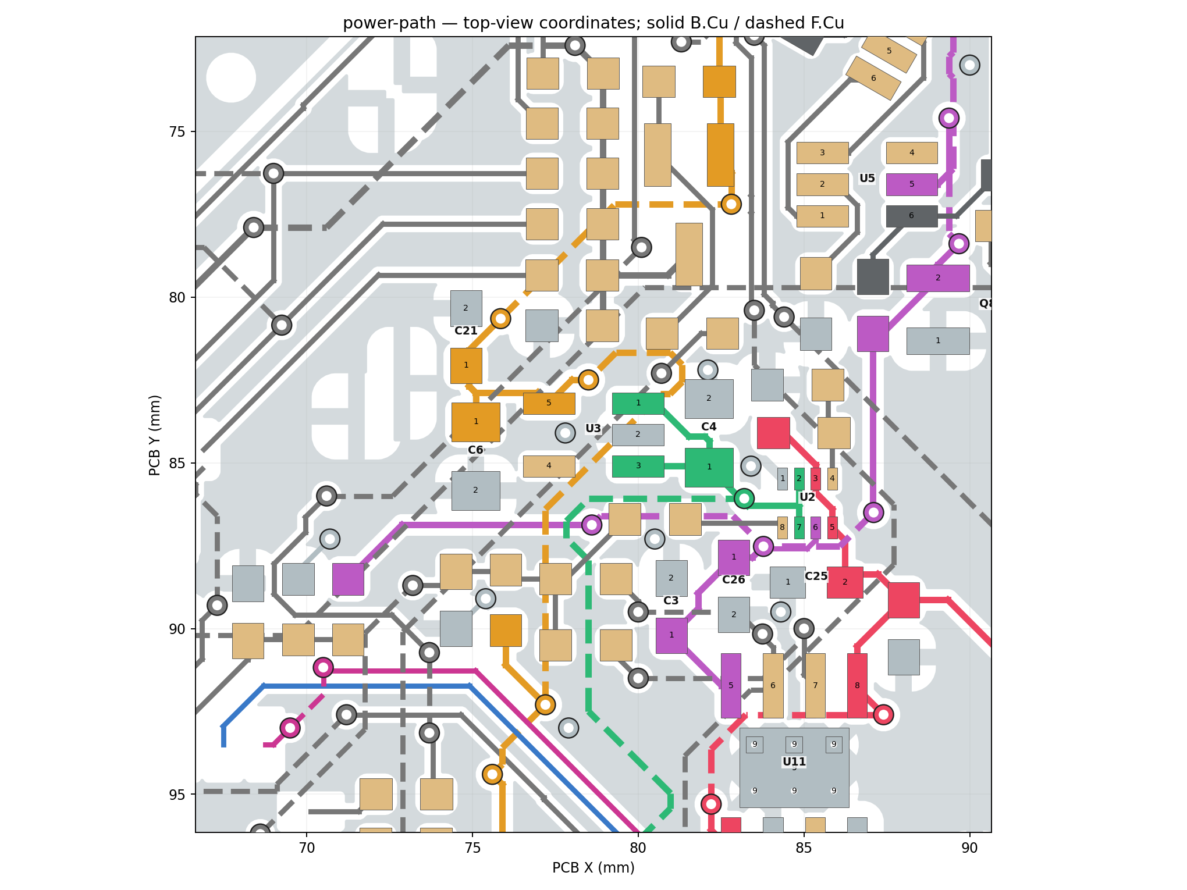
docs/audit-2026-09-16/power-path.png
