iandchasse/silkscreen-pcb/docs/audit-2026-09-16/sd-footprint.png

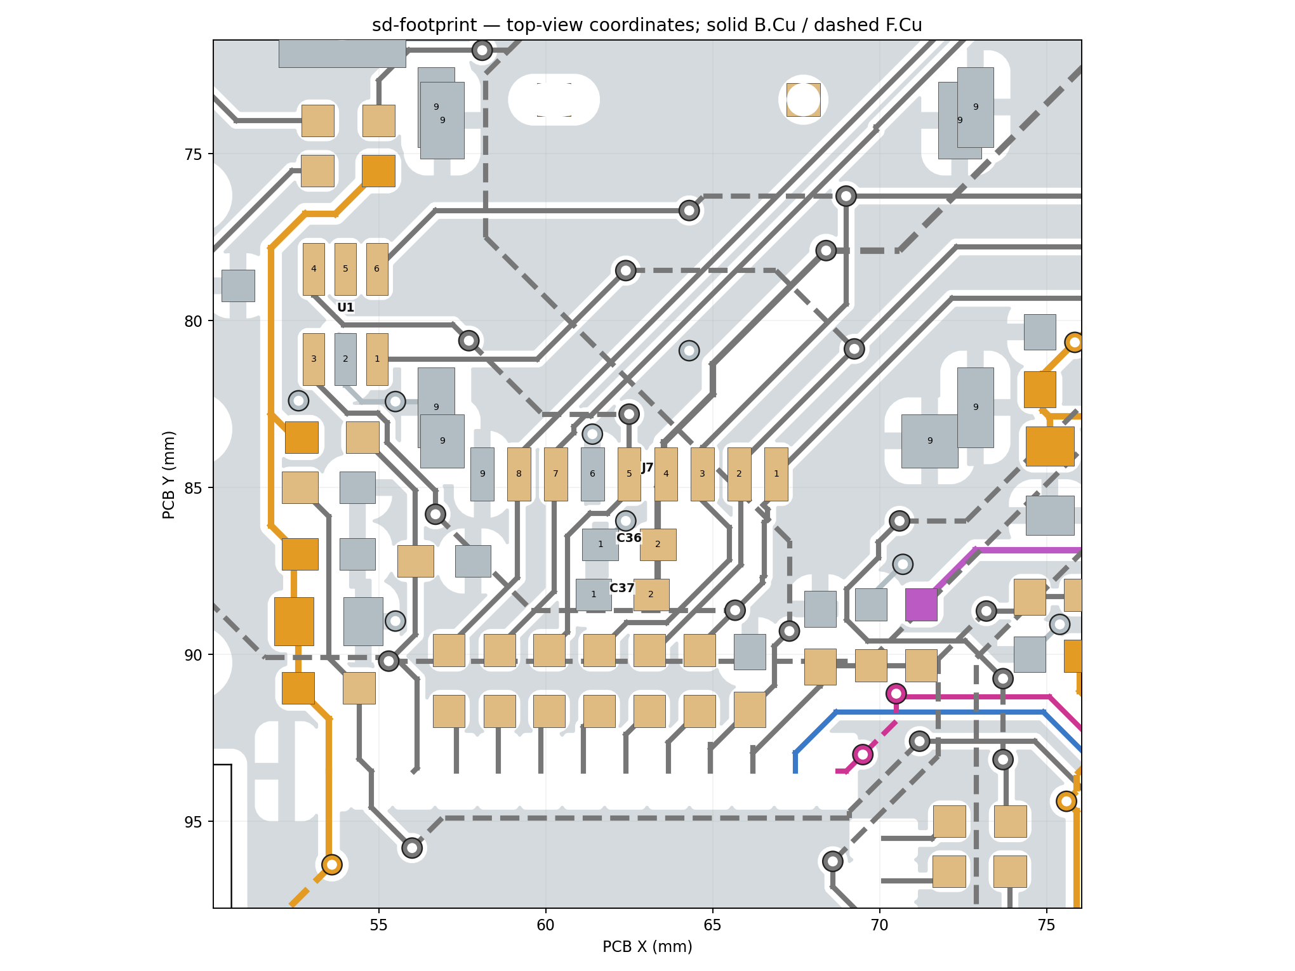
docs/audit-2026-09-16/sd-footprint.png
