iandchasse/silkscreen-pcb/docs/audit-2026-09-16/silkscreen_pcb_layout.pdf-1.png

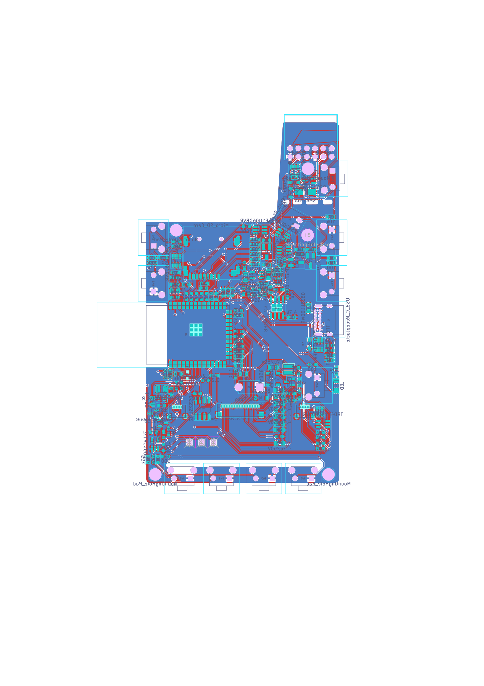
docs/audit-2026-09-16/silkscreen_pcb_layout.pdf-1.png
