iandchasse/silkscreen-pcb/docs/audit-2026-09-16/usb-path.png

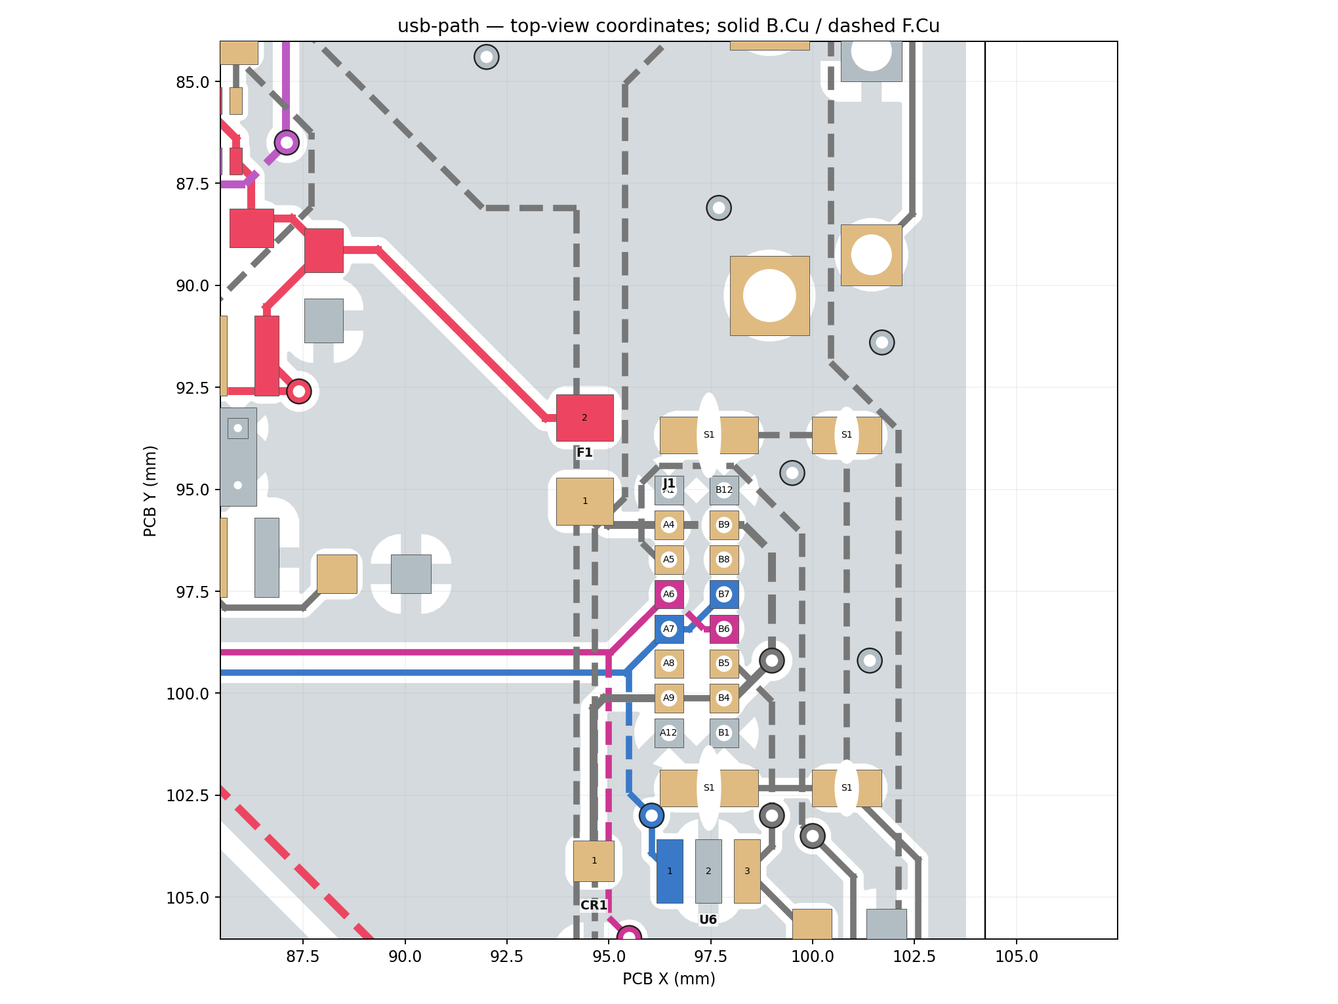
docs/audit-2026-09-16/usb-path.png
