iandchasse/silkscreen-pcb/docs/audit-2026-09-16/whole-board.png

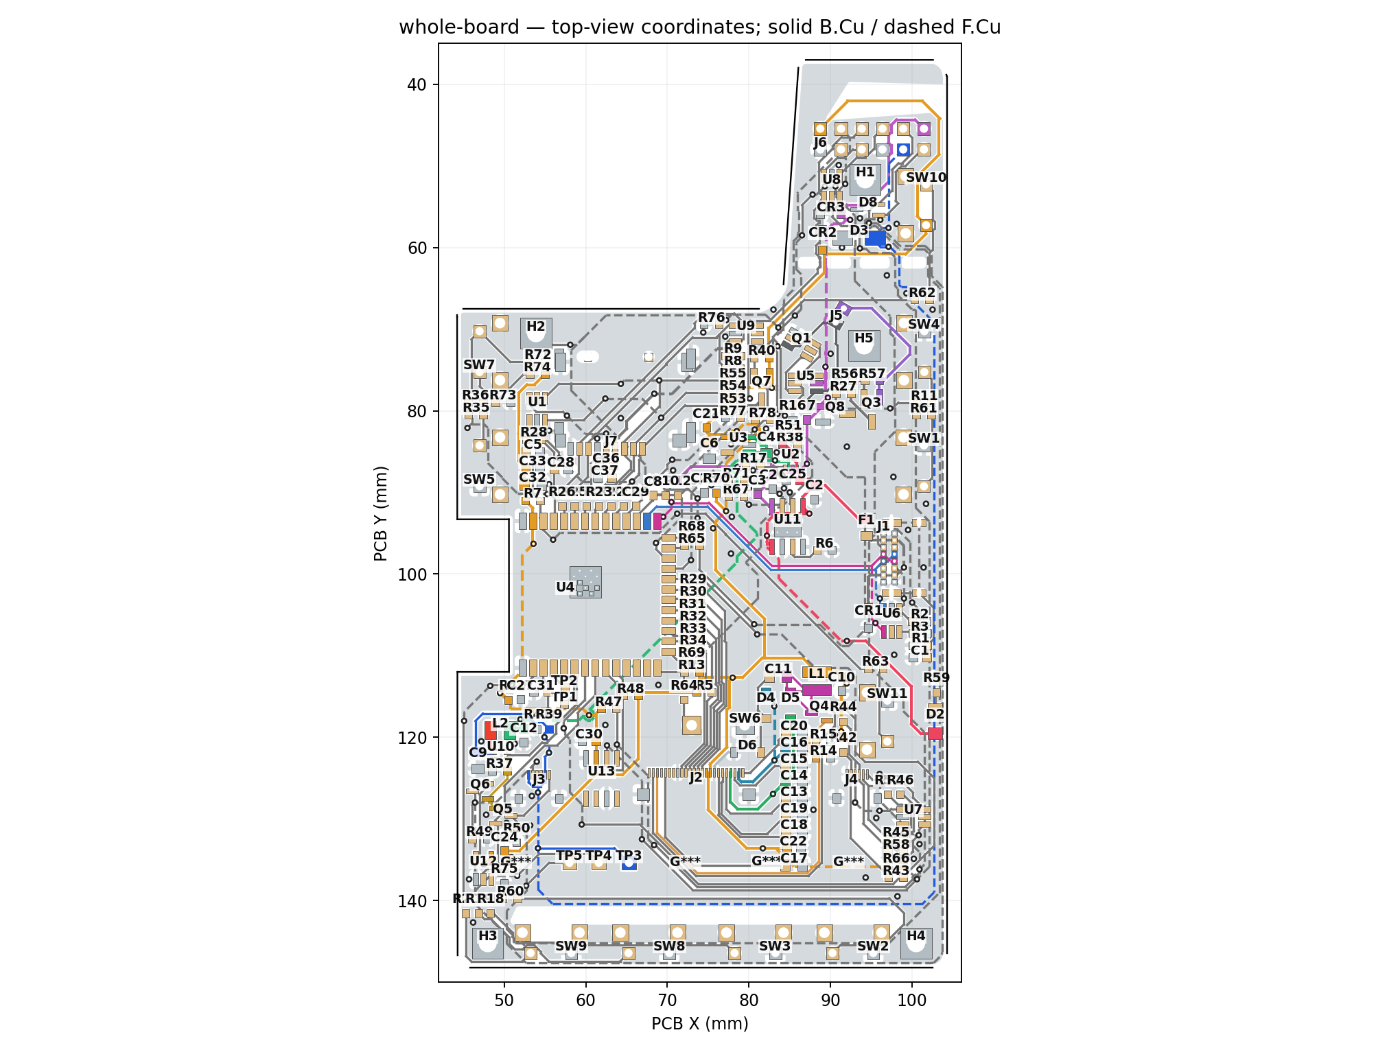
docs/audit-2026-09-16/whole-board.png
