iandchasse/silkscreen-pcb/docs/final-review-2026-09-19/sections/img/battery_j5_silk.png

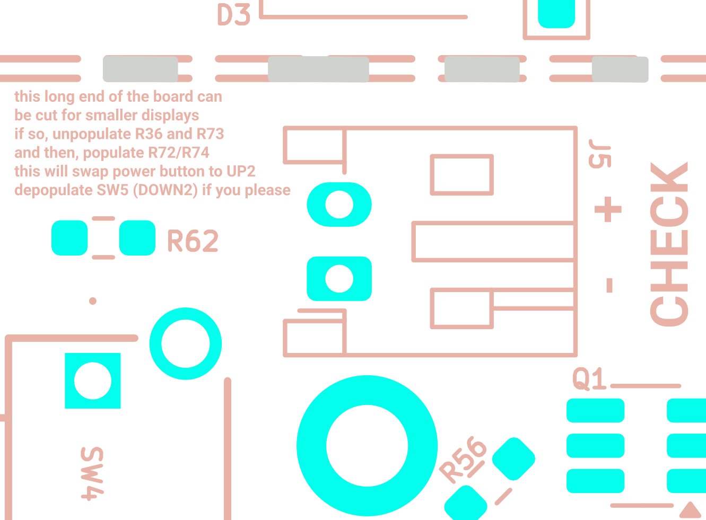
docs/final-review-2026-09-19/sections/img/battery_j5_silk.png
