iandchasse/silkscreen-pcb/docs/final-review-2026-09-19/sections/img/battery_prot_layout.png

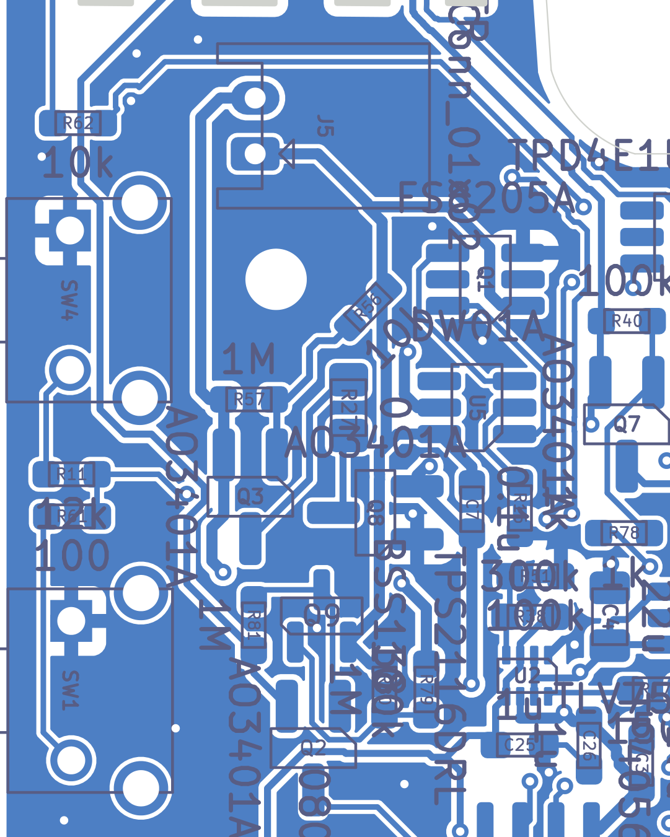
docs/final-review-2026-09-19/sections/img/battery_prot_layout.png
