iandchasse/silkscreen-pcb/docs/final-review-2026-09-19/sections/img/epd_connector_slot.png

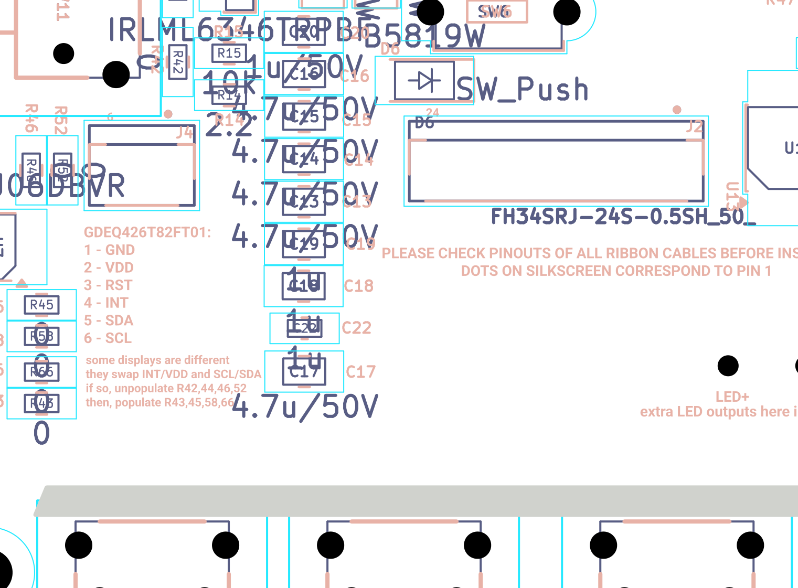
docs/final-review-2026-09-19/sections/img/epd_connector_slot.png
