iandchasse/silkscreen-pcb/docs/final-review-2026-09-19/sections/img/hmi_button_row_copper.png

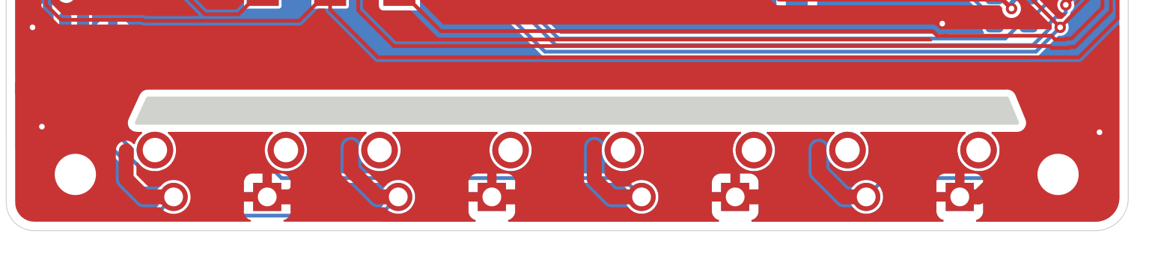
docs/final-review-2026-09-19/sections/img/hmi_button_row_copper.png
