iandchasse/silkscreen-pcb/docs/final-review-2026-09-19/sections/img/hmi_j6_esd_cluster.png

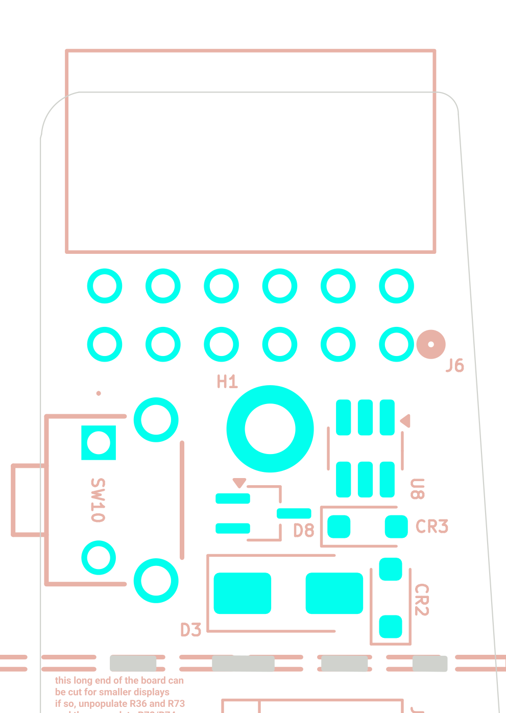
docs/final-review-2026-09-19/sections/img/hmi_j6_esd_cluster.png
