iandchasse/silkscreen-pcb/docs/final-review-2026-09-19/sections/img/hmi_top_button_lands.png

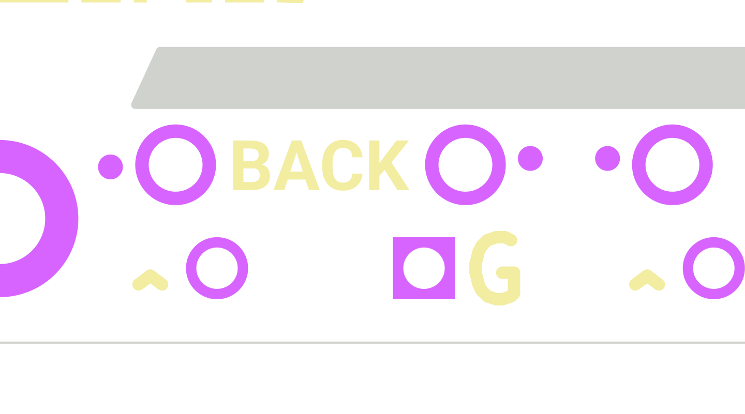
docs/final-review-2026-09-19/sections/img/hmi_top_button_lands.png
