iandchasse/silkscreen-pcb/docs/final-review-2026-09-19/sections/img/hmi_touch_connector_mux.png

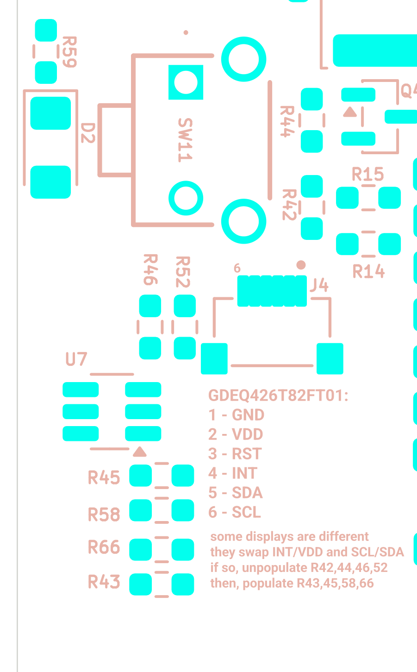
docs/final-review-2026-09-19/sections/img/hmi_touch_connector_mux.png
