iandchasse/silkscreen-pcb/docs/final-review-2026-09-19/sections/img/layout_bottom_strip.png

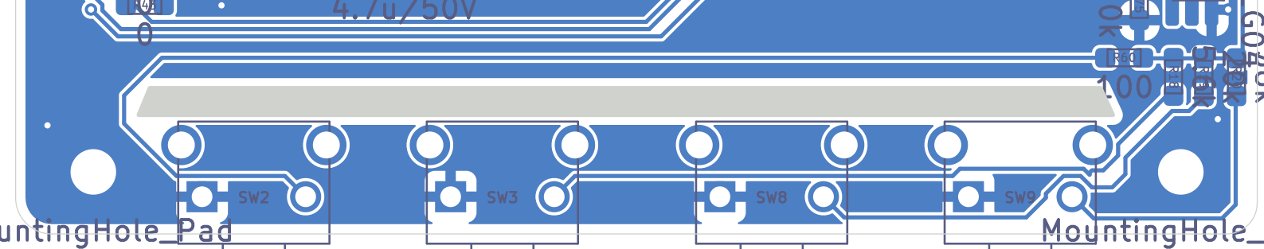
docs/final-review-2026-09-19/sections/img/layout_bottom_strip.png
