iandchasse/silkscreen-pcb/docs/final-review-2026-09-19/sections/img/layout_silk_legibility.png

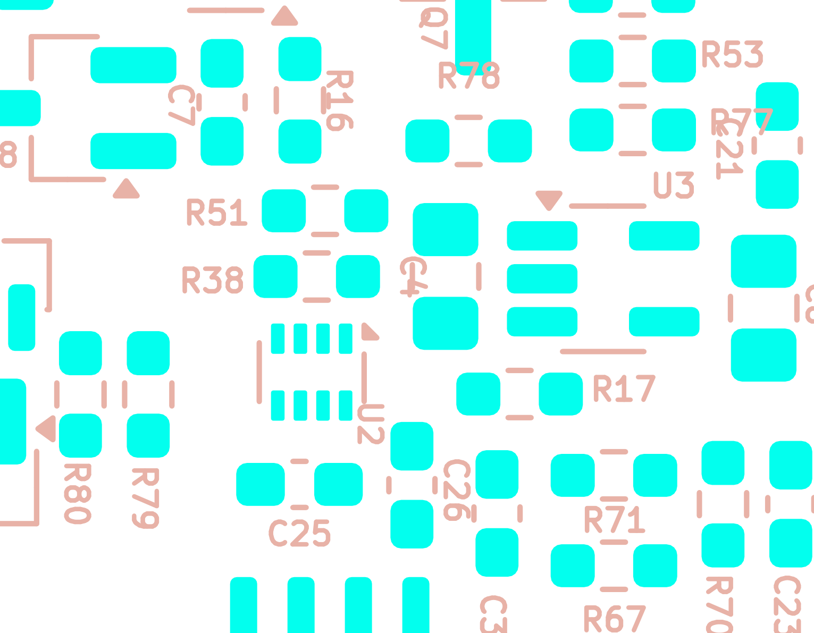
docs/final-review-2026-09-19/sections/img/layout_silk_legibility.png
