iandchasse/silkscreen-pcb/docs/final-review-2026-09-19/sections/img/led_j6_silk_labels.png

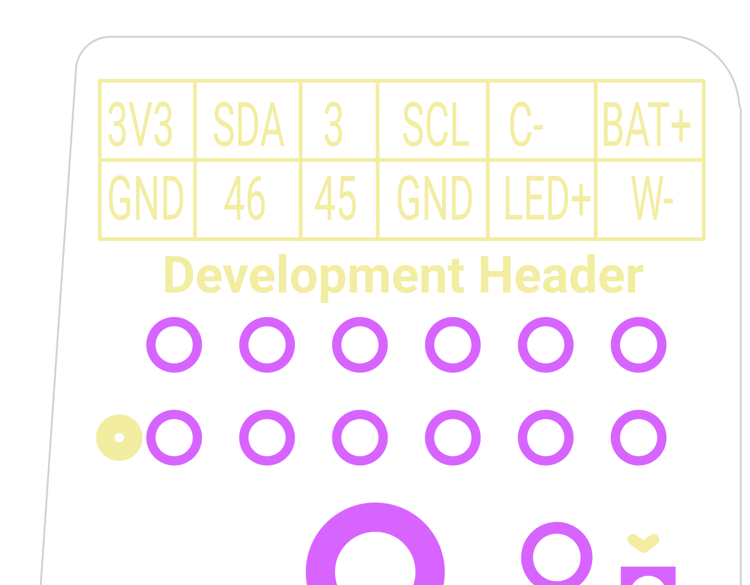
docs/final-review-2026-09-19/sections/img/led_j6_silk_labels.png
