iandchasse/silkscreen-pcb/docs/final-review-2026-09-19/sections/img/mcu_antenna_keepout.png

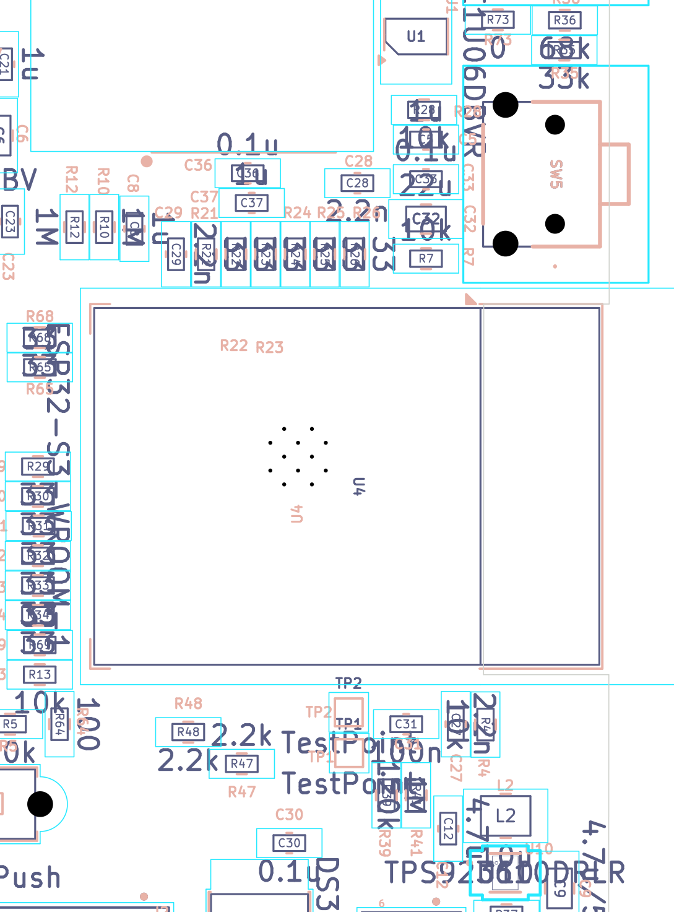
docs/final-review-2026-09-19/sections/img/mcu_antenna_keepout.png
