iandchasse/silkscreen-pcb/docs/final-review-2026-09-19/sections/img/power_3v3_trunk_xray.png

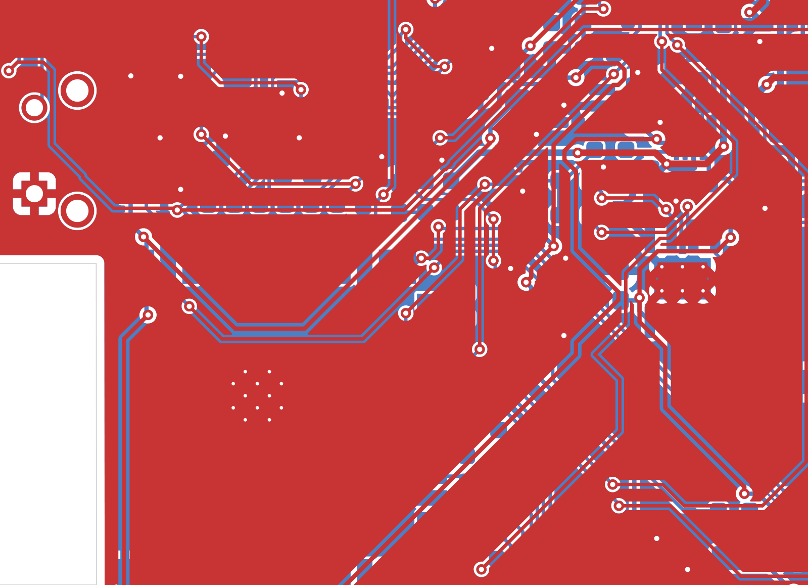
docs/final-review-2026-09-19/sections/img/power_3v3_trunk_xray.png
