iandchasse/silkscreen-pcb/docs/final-review-2026-09-19/sections/img/rules_bottom_edge_dangling.png

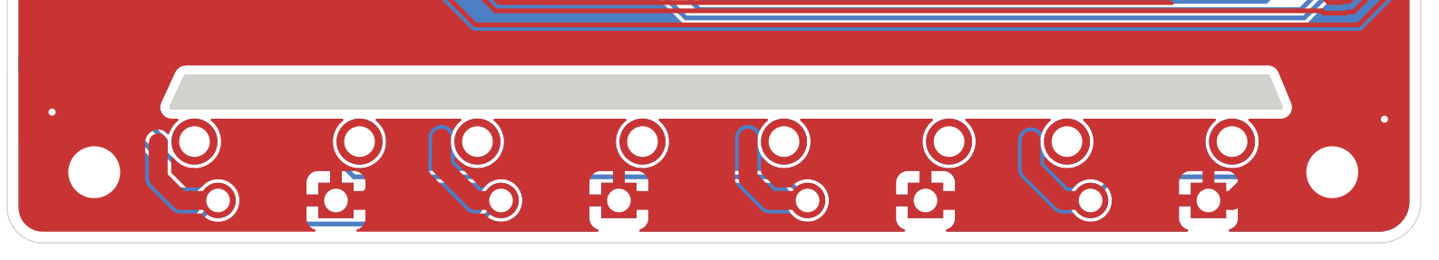
docs/final-review-2026-09-19/sections/img/rules_bottom_edge_dangling.png
