iandchasse/silkscreen-pcb/docs/final-review-2026-09-19/sections/img/rules_j1_usbc_pads.png

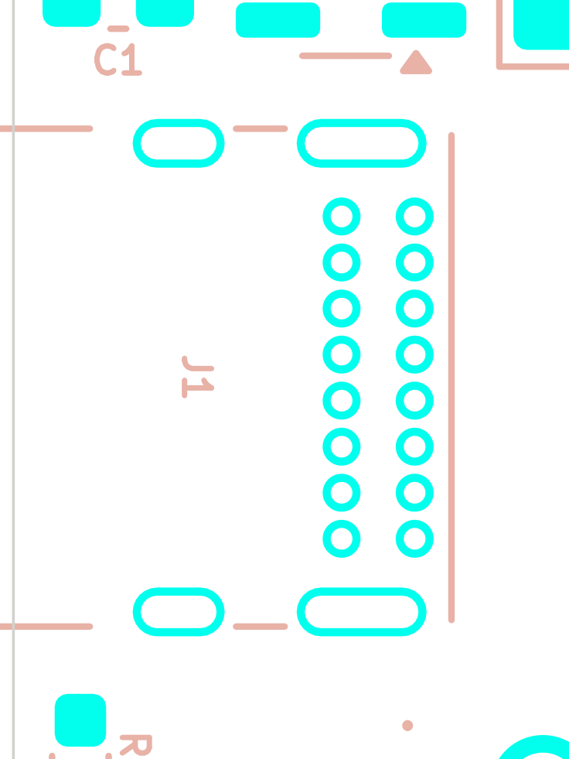
docs/final-review-2026-09-19/sections/img/rules_j1_usbc_pads.png
