iandchasse/silkscreen-pcb/docs/final-review-2026-09-19/sections/img/rules_j2_fpc_maskdam.png

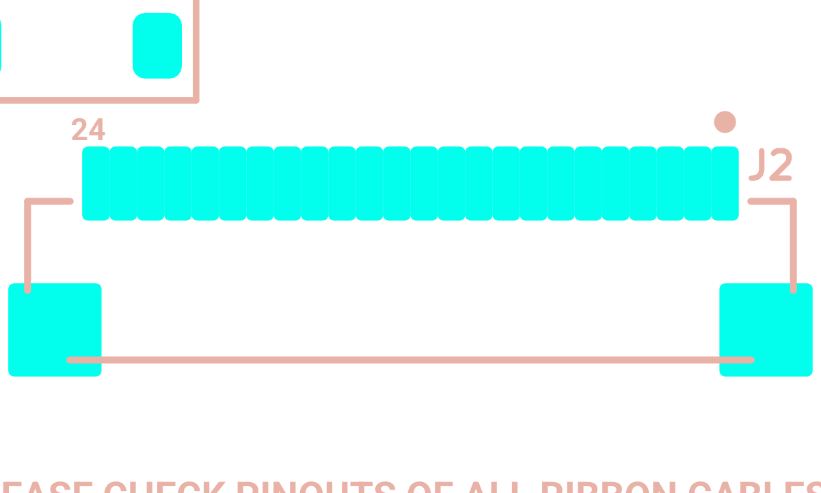
docs/final-review-2026-09-19/sections/img/rules_j2_fpc_maskdam.png
