iandchasse/silkscreen-pcb/docs/final-review-2026-09-19/sections/img/sd_return_path.png

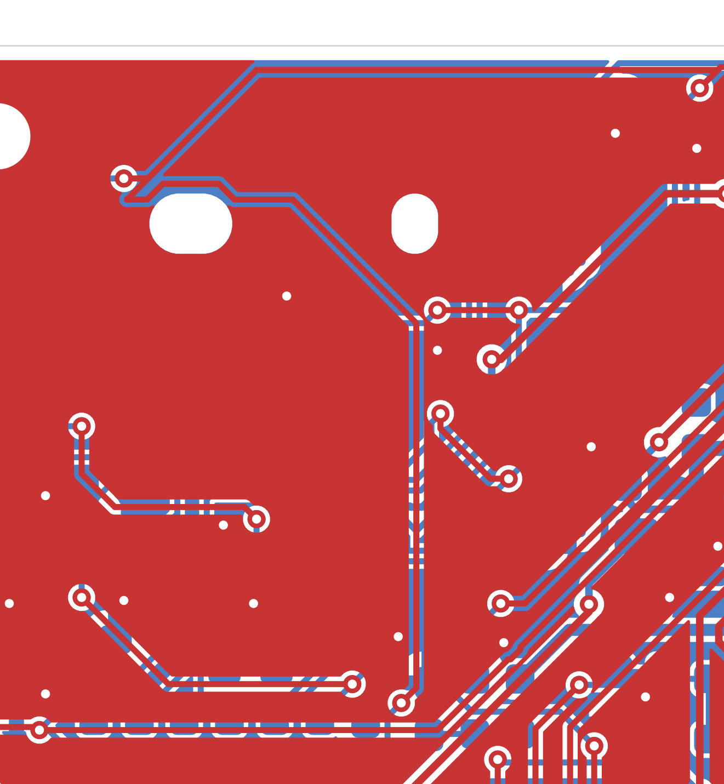
docs/final-review-2026-09-19/sections/img/sd_return_path.png
