iandchasse/silkscreen-pcb/docs/final-review-2026-09-19/sections/img/sd_xray.png

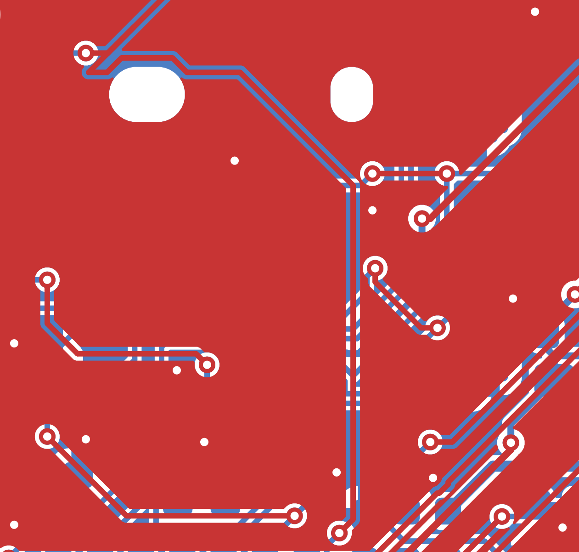
docs/final-review-2026-09-19/sections/img/sd_xray.png
