iandchasse/silkscreen-pcb/docs/final-review-2026-09-19/sections/img/usb_inlet_bottom_copper.png

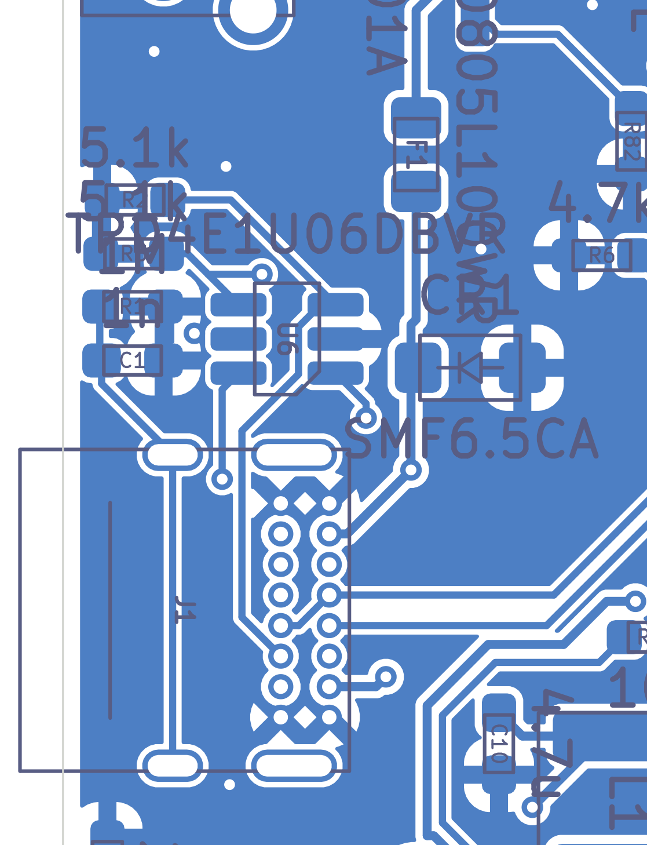
docs/final-review-2026-09-19/sections/img/usb_inlet_bottom_copper.png
