iandchasse/silkscreen-pcb/docs/final-review-2026-09-19/sections/img/usb_j1_area.png

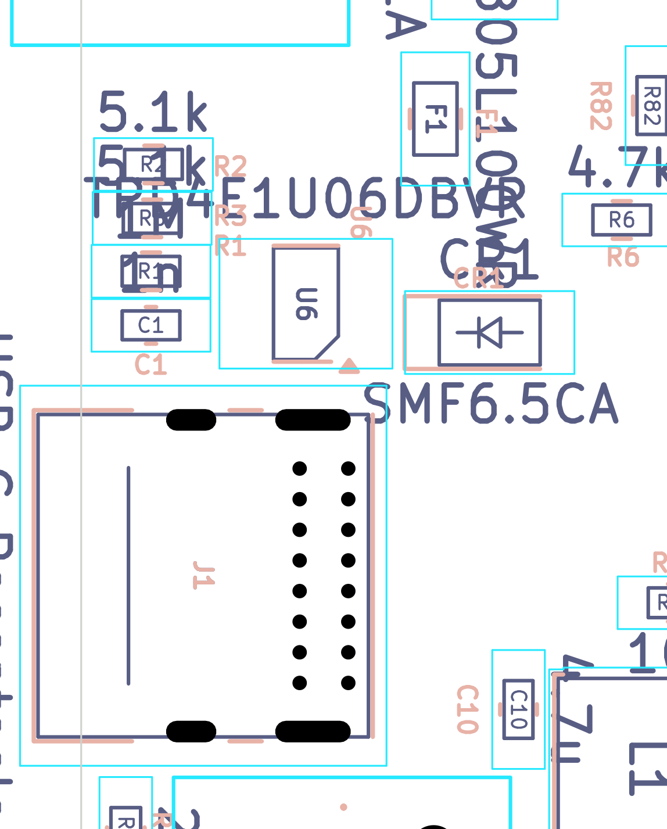
docs/final-review-2026-09-19/sections/img/usb_j1_area.png
