iandchasse/silkscreen-pcb/docs/final-review-2026-09-19/sections/img/usb_mux_and_status_ladder.png

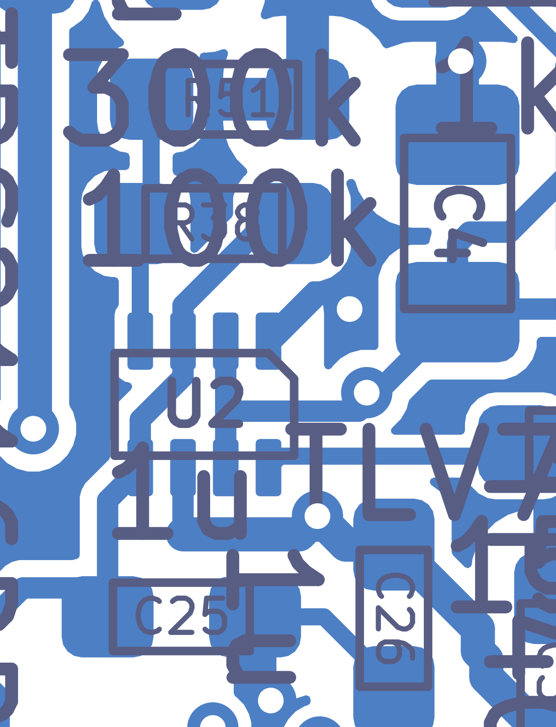
docs/final-review-2026-09-19/sections/img/usb_mux_and_status_ladder.png
