iandchasse/silkscreen-pcb/docs/final-review-2026-09-19/sections/img/usb_mux_area.png

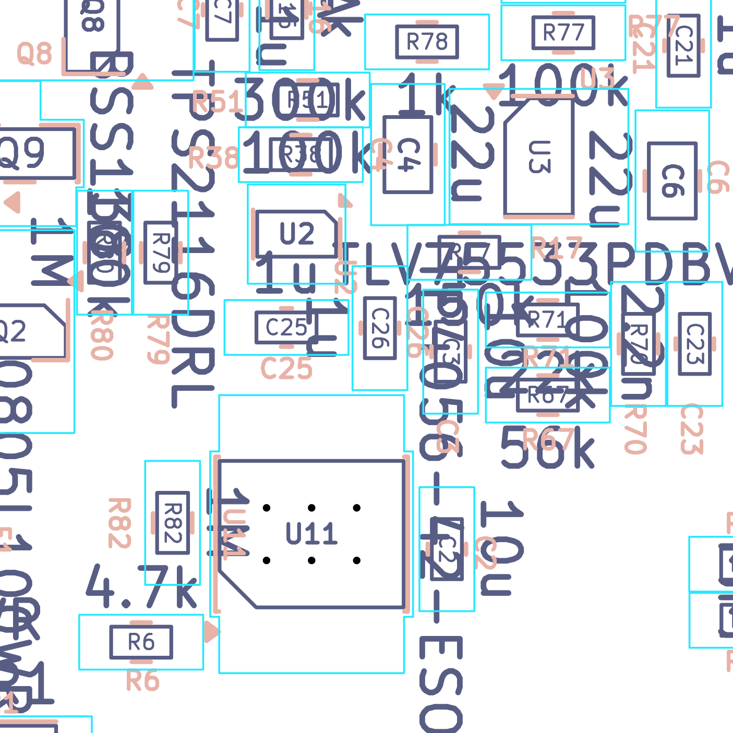
docs/final-review-2026-09-19/sections/img/usb_mux_area.png
