iandchasse/silkscreen-pcb/docs/audit-2026-09-18/checkpoint-2/live_cost.txt

C1588 1 CL10B102KB8NNNC base  stock 8986576 0603
C19666 2 CL10A475KO8NNNC base  stock 3112953 0603
C513770 7 CS2012X5R475K500NRE expand  stock 208320 0805
C28323 3 CL21B105KBFNNNE base  stock 2962887 0805
C19702 2 CL10A106KP8NNNC base  stock 12127625 0603
C15849 7 CL10A105KB8NNNC base  stock 7052997 0603
C1604 4 0603B222K500NT base  stock 1272903 0603
C14663 6 CC0603KRX7R9BB104 base  stock 52391718 0603
C20416420 3 TCC0805X5R226M250FT expand  stock 96183 0805
C19077501 1 SMF6.5CA expand pref stock 1745835 SOD-123FL
C5299440 2 SD05C-01FTG expand  stock 98762 SOD-323
C28310439 1 YLED1206R expand  stock 102108 1206
C19077543 1 SMAJ26A expand pref stock 41560 DO-214AC(SMA)
C8598 3 B5819W SL base  stock 491524 SOD-123
C42370512 1 PESD2IVN-UX expand  stock 2955 SOT-323
C269106 1 SMD0805B100TFT expand  stock 12962 0805
C7095263 1 USB4085-GF-A expand  stock 4364 Plugin
C324726 1 FH34SRJ-24S-0.5SH(50) expand  stock 10597 SMD,P=0.5mm,Surface Mount，Right Angle
C224194 2 FH34SRJ-6S-0.5SH(50) expand  stock 110798 SMD,P=0.5mm,Surface Mount，Right Angle
C48579993 1 A2001WR-2P expand  stock 8805 Push-Pull,P=2mm
C5333437 1 A2541HWR-2x6P expand  stock 1278 Push-Pull,P=2.54mm
C393941 1 TF PUSH expand  stock 201455 SMD
C206267 1 SLW5040S470MST expand  stock 1949 SMD,5x5mm
C88532 1 VLS252012HBX-100M-1 expand  stock 19963 SMD,2.5x2mm
C2830320 1 FS8205A expand  stock 71515 SOT-23-6
C15127 4 AO3401A base  stock 403350 SOT-23
C67276 1 IRLML6346TRPBF expand  stock 5503 SOT-23
C7420339 3 BSS138 expand pref stock 133792 SOT-23
C22935 10 0603WAF1004T5E base  stock 7284358 0603
C22790 1 0603WAF1202T5E base  stock 1395297 0603
C25804 13 0603WAF1002T5E base  stock 22373597 0603
C112307 1 RC0603FR-072R2L expand  stock 94913 0603
C21190 2 0603WAF1001T5E base  stock 22805270 0603
C22807 1 0603WAF1503T5E base  stock 785223 0603
C23189 1 0603WAF5601T5E base  stock 1236466 0603
C4184 1 0603WAF2002T5E base  stock 6778939 0603
C23186 2 0603WAF5101T5E base  stock 22349781 0603
C23206 2 0603WAF5602T5E base  stock 1067409 0603
C23140 15 0603WAF330JT5E base  stock 5119095 0603
C21189 6 0603WAF0000T5E base  stock 17072385 0603
C4216 1 0603WAF3302T5E base  stock 3078204 0603
C23231 1 0603WAF6802T5E base  stock 1233003 0603
C22810 1 0603WAF150JT5E expand pref stock 431232 0603
C23024 1 0603WAF3003T5E base  stock 654684 0603
C25803 7 0603WAF1003T5E base  stock 22656083 0603
C25808 1 0603WAF1203T5E base  stock 625951 0603
C4190 2 0603WAF2201T5E base  stock 5960884 0603
C22975 1 0603WAF2001T5E base  stock 15181495 0603
C23162 1 0603WAF4701T5E base  stock 24680139 0603
C22775 4 0603WAF1000T5E base  stock 12031424 0603
C31850 1 0603WAF2202T5E base  stock 3823319 0603
C557598 10 TS365ZJ expand  stock 17933 Plugin
C19829453 5 TPD4E1U06DBVR expand  stock 9048 SOT-23-6
C52919131 1 TPS923610DRLR expand  stock 189 SOT-563-6
C16581 1 TP4056-42-ESOP8 expand pref stock 90049 ESOP-8
C53185133 1 74LVC1G04GV expand  stock 5153 SOT-23-5
C107410 1 DS3231MZ+TRL expand  stock 12630 SOIC-8
C3235557 1 TPS2116DRLR expand  stock 48722 SOT-583
C404027 1 TLV75533PDBVR expand  stock 52539 SOT-23-5
C2913202 1 ESP32-S3-WROOM-1-N16R8 expand  stock 31340 SMD,25.5x18mm
C351410 1 DW01A expand  stock 122811 SOT-23-6L
C350879 - VLS3012HBX-220M expand  stock 6018 SMD,3x3mm
C22356394 - RCA033RFLF expand  stock 2817084 0603
extended (non-base, non-preferred) list: ['C513770', 'C20416420', 'C5299440', 'C28310439', 'C42370512', 'C269106', 'C7095263', 'C324726', 'C224194', 'C48579993', 'C5333437', 'C393941', 'C206267', 'C88532', 'C2830320', 'C67276', 'C112307', 'C557598', 'C19829453', 'C52919131', 'C53185133', 'C107410', 'C3235557', 'C404027', 'C2913202', 'C351410']
preferred-expand: ['C19077501', 'C19077543', 'C7420339', 'C22810', 'C16581']
5 boards: parts $127.13 ext 26 -> $33.23/board
10 boards: parts $188.00 ext 26 -> $22.70/board
30 boards: parts $448.35 ext 26 -> $16.25/board
100 boards: parts $1221.75 ext 26 -> $12.61/board
v4 reconstruction:
5 boards: parts $128.48 ext 26 -> $33.50/board
10 boards: parts $190.01 ext 26 -> $22.90/board
30 boards: parts $452.43 ext 26 -> $16.38/board
100 boards: parts $1232.71 ext 26 -> $12.72/board
