iandchasse/silkscreen-pcb/docs/final-review-2026-09-19/sections/img/power_power_strip_assembly.png

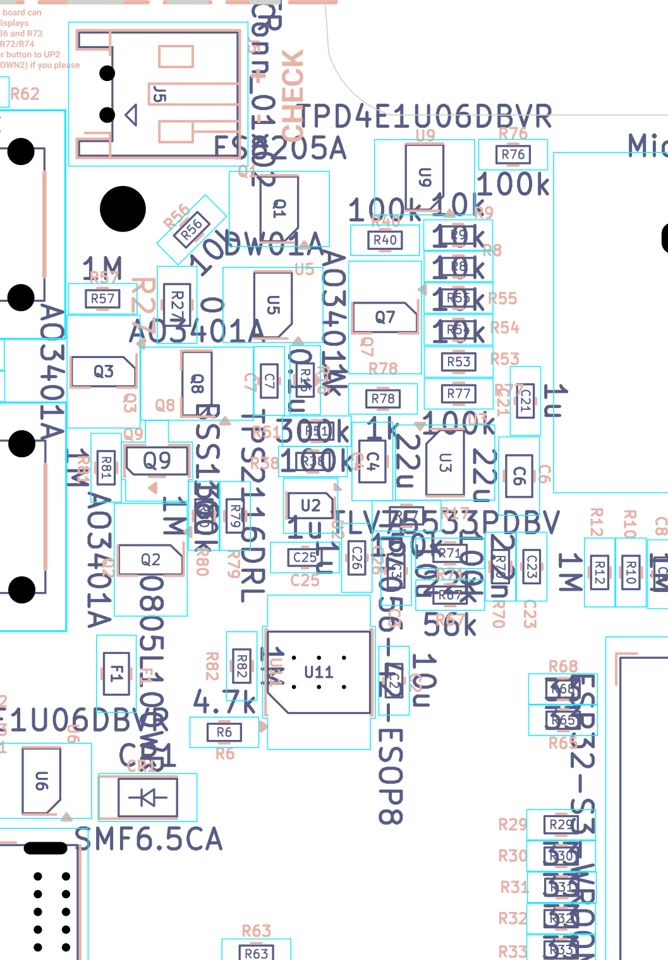
docs/final-review-2026-09-19/sections/img/power_power_strip_assembly.png
