iandchasse/silkscreen-pcb/docs/audit-2026-09-16/ldo-thermal-benchmarks.png

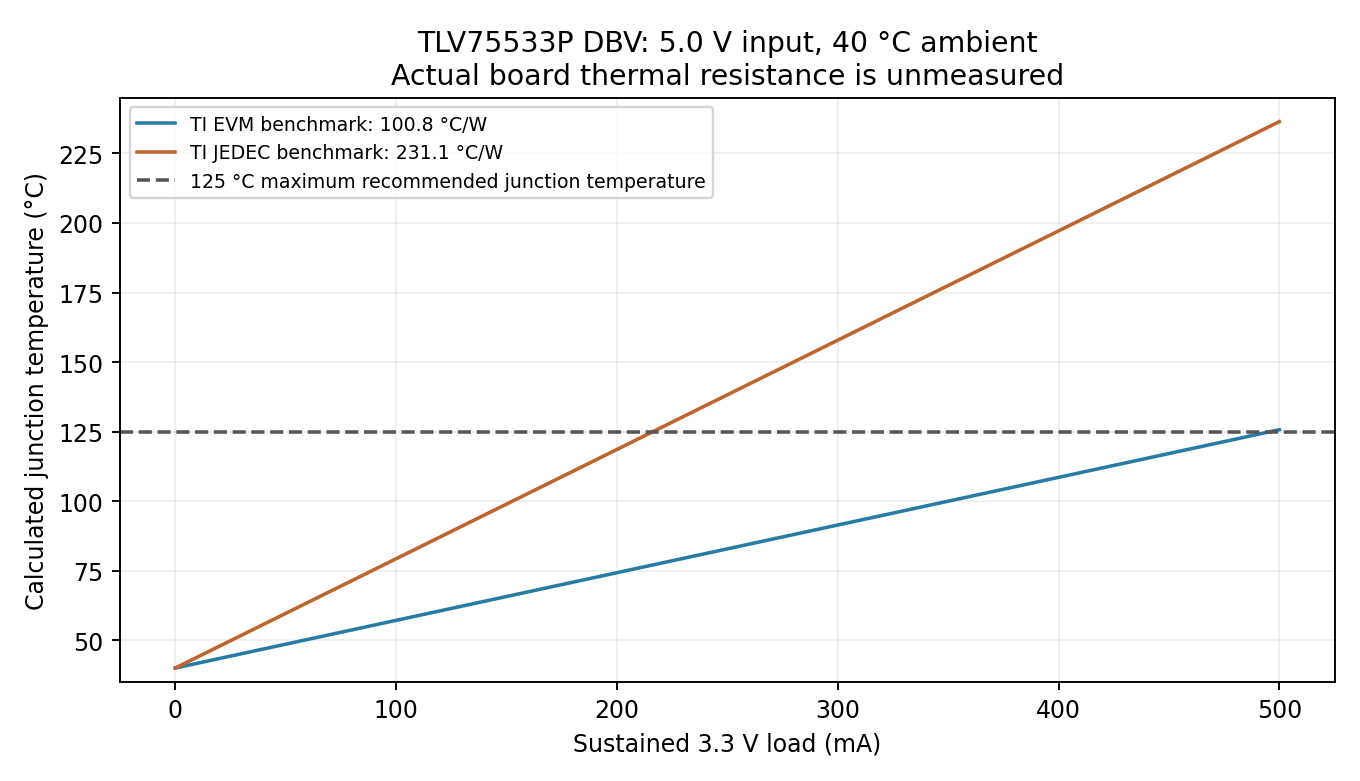
docs/audit-2026-09-16/ldo-thermal-benchmarks.png
