iandchasse/silkscreen-pcb/docs/final-review-2026-09-19/sections/img/epd_verify_tail_envelope.png

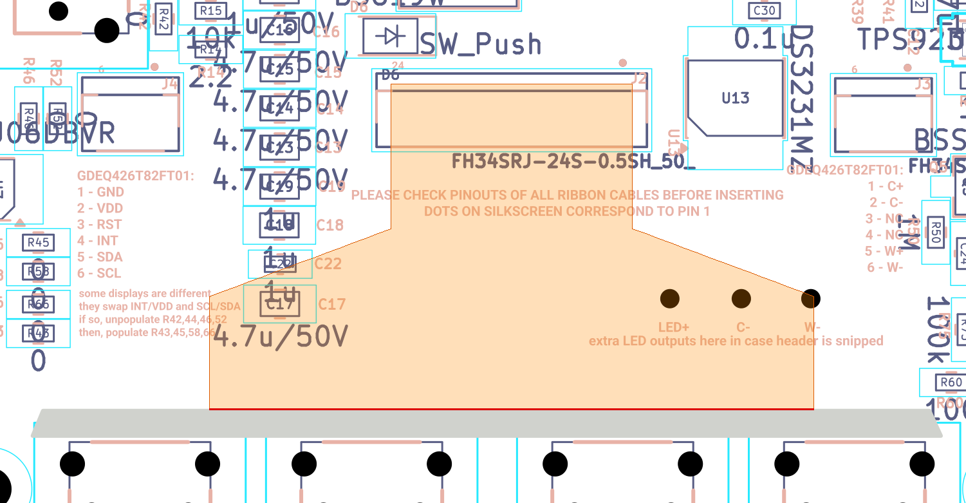
docs/final-review-2026-09-19/sections/img/epd_verify_tail_envelope.png
