iandchasse/silkscreen-pcb/docs/final-review-2026-09-19/sections/img/led_testpoints_top.png

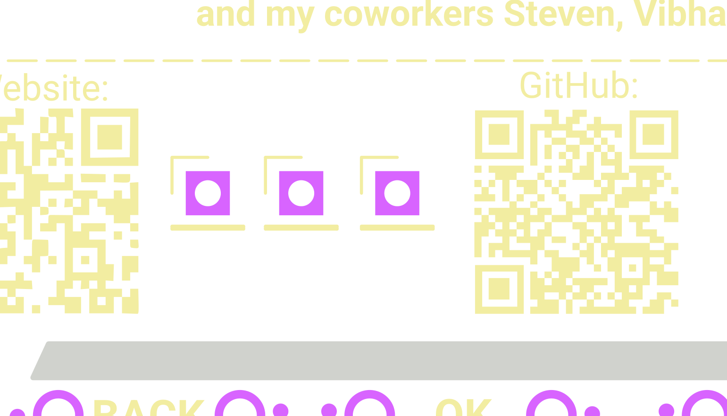
docs/final-review-2026-09-19/sections/img/led_testpoints_top.png
